schlae/HardDriveInfo/st225/20301/Analog.kicad_sch

## KiCad design st225/20301/Analog.kicad_sch (2024-07-07)

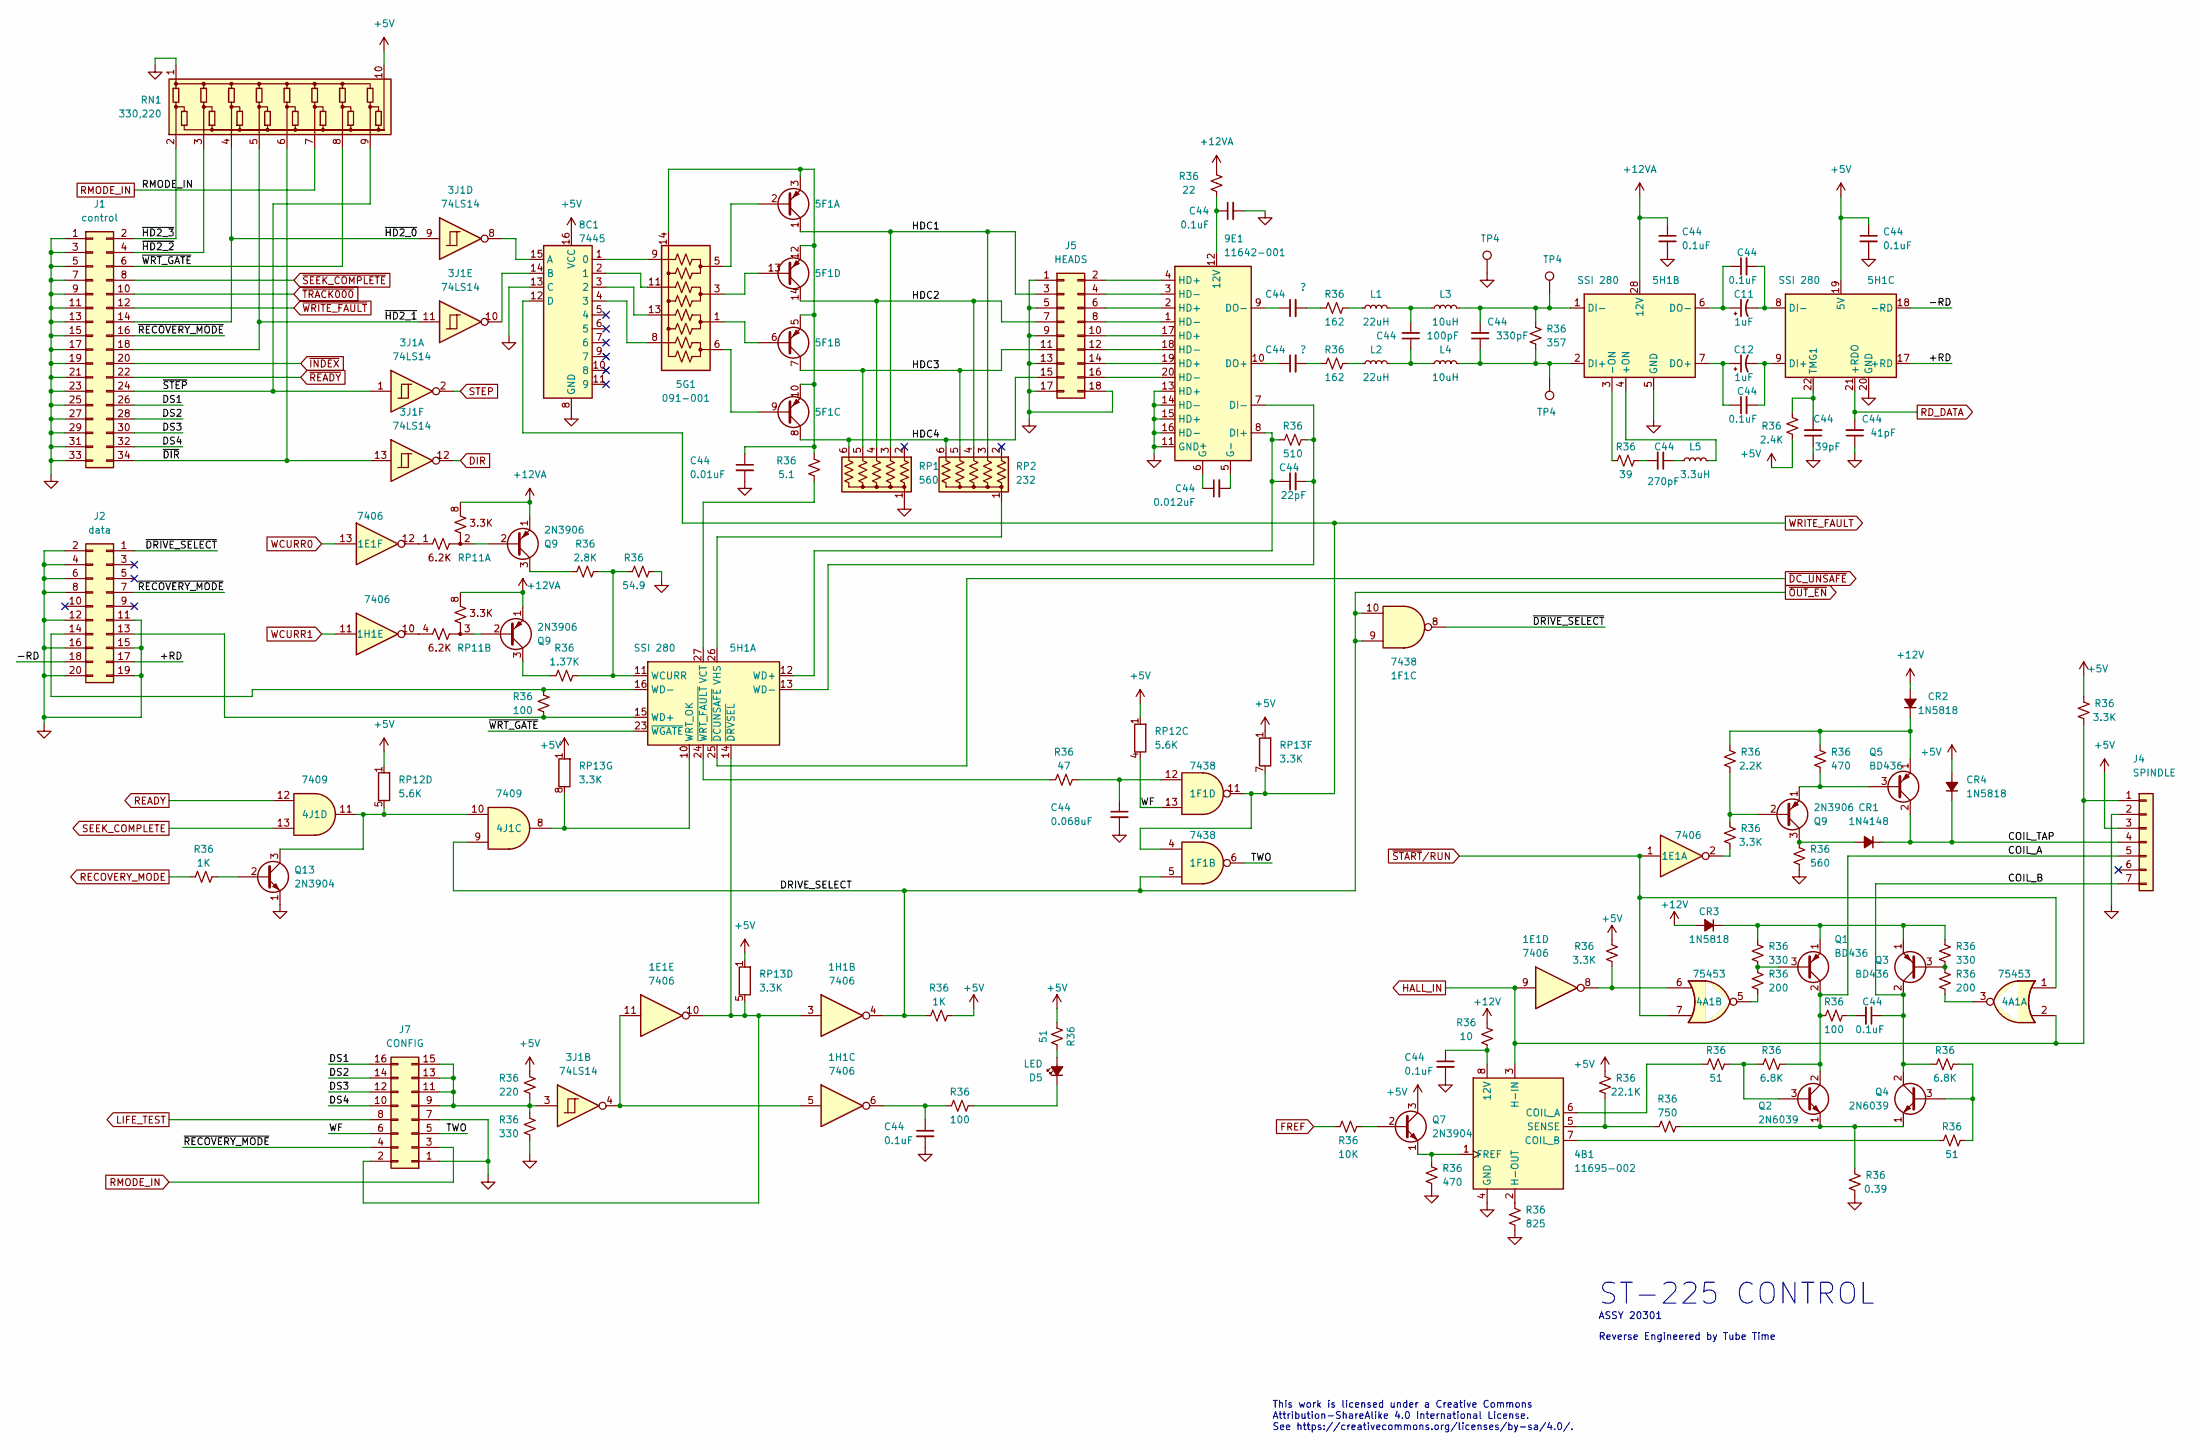
[picture p25: schematic Analog.kicad_sch]

Parts:
1E1, 1H1: 7406; DIP254P762X635-14
1F1: 7438; DIP254P762X635-14
3J1: 74LS14; DIP254P762X635-14
4A1: 75453; DIP254P762X635-8
4B1: 11695-002; DIP254P762X635-8
4J1: 7409; DIP254P762X635-14
5F1: DIP254P762X635-14
5G1: 091-001; DIP254P762X635-14
5H1: SSI 280; DIP254P1524X635-28
8C1: 7445; DIP254P762X635-16
9E1: 11642-001; DIP254P762X635-20
C11, C12: 1uF; C_Axial_L3.8mm_D2.6mm_P15.00mm_Horizontal
C44: 41pF; C_Axial_L3.8mm_D2.6mm_P10.00mm_Horizontal
CR1: 1N4148; D_DO-35_SOD27_P10.16mm_Horizontal
CR2, CR3, CR4: 1N5818; D_DO-35_SOD27_P10.16mm_Horizontal
D5: LED; PinHeader_1x02_P2.54mm_Vertical
J1: control; EDGE_34_100
J2: data; EDGE_20_100
J4: SPINDLE; PinHeader_1x07_P2.54mm_Vertical
J5: HEADS; PinHeader_2x09_P2.54mm_Horizontal
J7: CONFIG; PinHeader_2x08_P2.54mm_Horizontal
L1, L2: 22uH; L_Axial_L9.5mm_D4.0mm_P15.24mm_Horizontal_Fastron_SMCC
L3, L4: 10uH; L_Axial_L9.5mm_D4.0mm_P15.24mm_Horizontal_Fastron_SMCC
L5: 3.3uH; L_Axial_L9.5mm_D4.0mm_P15.24mm_Horizontal_Fastron_SMCC
Q1, Q3, Q5: BD436; TO-126-3_Horizontal_TabDown
Q2, Q4: 2N6039; TO-126-3_Horizontal_TabDown
Q7, Q13: 2N3904; TO-92_Wide_Reversed
Q9: 2N3906; TO-92_Wide_Reversed
R36: 2.4K; R_Axial_DIN0207_L6.3mm_D2.5mm_P10.16mm_Horizontal
RN1: 330,220; R_Array_SIP10
RP1: 560; R_Array_SIP6
RP2: 232; R_Array_SIP6
RP11: R_Array_SIP8
RP12: 5.6K; R_Array_SIP6
RP13: 3.3K; R_Array_SIP8
TP4: TestPoint; TestPoint_THTPad_1.5x1.5mm_Drill0.7mm

Connections:
+5V: 5H1.19 (5V), 8C1.16 (VCC), C44.1, CR4.2 (A), J4.3, Q7.3 (C), R36.1, R36.2, RN1.10 (COM2), RP12.1 (R1), RP13.1 (R1)
+12V: CR2.2 (A), CR3.2 (A), R36.1
+12VA: 5H1.28 (12V), C44.1, Q9.1 (E), R36.2, RP11.8
+RD: 5H1.17 (+RD), J2.17
-RD: 5H1.18 (-RD), J2.18
COIL_A: J4.5, Q1.2 (C), Q2.2 (C), R36.1, R36.2
COIL_B: C44.1, J4.7, Q3.2 (C), Q4.2 (C), R36.2
COIL_TAP: CR1.1 (K), CR4.1 (K), J4.4, Q5.2 (C)
DIR: 3J1.12
DS1: J1.26, J7.16
DS2: J1.28, J7.14
DS3: J1.30, J7.12
DS4: J1.32, J7.10
FREF: R36.2
GND: 4B1.4 (GND), 5H1.5 (GND), 5H1.20 (GND), 8C1.8 (GND), 8C1.13 (C), 9E1.11 (GND), 9E1.13 (HD+), 9E1.14 (HD-), 9E1.15 (HD+), 9E1.16 (HD-), C44.1, C44.2, J1.1, J1.3, J1.5, J1.7, J1.9, J1.11, J1.13, J1.15, J1.17, J1.19, J1.21, J1.23, J1.25, J1.27, J1.29, J1.31, J1.33, J2.2, J2.4, J2.6, J2.8, J2.11, J2.12, J2.15, J2.16, J2.19, J2.20, J4.2, J5.1, J5.5, J5.9, J5.13, J5.17, J5.18, J7.1, J7.7, Q13.1 (E), R36.1, R36.2, RN1.1 (COM1), RP1.1 (common), TP4.1
HALL_IN: 1E1.9, 4A1.2, 4B1.3 (H-IN), J4.1, R36.2
HDC1: 5F1.1 (C), J5.3, RP1.3 (R2), RP2.3 (R2)
HDC2: 5F1.14 (C), J5.7, RP1.4 (R3), RP2.4 (R3)
HDC3: 5F1.7 (C), J5.11, RP1.5 (R4), RP2.5 (R4)
HDC4: 5F1.8 (C), J5.15, RP1.6 (R5), RP2.6 (R5)
LIFE_TEST: J7.8
unnamed: 1E1.2, R36.2
unnamed: 1E1.8, 4A1.6, R36.2
unnamed: 1E1.10, 1H1.3, 5H1.14, J7.2, RP13.5 (R4.2)
unnamed: 1E1.11, 1H1.5, 3J1.4
unnamed: 1E1.12, RP11.1
unnamed: 1F1.12, C44.1, R36.1
unnamed: 1H1.6, C44.1, R36.2
unnamed: 1H1.10, RP11.4
unnamed: 3J1.3, J7.9, J7.11, J7.13, J7.15, R36.1, R36.2
unnamed: 3J1.8, 8C1.15 (A)
unnamed: 3J1.10, 8C1.14 (B)
unnamed: 4A1.3, R36.2
unnamed: 4A1.5, R36.2
unnamed: 4B1.1 (FREF), Q7.1 (E), R36.1
unnamed: 4B1.2 (H-OUT), R36.1
unnamed: 4B1.5 (SENSE), R36.2
unnamed: 4B1.6 (COIL_A), R36.2
unnamed: 4B1.7 (COIL_B), R36.2
unnamed: 4B1.8 (12V), C44.1, R36.2
unnamed: 4J1.8, 5H1.10, RP13.8 (R7.2)
unnamed: 4J1.10, 4J1.11, Q13.3 (C), RP12.5 (R4.2)
unnamed: 5F1.2 (B), 5G1.5
unnamed: 5F1.6 (B), 5G1.1
unnamed: 5F1.9 (B), 5G1.6
unnamed: 5F1.3 (E), 5F1.5 (E), 5F1.10 (E), 5F1.12 (E), 5G1.14 (9), C44.1, R36.2
unnamed: 5F1.13 (B), 5G1.3
unnamed: 5G1.8, 8C1.4 (3)
unnamed: 5G1.9, 8C1.1 (0)
unnamed: 5G1.11, 8C1.2 (1)
unnamed: 5G1.13, 8C1.3 (2)
unnamed: 5H1.1 (DI-), C44.2, L3.2, R36.1, TP4.1
unnamed: 5H1.2 (DI+), C44.1, L4.2, R36.2, TP4.1
unnamed: 5H1.3 (-ON), R36.2
unnamed: 5H1.4 (+ON), L5.2
unnamed: 5H1.6 (DO-), C11.1, C44.1
unnamed: 5H1.7 (DO+), C12.1, C44.1
unnamed: 5H1.8 (DI-), C11.2, C44.2
unnamed: 5H1.9 (DI+), C12.2, C44.2
unnamed: 5H1.11 (WC), R36.1, R36.2
unnamed: 5H1.12 (WD), 9E1.8 (DI+), C44.1, R36.2
unnamed: 5H1.13 (WD), 9E1.7 (DI-), C44.2, R36.1
unnamed: 5H1.15 (+WD), J2.13, R36.2
unnamed: 5H1.16 (-WD), J2.14, R36.1
unnamed: 5H1.22 (TMG1), C44.2, R36.1
unnamed: 5H1.24, R36.2
unnamed: 5H1.26 (VHS), RP2.1 (common)
unnamed: 5H1.27 (VCT), R36.1
unnamed: 9E1.1 (HD-), J5.8
unnamed: 9E1.2 (HD+), J5.6
unnamed: 9E1.3 (HD-), J5.4
unnamed: 9E1.4 (HD+), J5.2
unnamed: 9E1.5 (G-), C44.2
unnamed: 9E1.6 (G+), C44.1
unnamed: 9E1.9 (DO-), C44.1
unnamed: 9E1.10 (DO+), C44.1
unnamed: 9E1.12 (12V), C44.1, R36.1
unnamed: 9E1.17 (HD+), J5.10
unnamed: 9E1.18 (HD-), J5.12
unnamed: 9E1.19 (HD+), J5.14
unnamed: 9E1.20 (HD-), J5.16
unnamed: C44.1, L2.2, L4.1, L5.1
unnamed: C44.2, L1.2, L3.1, R36.1, R36.2
unnamed: CR1.2 (A), Q9.3 (C), R36.1
unnamed: CR2.1 (K), Q5.1 (E), R36.1
unnamed: CR3.1 (K), Q1.1 (E), Q3.1 (E), R36.1
unnamed: D5.1 (K), R36.1
unnamed: D5.2 (A), R36.1
unnamed: L1.1, R36.1
unnamed: L2.1, R36.1
unnamed: Q1.3 (B), R36.1, R36.2
unnamed: Q2.1 (E), Q4.1 (E), R36.1
unnamed: Q2.3 (B), R36.1, R36.2
unnamed: Q3.3 (B), R36.1, R36.2
unnamed: Q4.3 (B), R36.1
unnamed: Q5.3 (B), Q9.1 (E), R36.2
unnamed: Q7.2 (B), R36.1
unnamed: Q9.2 (B), R36.1, R36.2, RP11.2, RP11.3
unnamed: Q9.3 (C), R36.2
unnamed: Q13.2 (B), R36.1
RD_DATA: 5H1.21 (+RDO), C44.2
READY: 4J1.12
RECOVERY_MODE: R36.2
RMODE_IN: J7.3, RN1.7 (R6)
SEEK_COMPLETE: 4J1.13
STEP: 3J1.2
TWO: 1F1.6, J7.5
WCURR0: 1E1.13
WCURR1: 1H1.11
WF: 1F1.13, J7.6, RP12.4 (R3.2)
WRITE_FAULT: 1F1.4, 1F1.11, 8C1.12 (D), RP13.7 (R6.2)
~DC_UNSAFE: 5H1.25
~DIR: 3J1.13, J1.34, RN1.6 (R5)
~DRIVE_SELECT: 1F1.8, J2.1
~HD2_0: 3J1.9, J1.14, RN1.4 (R3)
~HD2_1: 3J1.11, J1.18, RN1.5 (R4)
~HD2_2: J1.4, RN1.3 (R2)
~HD2_3: J1.2, RN1.2 (R1)
~INDEX: J1.20
~OUT_EN: 1F1.5, 1F1.9, 1F1.10, 1H1.4, 4J1.9, R36.2
~READY: J1.22
~RECOVERY_MODE: J1.16, J2.7, J7.4
~SEEK_COMPLETE: J1.8
~START/RUN: 1E1.1, 4A1.1, 4A1.7
~STEP: 3J1.1, J1.24, RN1.9 (R8)
~TRACK000: J1.10
~WRITE_FAULT: J1.12
~WRT_GATE: 5H1.23 (~WG), J1.6, RN1.8 (R7)

Notes on the sheet:
ST-225 CONTROL
Reverse Engineered by Tube Time
ASSY 20301
This work is licensed under a Creative Commons Attribution-ShareAlike 4.0 International License. See https://creativecommons.org/licenses/by-sa/4.0/.
