schlae/HardDriveInfo/st225/20301/DigitalStepper.kicad_sch

## KiCad design st225/20301/DigitalStepper.kicad_sch (2024-07-07)

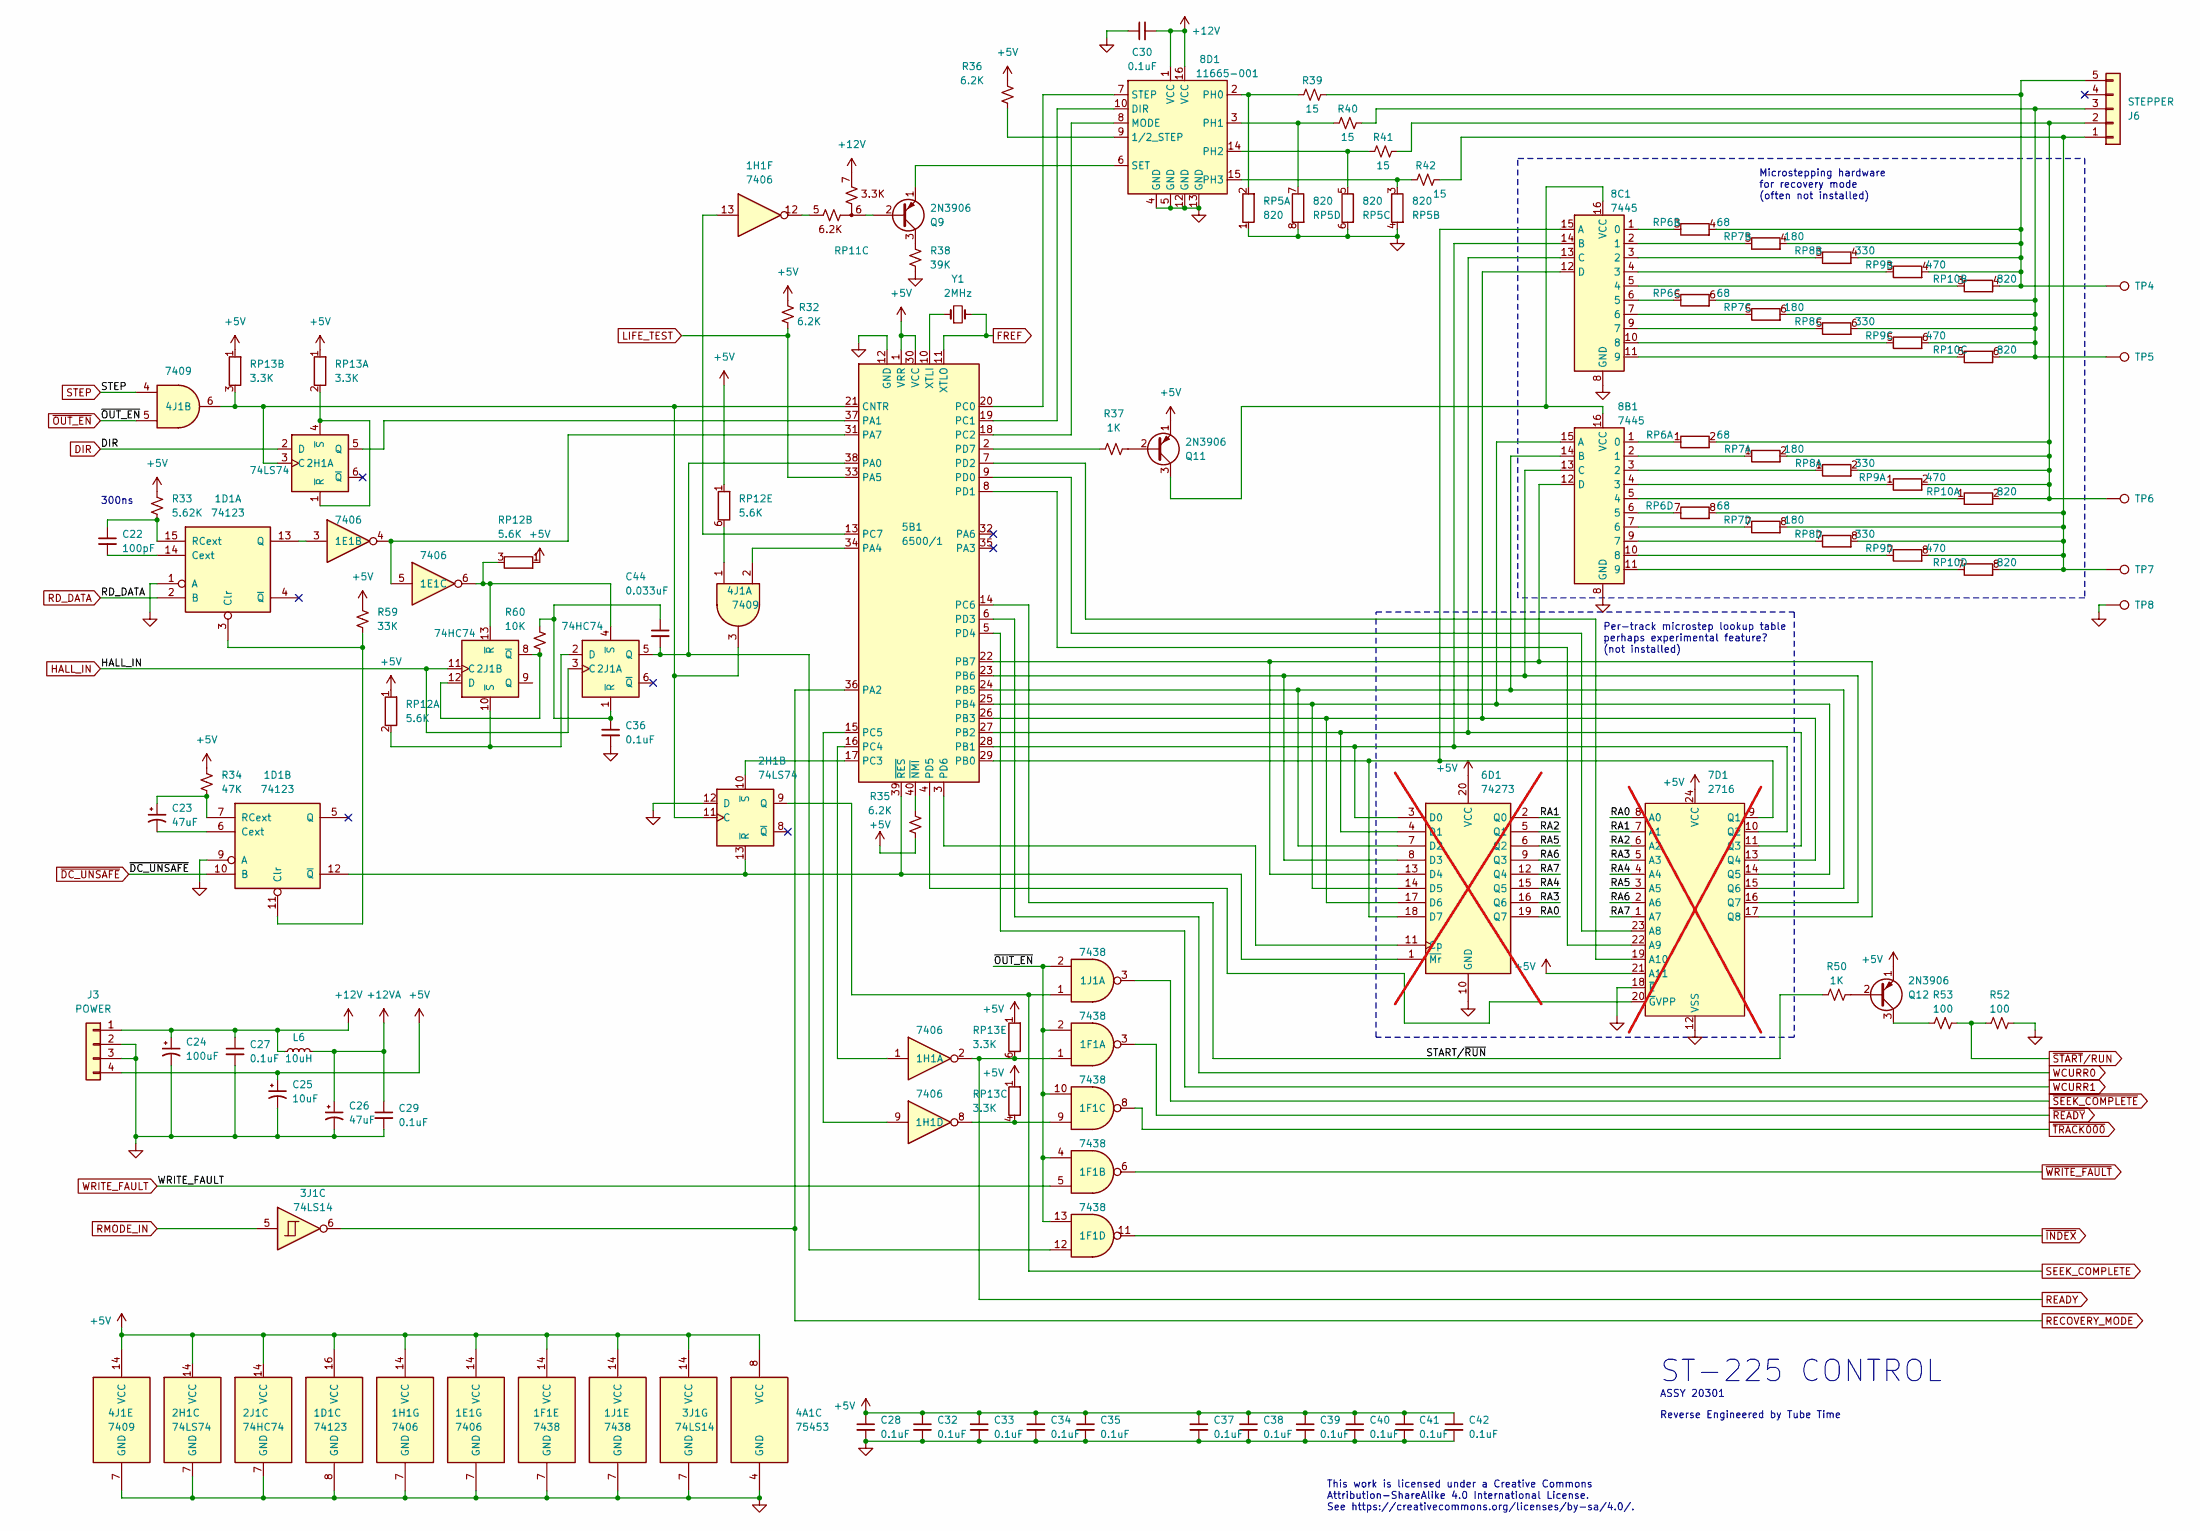
[picture p26: schematic DigitalStepper.kicad_sch]

Parts:
1D1: 74123; DIP254P762X635-16
1E1, 1H1: 7406; DIP254P762X635-14
1F1, 1J1: 7438; DIP254P762X635-14
2H1: 74LS74; DIP254P762X635-14
2J1: 74HC74; DIP254P762X635-14
3J1: 74LS14; DIP254P762X635-14
4A1: 75453; DIP254P762X635-8
4J1: 7409; DIP254P762X635-14
5B1: 6500/1; DIP254P1524X635-40
6D1: 74273; DIP254P762X635-20; not fitted
7D1: 2716; DIP254P1524X635-24; not fitted
8B1, 8C1: 7445; DIP254P762X635-16
8D1: 11665-001; DIP254P762X635-16
C22: 100pF; C_Axial_L3.8mm_D2.6mm_P10.00mm_Horizontal
C23, C26: 47uF; C_Axial_L5.1mm_D3.1mm_P15.00mm_Horizontal
C24: 100uF; C_Axial_L12.0mm_D6.5mm_P20.00mm_Horizontal
C25: 10uF; C_Axial_L5.1mm_D3.1mm_P15.00mm_Horizontal
C27, C28, C29, C30, C32, C33, C34, C35, C36, C37, C38, C39, C40, C41, C42: 0.1uF; C_Axial_L3.8mm_D2.6mm_P10.00mm_Horizontal
C44: 0.033uF; C_Axial_L3.8mm_D2.6mm_P10.00mm_Horizontal
J3: POWER; Samtec_HPM-04-01-x-S_Straight_1x04_Pitch5.08mm
J6: STEPPER; PinHeader_1x05_P2.54mm_Vertical
L6: 10uH; L_Axial_L9.5mm_D4.0mm_P15.24mm_Horizontal_Fastron_SMCC
Q9, Q11, Q12: 2N3906; TO-92_Wide_Reversed
R32, R35, R36: 6.2K; R_Axial_DIN0207_L6.3mm_D2.5mm_P10.16mm_Horizontal
R33: 5.62K; R_Axial_DIN0207_L6.3mm_D2.5mm_P10.16mm_Horizontal
R34: 47K; R_Axial_DIN0207_L6.3mm_D2.5mm_P10.16mm_Horizontal
R37, R50: 1K; R_Axial_DIN0207_L6.3mm_D2.5mm_P10.16mm_Horizontal
R38: 39K; R_Axial_DIN0207_L6.3mm_D2.5mm_P10.16mm_Horizontal
R39, R40, R41, R42: 15; R_Axial_DIN0309_L9.0mm_D3.2mm_P20.32mm_Horizontal
R52, R53: 100; R_Axial_DIN0207_L6.3mm_D2.5mm_P10.16mm_Horizontal
R59: 33K; R_Axial_DIN0207_L6.3mm_D2.5mm_P10.16mm_Horizontal
R60: 10K; R_Axial_DIN0204_L3.6mm_D1.6mm_P7.62mm_Horizontal
RP5, RP10: 820; R_Array_SIP8
RP6: 68; R_Array_SIP8
RP7: 180; R_Array_SIP8
RP8: 330; R_Array_SIP8
RP9: 470; R_Array_SIP8
RP11: R_Array_SIP8
RP12: 5.6K; R_Array_SIP6
RP13: 3.3K; R_Array_SIP8
TP4, TP5, TP6, TP7, TP8: TestPoint; TestPoint_THTPad_D1.5mm_Drill0.7mm
Y1: 2MHz; Crystal_HC49-U_Horizontal

Connections:
+5V: 1D1.16 (VCC), 1E1.14 (VCC), 1F1.14 (VCC), 1H1.14 (VCC), 1J1.14 (VCC), 2H1.14 (VCC), 2J1.14 (VCC), 3J1.14 (VCC), 4A1.8 (VCC), 4J1.14 (VCC), 5B1.1 (VRR), 5B1.30 (VCC), 6D1.20 (VCC), 7D1.21 (A11), 7D1.24 (VCC), C25.1, C28.1, C32.1, C33.1, C34.1, C35.1, C37.1, C38.1, C39.1, C40.1, C41.1, C42.1, J3.4, Q11.1 (E), Q12.1 (E), R32.1, R33.1, R34.1, R35.1, R36.2, R59.1, RP12.1 (R1), RP13.1 (R1)
+12V: 8D1.1 (VCC), 8D1.16 (VCC), C24.1, C27.1, C30.2, J3.1, L6.1, RP11.7
+12VA: C26.1, C29.1, L6.2
DIR: 2H1.2 (D)
FREF: 5B1.11 (XTLO), Y1.2
GND: 1D1.1 (A), 1D1.8 (GND), 1D1.9 (A), 1E1.7 (GND), 1F1.7 (GND), 1H1.7 (GND), 1J1.7 (GND), 2H1.7 (GND), 2H1.12 (D), 2J1.7 (GND), 3J1.7 (GND), 4A1.4 (GND), 4J1.7 (GND), 5B1.12 (GND), 6D1.10 (GND), 7D1.12 (VSS), 7D1.18 (~E), 8B1.8 (GND), 8C1.8 (GND), 8D1.4 (GND), 8D1.5 (GND), 8D1.12 (GND), 8D1.13 (GND), C24.2, C25.2, C26.2, C27.2, C28.2, C29.2, C30.1, C32.2, C33.2, C34.2, C35.2, C36.2, C37.2, C38.2, C39.2, C40.2, C41.2, C42.2, J3.2, J3.3, R38.2, R52.1, RP5.1 (R1.1), RP5.4 (R2.2), RP5.6 (R3.2), RP5.8 (R4.2), TP8.1
HALL_IN: 2J1.3 (C), 2J1.11 (C)
LIFE_TEST: 5B1.33 (PA5), R32.2
unnamed: 1D1.6 (Cext), C23.2
unnamed: 1D1.7 (RCext), C23.1, R34.2
unnamed: 1D1.3 (Clr), 1D1.11 (Clr), R59.2
unnamed: 1D1.12 (~Q), 2H1.13 (~R), 5B1.39 (~RES), 6D1.1 (~Mr)
unnamed: 1D1.13 (Q), 1E1.3
unnamed: 1D1.14 (Cext), C22.2
unnamed: 1D1.15 (RCext), C22.1, R33.2
unnamed: 1E1.4, 1E1.5, 5B1.31 (PA7)
unnamed: 1E1.6, 2J1.4 (~S), 2J1.13 (~R), RP12.3 (R2.2)
unnamed: 1F1.9, 1H1.8, RP13.4 (R3.2)
unnamed: 1F1.12, 2J1.5 (Q), 5B1.38 (PA0), C44.2
unnamed: 1H1.1, 5B1.16 (PC4)
unnamed: 1H1.9, 5B1.15 (PC5)
unnamed: 1H1.12, RP11.5
unnamed: 1H1.13, 5B1.13 (PC7)
unnamed: 2H1.1 (~R), 2H1.4 (~S), RP13.2 (R1.2)
unnamed: 2H1.5 (Q), 5B1.37 (PA1)
unnamed: 2H1.10 (~S), 5B1.17 (PC3)
unnamed: 2H1.3 (C), 2H1.11 (C), 4J1.3, 4J1.6, 5B1.21 (CNTR), RP13.3 (R2.2)
unnamed: 2J1.1 (~R), C36.1, C44.1, R60.1
unnamed: 2J1.2 (D), 2J1.10 (~S), RP12.2 (R1.2)
unnamed: 2J1.8 (~Q), 2J1.12 (D), R60.2
unnamed: 4J1.1, RP12.6 (R5.2)
unnamed: 4J1.2, 5B1.34 (PA4)
unnamed: 5B1.2 (PD7), R37.1
unnamed: 5B1.3 (PD6), 6D1.11 (Cp)
unnamed: 5B1.4 (PD5), 7D1.20 (~GVPP)
unnamed: 5B1.7 (PD2), 7D1.19 (A10)
unnamed: 5B1.8 (PD1), 7D1.22 (A9)
unnamed: 5B1.9 (PD0), 7D1.23 (A8)
unnamed: 5B1.10 (XTLI), Y1.1
unnamed: 5B1.18 (PC2), 8D1.8 (MODE)
unnamed: 5B1.19 (PC1), 8D1.10 (DIR)
unnamed: 5B1.20 (PC0), 8D1.7 (STEP)
unnamed: 5B1.22 (PB7), 6D1.13 (D4), 7D1.17 (Q8), 8B1.12 (D)
unnamed: 5B1.23 (PB6), 6D1.8 (D3), 7D1.16 (Q7), 8B1.13 (C)
unnamed: 5B1.24 (PB5), 6D1.7 (D2), 7D1.15 (Q6), 8B1.14 (B)
unnamed: 5B1.25 (PB4), 6D1.14 (D5), 7D1.14 (Q5), 8B1.15 (A)
unnamed: 5B1.26 (PB3), 6D1.17 (D6), 7D1.13 (Q4), 8C1.12 (D)
unnamed: 5B1.27 (PB2), 6D1.4 (D1), 7D1.11 (Q3), 8C1.13 (C)
unnamed: 5B1.28 (PB1), 6D1.3 (D0), 7D1.10 (Q2), 8C1.14 (B)
unnamed: 5B1.29 (PB0), 6D1.18 (D7), 7D1.9 (Q1), 8C1.15 (A)
unnamed: 5B1.40 (~NMI), R35.2
unnamed: 8B1.1 (0), RP6.1 (R1.1)
unnamed: 8B1.2 (1), RP7.1 (R1.1)
unnamed: 8B1.3 (2), RP8.1 (R1.1)
unnamed: 8B1.4 (3), RP9.1 (R1.1)
unnamed: 8B1.5 (4), RP10.1 (R1.1)
unnamed: 8B1.6 (5), RP6.7 (R4.1)
unnamed: 8B1.7 (6), RP7.7 (R4.1)
unnamed: 8B1.9 (7), RP8.7 (R4.1)
unnamed: 8B1.10 (8), RP9.7 (R4.1)
unnamed: 8B1.11 (9), RP10.7 (R4.1)
unnamed: 8B1.16 (VCC), 8C1.16 (VCC), Q11.3 (C)
unnamed: 8C1.1 (0), RP6.3 (R2.1)
unnamed: 8C1.2 (1), RP7.3 (R2.1)
unnamed: 8C1.3 (2), RP8.3 (R2.1)
unnamed: 8C1.4 (3), RP9.3 (R2.1)
unnamed: 8C1.5 (4), RP10.3 (R2.1)
unnamed: 8C1.6 (5), RP6.5 (R3.1)
unnamed: 8C1.7 (6), RP7.5 (R3.1)
unnamed: 8C1.9 (7), RP8.5 (R3.1)
unnamed: 8C1.10 (8), RP9.5 (R3.1)
unnamed: 8C1.11 (9), RP10.5 (R3.1)
unnamed: 8D1.2 (PH0), R39.1, RP5.2 (R1.2)
unnamed: 8D1.3 (PH1), R40.1, RP5.7 (R4.1)
unnamed: 8D1.6 (SET), Q9.1 (E)
unnamed: 8D1.9 (1/2_STEP), R36.1
unnamed: 8D1.14 (PH2), R41.1, RP5.5 (R3.1)
unnamed: 8D1.15 (PH3), R42.1, RP5.3 (R2.1)
unnamed: J6.1, R42.2, RP6.8 (R4.2), RP7.8 (R4.2), RP8.8 (R4.2), RP9.8 (R4.2), RP10.8 (R4.2), TP7.1
unnamed: J6.2, R41.2, RP6.2 (R1.2), RP7.2 (R1.2), RP8.2 (R1.2), RP9.2 (R1.2), RP10.2 (R1.2), TP6.1
unnamed: J6.3, R40.2, RP6.6 (R3.2), RP7.6 (R3.2), RP8.6 (R3.2), RP9.6 (R3.2), RP10.6 (R3.2), TP5.1
unnamed: J6.5, R39.2, RP6.4 (R2.2), RP7.4 (R2.2), RP8.4 (R2.2), RP9.4 (R2.2), RP10.4 (R2.2), TP4.1
unnamed: Q9.2 (B), RP11.6
unnamed: Q9.3 (C), R38.1
unnamed: Q11.2 (B), R37.2
unnamed: Q12.2 (B), R50.1
unnamed: Q12.3 (C), R53.2
RA0: 6D1.19 (Q7), 7D1.8 (A0)
RA1: 6D1.2 (Q0), 7D1.7 (A1)
RA2: 6D1.5 (Q1), 7D1.6 (A2)
RA3: 6D1.16 (Q6), 7D1.5 (A3)
RA4: 6D1.15 (Q5), 7D1.4 (A4)
RA5: 6D1.6 (Q2), 7D1.3 (A5)
RA6: 6D1.9 (Q3), 7D1.2 (A6)
RA7: 6D1.12 (Q4), 7D1.1 (A7)
RD_DATA: 1D1.2 (B)
READY: 1F1.1, 1H1.2, RP13.6 (R5.2)
RECOVERY_MODE: 3J1.6, 5B1.36 (PA2)
RMODE_IN: 3J1.5
SEEK_COMPLETE: 1J1.1, 2H1.9 (Q)
START/~RUN: 5B1.14 (PC6), R50.2
STEP: 4J1.4
WCURR0: 5B1.6 (PD3)
WCURR1: 5B1.5 (PD4)
WRITE_FAULT: 1F1.5
~DC_UNSAFE: 1D1.10 (B)
~INDEX: 1F1.11
~OUT_EN: 1F1.2, 1F1.4, 1F1.10, 1F1.13, 1J1.2, 4J1.5
~READY: 1F1.3
~SEEK_COMPLETE: 1J1.3
~START/RUN: R52.2, R53.1
~TRACK000: 1F1.8
~WRITE_FAULT: 1F1.6

Notes on the sheet:
Microstepping hardware for recovery mode (often not installed)
This work is licensed under a Creative Commons Attribution-ShareAlike 4.0 International License. See https://creativecommons.org/licenses/by-sa/4.0/.
ASSY 20301
300ns
Reverse Engineered by Tube Time
Per-track microstep lookup table perhaps experimental feature? (not installed)
ST-225 CONTROL
