schlae/HardDriveInfo/st225/20527/Analog.kicad_sch

## KiCad design st225/20527/Analog.kicad_sch (2024-06-30)

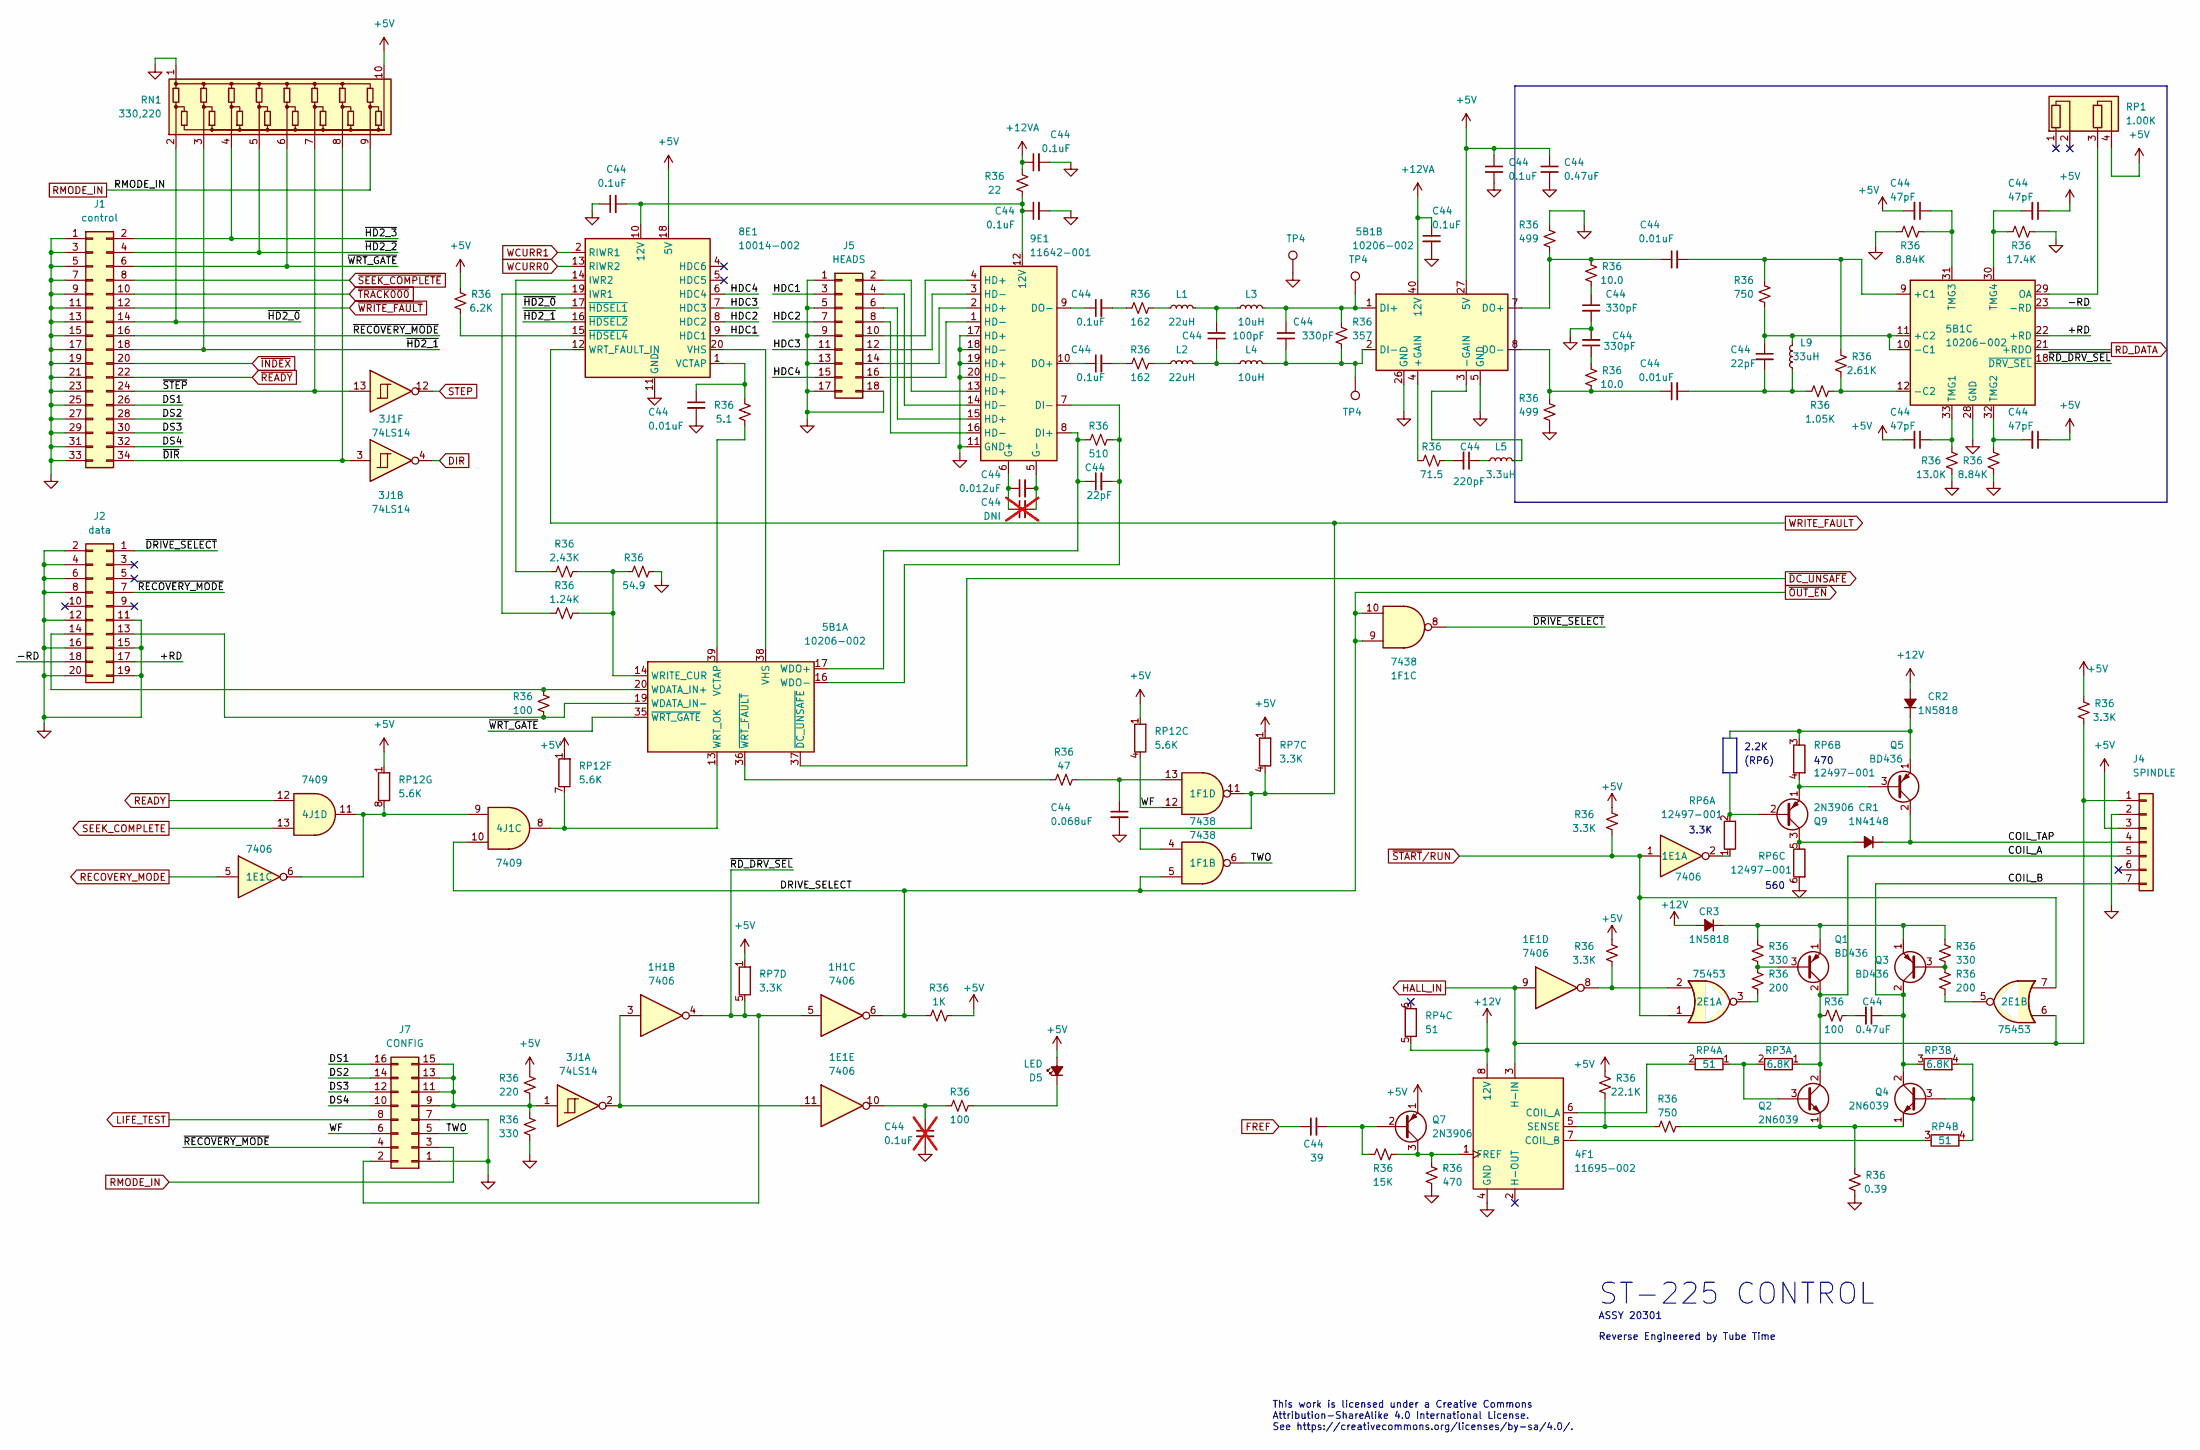
[picture p27: schematic Analog.kicad_sch]

Parts:
1E1, 1H1: 7406; DIP254P762X635-14
1F1: 7438; DIP254P762X635-14
2E1: 75453; DIP254P762X635-8
3J1: 74LS14; DIP254P762X635-14
4F1: 11695-002; DIP254P762X635-8
4J1: 7409; DIP254P762X635-14
5B1: 10206-002; DIP254P1524X635-40
8E1: 10014-002; DIP254P762X635-20
9E1: 11642-001; DIP254P762X635-20
C44: 47pF; C_Axial_L3.8mm_D2.6mm_P10.00mm_Horizontal
CR1: 1N4148; D_DO-35_SOD27_P10.16mm_Horizontal
CR2, CR3: 1N5818; D_DO-35_SOD27_P10.16mm_Horizontal
D5: LED; PinHeader_1x02_P2.54mm_Vertical
J1: control; EDGE_34_100
J2: data; EDGE_20_100
J4: SPINDLE; PinHeader_1x07_P2.54mm_Vertical
J5: HEADS; PinHeader_2x09_P2.54mm_Horizontal
J7: CONFIG; PinHeader_2x08_P2.54mm_Horizontal
L1, L2: 22uH; L_Axial_L9.5mm_D4.0mm_P15.24mm_Horizontal_Fastron_SMCC
L3, L4: 10uH; L_Axial_L9.5mm_D4.0mm_P15.24mm_Horizontal_Fastron_SMCC
L5: 3.3uH; L_Axial_L9.5mm_D4.0mm_P12.70mm_Horizontal_Fastron_SMCC
L9: 33uH; L_Axial_L9.5mm_D4.0mm_P15.24mm_Horizontal_Fastron_SMCC
Q1, Q3, Q5: BD436; TO-126-3_Horizontal_TabDown
Q2, Q4: 2N6039; TO-126-3_Horizontal_TabDown
Q7, Q9: 2N3906; TO-92L_Inline_Wide
R36: 13.0K; R_Axial_DIN0207_L6.3mm_D2.5mm_P10.16mm_Horizontal
RN1: 330,220; R_Array_SIP10
RP1: 1.00K; R_Array_SIP4
RP3: 6.8K; R_Array_SIP4
RP4: 51; R_Array_SIP6
RP6: 12497-001; R_Array_SIP6
RP7: 3.3K; R_Array_SIP6
RP12: 5.6K; R_Array_SIP8
TP4: TestPoint; TestPoint_THTPad_1.5x1.5mm_Drill0.7mm

Connections:
+5V: 5B1.27 (5V), 8E1.18 (5V), C44.1, C44.2, D5.2 (A), J4.3, Q7.1 (E), R36.1, RN1.10 (COM2), RP1.4 (R2.2), RP7.1 (R1), RP12.1 (R1)
+12V: 4F1.8 (12V), CR2.2 (A), CR3.2 (A), RP4.5 (R3.1)
+12VA: 5B1.40 (12V), C44.1, R36.2
+RD: 5B1.22 (+RD), J2.17
-RD: 5B1.23 (-RD), J2.18
COIL_A: J4.5, Q1.2 (C), Q2.2 (C), R36.2, RP3.1 (R1.1)
COIL_B: C44.1, J4.7, Q3.2 (C), Q4.2 (C), RP3.3 (R2.1)
COIL_TAP: CR1.1 (K), J4.4, Q5.2 (C)
DIR: 3J1.4
DS1: J1.26, J7.16
DS2: J1.28, J7.14
DS3: J1.30, J7.12
DS4: J1.32, J7.10
FREF: C44.1
GND: 4F1.4 (GND), 5B1.5 (GND), 5B1.26 (GND), 5B1.28 (GND), 8E1.11 (GND), 9E1.11 (GND), 9E1.17 (HD+), 9E1.18 (HD-), 9E1.19 (HD+), 9E1.20 (HD-), C44.1, C44.2, J1.1, J1.3, J1.5, J1.7, J1.9, J1.11, J1.13, J1.15, J1.17, J1.19, J1.21, J1.23, J1.25, J1.27, J1.29, J1.31, J1.33, J2.2, J2.4, J2.6, J2.8, J2.11, J2.12, J2.15, J2.16, J2.19, J2.20, J4.2, J5.1, J5.5, J5.9, J5.13, J5.17, J5.18, J7.1, J7.7, R36.1, R36.2, RN1.1 (COM1), RP6.6 (R3.2), TP4.1
HALL_IN: 1E1.9, 2E1.6, 4F1.3 (H-IN), J4.1, R36.2
HDC1: 8E1.9 (HDC1), J5.3
HDC2: 8E1.8 (HDC2), J5.7
HDC3: 8E1.7 (HDC3), J5.11
HDC4: 8E1.6 (HDC4), J5.15
LIFE_TEST: J7.8
unnamed: 1E1.2, RP6.1 (R1.1)
unnamed: 1E1.6, 4J1.9, 4J1.11, RP12.8 (R7.2)
unnamed: 1E1.8, 2E1.2, R36.2
unnamed: 1E1.10, C44.1, R36.2
unnamed: 1E1.11, 1H1.3, 3J1.2
unnamed: 1F1.13, C44.1, R36.1
unnamed: 2E1.3, R36.2
unnamed: 2E1.5, R36.2
unnamed: 3J1.1, J7.9, J7.11, J7.13, J7.15, R36.1, R36.2
unnamed: 4F1.1 (FREF), Q7.3 (C), R36.1
unnamed: 4F1.5 (SENSE), R36.2
unnamed: 4F1.6 (COIL_A), RP4.2 (R1.2)
unnamed: 4F1.7 (COIL_B), RP4.3 (R2.1)
unnamed: 4J1.8, 5B1.13 (WRT_OK), RP12.7 (R6.2)
unnamed: 5B1.1 (DI+), C44.2, L3.2, R36.1, TP4.1
unnamed: 5B1.2 (DI-), C44.1, L4.2, R36.2, TP4.1
unnamed: 5B1.3 (-GAIN), L5.2
unnamed: 5B1.4 (+GAIN), R36.2
unnamed: 5B1.7 (DO+), C44.1, R36.1, R36.2
unnamed: 5B1.8 (DO-), C44.1, R36.1
unnamed: 5B1.9 (+C1), C44.2, R36.1
unnamed: 5B1.10 (-C1), 5B1.11 (+C2), C44.1, L9.2, R36.2
unnamed: 5B1.12 (-C2), R36.1, R36.2
unnamed: 5B1.14 (WRITE_CUR), R36.1, R36.2
unnamed: 5B1.16 (WDO-), 9E1.7 (DI-), C44.2, R36.1
unnamed: 5B1.17 (WDO+), 9E1.8 (DI+), C44.1, R36.2
unnamed: 5B1.19 (WDATA_IN-), J2.13, R36.2
unnamed: 5B1.20 (WDATA_IN+), J2.14, R36.1
unnamed: 5B1.29 (OA), RP1.3 (R2.1)
unnamed: 5B1.30 (TMG4), C44.2, R36.1
unnamed: 5B1.31 (TMG3), C44.1, R36.2
unnamed: 5B1.32 (TMG2), C44.2, R36.1
unnamed: 5B1.33 (TMG1), C44.1, R36.1
unnamed: 5B1.36 (~WRT_FAULT), R36.2
unnamed: 5B1.38 (VHS), 8E1.20 (VHS)
unnamed: 5B1.39 (VCTAP), R36.1
unnamed: 8E1.1 (VCTAP), C44.1, R36.2
unnamed: 8E1.10 (12V), 9E1.12 (12V), C44.1, C44.2, R36.1
unnamed: 8E1.14 (IWR2), R36.2
unnamed: 8E1.15 (~HDSEL4), R36.2
unnamed: 8E1.19 (IWR1), R36.2
unnamed: 9E1.1 (HD-), J5.16
unnamed: 9E1.2 (HD+), J5.14
unnamed: 9E1.3 (HD-), J5.12
unnamed: 9E1.4 (HD+), J5.10
unnamed: 9E1.5 (G-), C44.2
unnamed: 9E1.6 (G+), C44.1
unnamed: 9E1.9 (DO-), C44.1
unnamed: 9E1.10 (DO+), C44.1
unnamed: 9E1.13 (HD+), J5.2
unnamed: 9E1.14 (HD-), J5.4
unnamed: 9E1.15 (HD+), J5.6
unnamed: 9E1.16 (HD-), J5.8
unnamed: C44.1, L2.2, L4.1, L5.1, R36.2
unnamed: C44.2, L1.2, L3.1, L9.1, Q7.2 (B), R36.1, R36.2
unnamed: CR1.2 (A), Q9.3 (C), RP6.5 (R3.1)
unnamed: CR2.1 (K), Q5.1 (E), RP6.3 (R2.1)
unnamed: CR3.1 (K), Q1.1 (E), Q3.1 (E), R36.1
unnamed: D5.1 (K), R36.1
unnamed: L1.1, R36.1
unnamed: L2.1, R36.1
unnamed: Q1.3 (B), R36.1, R36.2
unnamed: Q2.1 (E), Q4.1 (E), R36.1
unnamed: Q2.3 (B), RP3.2 (R1.2), RP4.1 (R1.1)
unnamed: Q3.3 (B), R36.1, R36.2
unnamed: Q4.3 (B), RP3.4 (R2.2), RP4.4 (R2.2)
unnamed: Q5.3 (B), Q9.1 (E), RP6.4 (R2.2)
unnamed: Q9.2 (B), RP6.2 (R1.2)
RD_DATA: 5B1.21 (+RDO)
READY: 4J1.12
RECOVERY_MODE: 1E1.5
RMODE_IN: J7.3, RN1.9 (R8)
SEEK_COMPLETE: 4J1.13
STEP: 3J1.12
TWO: 1F1.6, J7.5
WCURR0: 8E1.13 (RIWR2)
WCURR1: 8E1.2 (RIWR1)
WF: 1F1.12, J7.6, RP12.4 (R3.2)
WRITE_FAULT: 1F1.4, 1F1.11, 8E1.12 (WRT_FAULT_IN), RP7.4 (R3.2)
~DC_UNSAFE: 5B1.37 (~DC_UNSAFE)
~DIR: 3J1.3, J1.34, RN1.8 (R7)
~DRIVE_SELECT: 1F1.8, J2.1
~HD2_0: 8E1.17 (~HDSEL1), J1.14, RN1.2 (R1)
~HD2_1: 8E1.16 (~HDSEL2), J1.18, RN1.3 (R2)
~HD2_2: J1.4, RN1.5 (R4)
~HD2_3: J1.2, RN1.4 (R3)
~INDEX: J1.20
~OUT_EN: 1F1.5, 1F1.9, 1F1.10, 1H1.6, 4J1.10, R36.2
~RD_DRV_SEL: 1H1.4, 1H1.5, 5B1.18 (~DRV_SEL), J7.2, RP7.5 (R4.2)
~READY: J1.22
~RECOVERY_MODE: J1.16, J2.7, J7.4
~SEEK_COMPLETE: J1.8
~START/RUN: 1E1.1, 2E1.1, 2E1.7, R36.2
~STEP: 3J1.13, J1.24, RN1.7 (R6)
~TRACK000: J1.10
~WRITE_FAULT: J1.12
~WRT_GATE: 5B1.35 (~WRT_GATE), J1.6, RN1.6 (R5)

Notes on the sheet:
ST-225 CONTROL
(RP6)
Reverse Engineered by Tube Time
470
ASSY 20301
3.3K
This work is licensed under a Creative Commons Attribution-ShareAlike 4.0 International License. See https://creativecommons.org/licenses/by-sa/4.0/.
2.2K
560
