schlae/HardDriveInfo/st225/20527/DigitalStepper.kicad_sch

## KiCad design st225/20527/DigitalStepper.kicad_sch (2024-07-05)

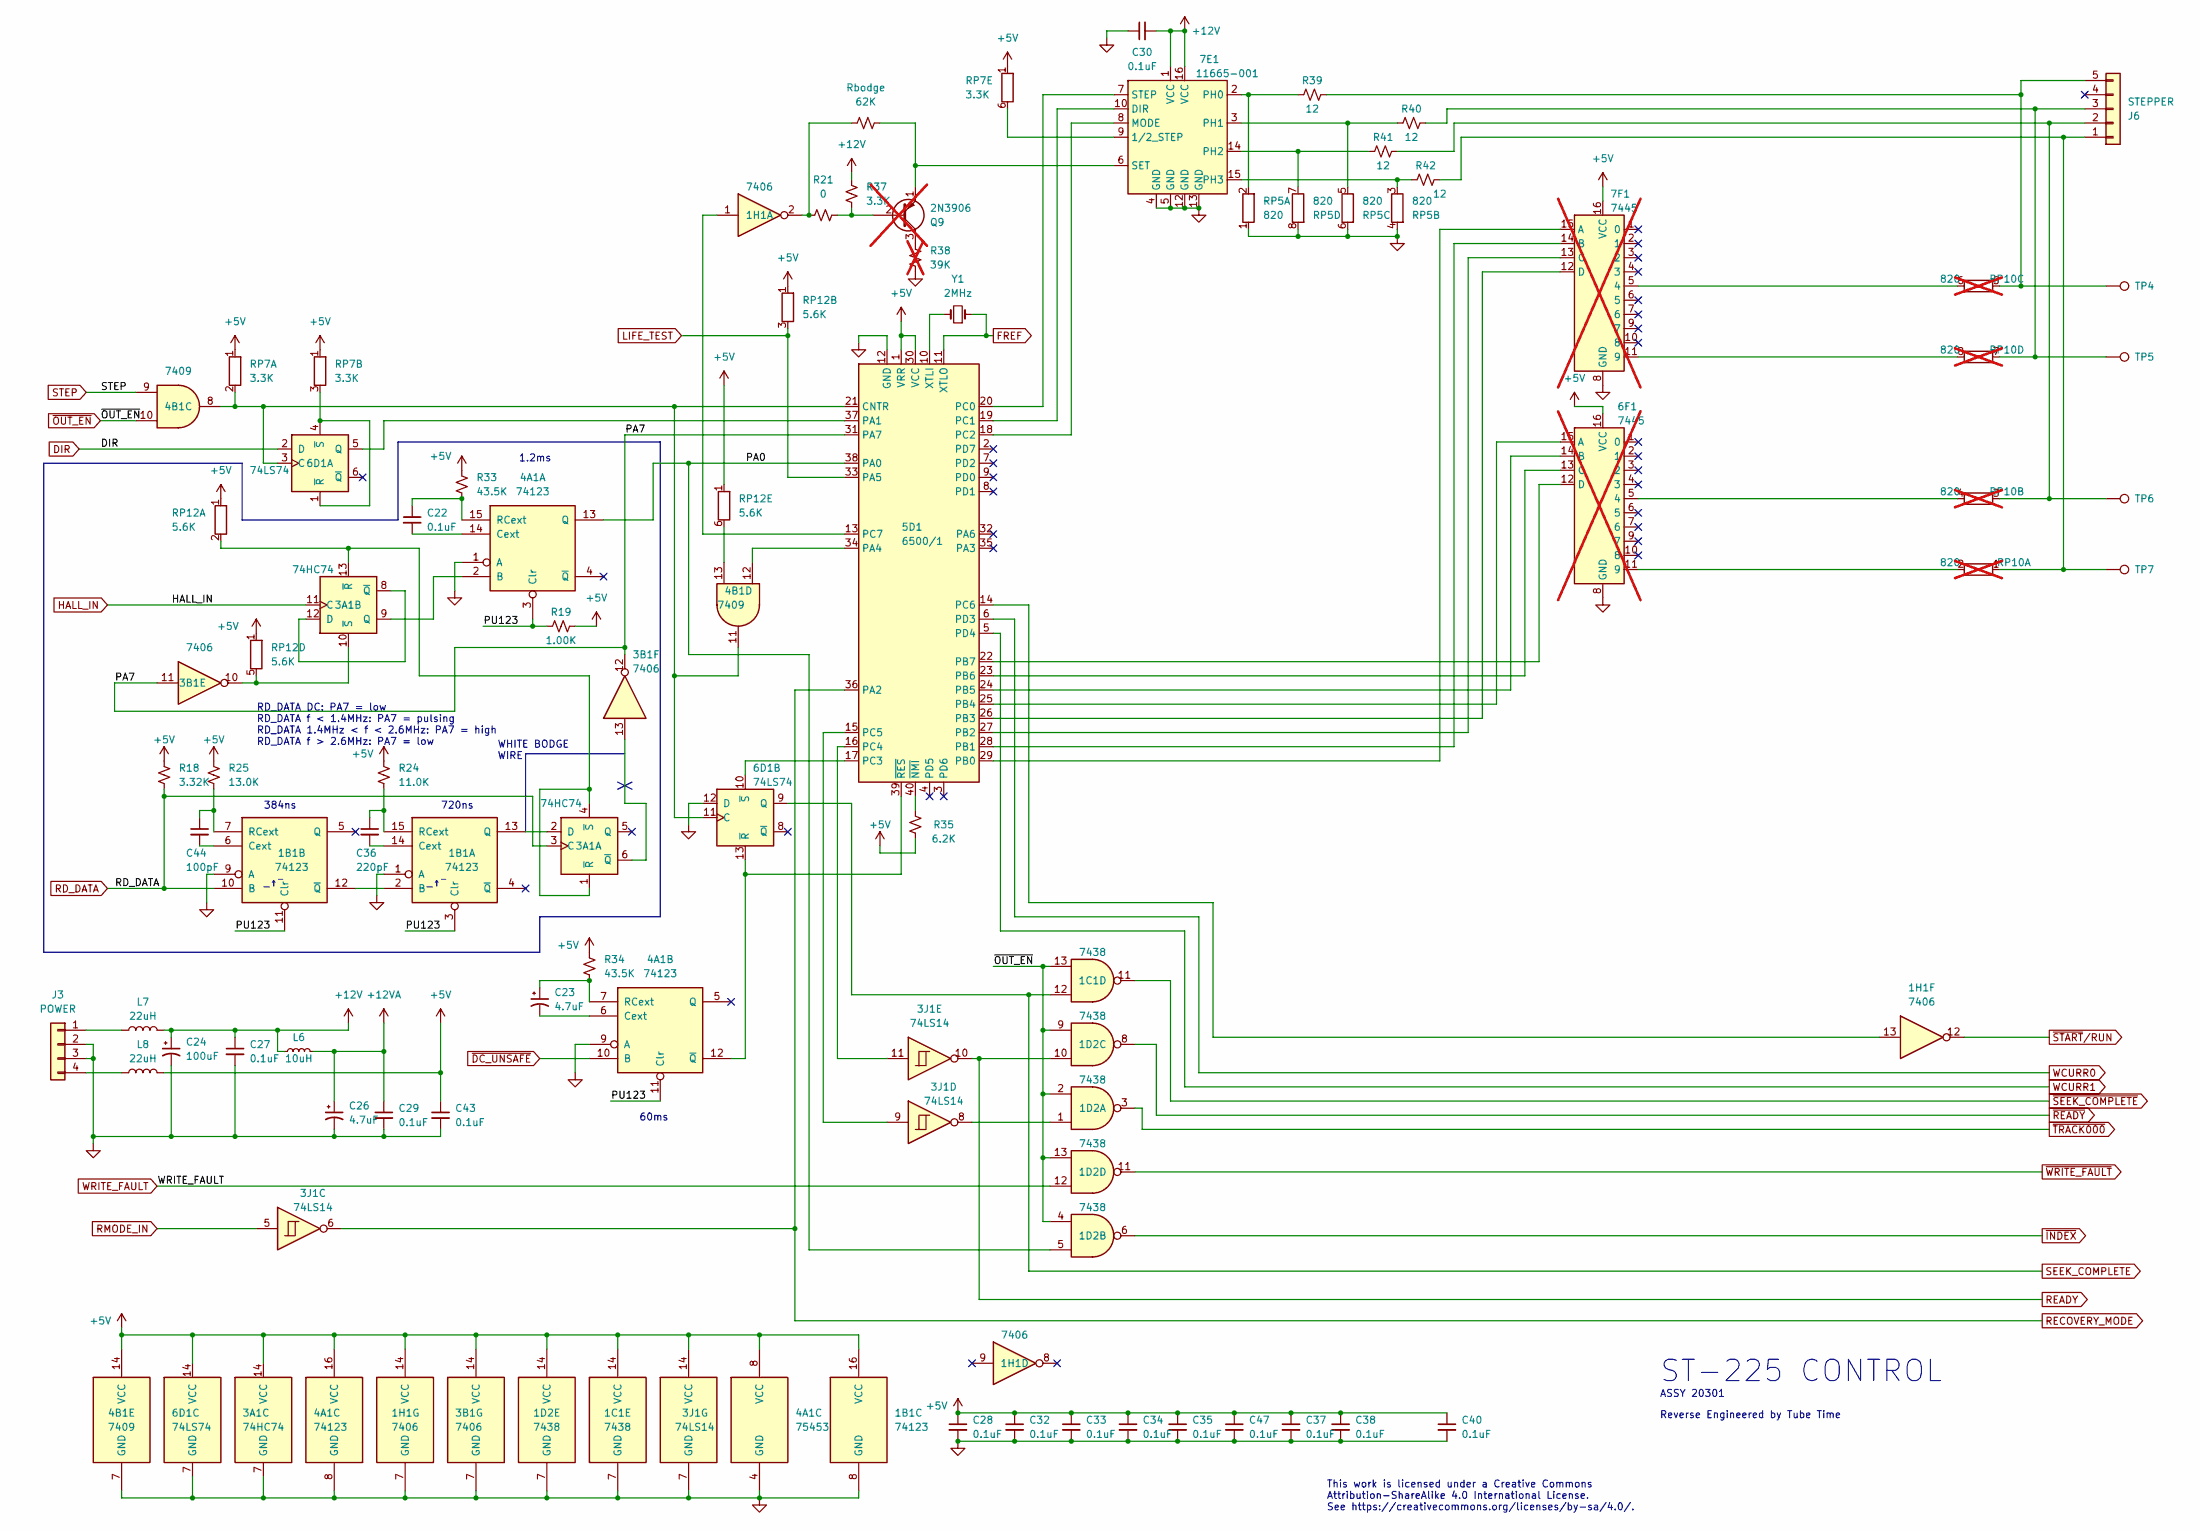
[picture p28: schematic DigitalStepper.kicad_sch]

Parts:
1B1, 4A1: 74123; DIP254P762X635-16
1C1, 1D2: 7438; DIP254P762X635-14
1H1, 3B1: 7406; DIP254P762X635-14
3A1: 74HC74; DIP254P762X635-14
3J1: 74LS14; DIP254P762X635-14
4B1: 7409; DIP254P762X635-14
5D1: 6500/1; DIP254P1524X635-40
6D1: 74LS74; DIP254P762X635-14
6F1, 7F1: 7445; DIP254P762X635-16; not fitted
7E1: 11665-001; DIP254P762X635-16
C22, C28, C29, C32, C33, C34, C35: 0.1uF; C_Rect_L7.0mm_W2.0mm_P5.00mm
C23, C26: 4.7uF; CP_Radial_D5.0mm_P2.50mm
C24: 100uF; C_Axial_L12.0mm_D6.5mm_P20.00mm_Horizontal
C27, C37, C38, C40, C43, C47: 0.1uF; C_Axial_L3.8mm_D2.6mm_P10.00mm_Horizontal
C30: 0.1uF; C_Rect_L7.0mm_W2.5mm_P5.00mm
C36: 220pF; C_Rect_L7.0mm_W2.0mm_P5.00mm
C44: 100pF; C_Rect_L7.0mm_W2.0mm_P5.00mm
J3: POWER; Samtec_HPM-04-01-x-S_Straight_1x04_Pitch5.08mm
J6: STEPPER; PinHeader_1x05_P2.54mm_Vertical
L6: 10uH; L_Axial_L9.5mm_D4.0mm_P15.24mm_Horizontal_Fastron_SMCC
L7, L8: 22uH; L_Axial_L13.0mm_D4.5mm_P15.24mm_Horizontal_Fastron_HCCC
Q9: 2N3906; TO-92L_Inline_Wide; not fitted
R18: 3.32K; R_Axial_DIN0204_L3.6mm_D1.6mm_P7.62mm_Horizontal
R19: 1.00K; R_Axial_DIN0204_L3.6mm_D1.6mm_P7.62mm_Horizontal
R21: 0; R_Axial_DIN0207_L6.3mm_D2.5mm_P10.16mm_Horizontal
R24: 11.0K; R_Axial_DIN0207_L6.3mm_D2.5mm_P7.62mm_Horizontal
R25: 13.0K; R_Axial_DIN0207_L6.3mm_D2.5mm_P7.62mm_Horizontal
R33, R34: 43.5K; R_Axial_DIN0207_L6.3mm_D2.5mm_P7.62mm_Horizontal
R35: 6.2K; R_Axial_DIN0207_L6.3mm_D2.5mm_P10.16mm_Horizontal
R37: 3.3K; R_Axial_DIN0207_L6.3mm_D2.5mm_P10.16mm_Horizontal
R38: 39K; R_Axial_DIN0207_L6.3mm_D2.5mm_P10.16mm_Horizontal; not fitted
R39, R40, R41, R42: 12; R_Axial_DIN0309_L9.0mm_D3.2mm_P20.32mm_Horizontal
RP5: 820; R_Array_SIP8
RP7: 3.3K; R_Array_SIP6
RP10: 820; R_Array_SIP8; not fitted
RP12: 5.6K; R_Array_SIP8
Rbodge: 62K; R_Axial_DIN0207_L6.3mm_D2.5mm_P10.16mm_Horizontal
TP4, TP5, TP6, TP7: TestPoint; TestPoint_THTPad_D1.5mm_Drill0.7mm
Y1: 2MHz; Crystal_HC49-U_Horizontal

Connections:
+5V: 1B1.16 (VCC), 1C1.14 (VCC), 1D2.14 (VCC), 1H1.14 (VCC), 3A1.14 (VCC), 3B1.14 (VCC), 3J1.14 (VCC), 4A1.8 (GND), 4A1.16 (VCC), 4B1.14 (VCC), 5D1.1 (VRR), 5D1.30 (VCC), 6D1.14 (VCC), 6F1.16 (VCC), 7F1.16 (VCC), C28.1, C32.1, C33.1, C34.1, C35.1, C37.1, C38.1, C40.1, C43.1, C47.1, L8.2, R18.1, R19.1, R24.1, R25.1, R33.1, R34.1, R35.1, RP7.1 (R1), RP12.1 (R1)
+12V: 7E1.1 (VCC), 7E1.16 (VCC), C24.1, C27.1, C30.2, L6.1, L7.2, R37.2
+12VA: C26.1, C29.1, L6.2
DIR: 6D1.2 (D)
FREF: 5D1.11 (XTLO), Y1.1
GND: 1B1.1 (A), 1B1.8 (GND), 1B1.9 (A), 1C1.7 (GND), 1D2.7 (GND), 1H1.7 (GND), 3A1.7 (GND), 3B1.7 (GND), 3J1.7 (GND), 4A1.1 (A), 4A1.4 (~Q), 4A1.8 (GND), 4A1.9 (A), 4B1.7 (GND), 5D1.12 (GND), 6D1.7 (GND), 6D1.12 (D), 6F1.8 (GND), 7E1.4 (GND), 7E1.5 (GND), 7E1.12 (GND), 7E1.13 (GND), 7F1.8 (GND), C24.2, C26.2, C27.2, C28.2, C29.2, C30.1, C32.2, C33.2, C34.2, C35.2, C37.2, C38.2, C40.2, C43.2, C47.2, J3.2, J3.3, R38.2, RP5.1 (R1.1), RP5.4 (R2.2), RP5.6 (R3.2), RP5.8 (R4.2)
HALL_IN: 3A1.11 (C)
LIFE_TEST: 5D1.33 (PA5), RP12.3 (R2.2)
unnamed: 1B1.6 (Cext), C44.2
unnamed: 1B1.7 (RCext), C44.1, R25.2
unnamed: 1B1.2 (B), 1B1.12 (~Q)
unnamed: 1B1.13 (Q), 3A1.2 (D)
unnamed: 1B1.14 (Cext), C36.2
unnamed: 1B1.15 (RCext), C36.1, R24.2
unnamed: 1D2.1, 3J1.8
unnamed: 1H1.1, 5D1.13 (PC7)
unnamed: 1H1.2, R21.1, Rbodge.1
unnamed: 1H1.13, 5D1.14 (PC6)
unnamed: 3A1.1 (~R), 3A1.4 (~S), 3A1.13 (~R), RP12.2 (R1.2)
unnamed: 3A1.6 (~Q), 3B1.13
unnamed: 3A1.9 (Q), 4A1.2 (B)
unnamed: 3A1.10 (~S), 3B1.10, RP12.5 (R4.2)
unnamed: 3A1.8 (~Q), 3A1.12 (D)
unnamed: 3J1.9, 5D1.15 (PC5)
unnamed: 3J1.11, 5D1.16 (PC4)
unnamed: 4A1.6 (Cext), C23.2
unnamed: 4A1.7 (RCext), C23.1, R34.2
unnamed: 4A1.12 (~Q), 5D1.39 (~RES), 6D1.13 (~R)
unnamed: 4A1.14 (Cext), C22.2
unnamed: 4A1.15 (RCext), C22.1, R33.2
unnamed: 4B1.8, 4B1.11, 5D1.21 (CNTR), 6D1.3 (C), 6D1.11 (C), RP7.2 (R1.2)
unnamed: 4B1.12, 5D1.34 (PA4)
unnamed: 4B1.13, RP12.6 (R5.2)
unnamed: 5D1.10 (XTLI), Y1.2
unnamed: 5D1.17 (PC3), 6D1.10 (~S)
unnamed: 5D1.18 (PC2), 7E1.8 (MODE)
unnamed: 5D1.19 (PC1), 7E1.10 (DIR)
unnamed: 5D1.20 (PC0), 7E1.7 (STEP)
unnamed: 5D1.22 (PB7), 6F1.12 (D)
unnamed: 5D1.23 (PB6), 6F1.13 (C)
unnamed: 5D1.24 (PB5), 6F1.14 (B)
unnamed: 5D1.25 (PB4), 6F1.15 (A)
unnamed: 5D1.26 (PB3), 7F1.12 (D)
unnamed: 5D1.27 (PB2), 7F1.13 (C)
unnamed: 5D1.28 (PB1), 7F1.14 (B)
unnamed: 5D1.29 (PB0), 7F1.15 (A)
unnamed: 5D1.37 (PA1), 6D1.5 (Q)
unnamed: 5D1.40 (~NMI), R35.2
unnamed: 6D1.1 (~R), 6D1.4 (~S), RP7.3 (R2.2)
unnamed: 6F1.5 (4), RP10.4 (R2.2)
unnamed: 6F1.11 (9), RP10.2 (R1.2)
unnamed: 7E1.2 (PH0), R39.1, RP5.2 (R1.2)
unnamed: 7E1.3 (PH1), R40.1, RP5.5 (R3.1)
unnamed: 7E1.6 (SET), Q9.1 (E), Rbodge.2
unnamed: 7E1.9 (1/2_STEP), RP7.6 (R5.2)
unnamed: 7E1.14 (PH2), R41.1, RP5.7 (R4.1)
unnamed: 7E1.15 (PH3), R42.1, RP5.3 (R2.1)
unnamed: 7F1.5 (4), RP10.6 (R3.2)
unnamed: 7F1.11 (9), RP10.8 (R4.2)
unnamed: J3.1, L7.1
unnamed: J3.4, L8.1
unnamed: J6.1, R42.2, RP10.1 (R1.1), TP7.1
unnamed: J6.2, R41.2, RP10.3 (R2.1), TP6.1
unnamed: J6.3, R40.2, RP10.7 (R4.1), TP5.1
unnamed: J6.5, R39.2, RP10.5 (R3.1), TP4.1
unnamed: Q9.2 (B), R21.2, R37.1
unnamed: Q9.3 (C), R38.1
PA0: 1D2.5, 4A1.13 (Q), 5D1.38 (PA0)
PA7: 3B1.11, 3B1.12, 5D1.31 (PA7)
PU123: 1B1.3 (Clr), 1B1.11 (Clr), 4A1.3 (Clr), 4A1.11 (Clr), R19.2
RD_DATA: 1B1.10 (B), 3A1.3 (C), R18.2
READY: 1D2.10, 3J1.10
RECOVERY_MODE: 3J1.6, 5D1.36 (PA2)
RMODE_IN: 3J1.5
SEEK_COMPLETE: 1C1.12, 6D1.9 (Q)
STEP: 4B1.9
WCURR0: 5D1.6 (PD3)
WCURR1: 5D1.5 (PD4)
WRITE_FAULT: 1D2.12
~DC_UNSAFE: 4A1.10 (B)
~INDEX: 1D2.6
~OUT_EN: 1C1.13, 1D2.2, 1D2.4, 1D2.9, 1D2.13, 4B1.10
~READY: 1D2.8
~SEEK_COMPLETE: 1C1.11
~START/RUN: 1H1.12
~TRACK000: 1D2.3
~WRITE_FAULT: 1D2.11

Notes on the sheet:
384ns
This work is licensed under a Creative Commons Attribution-ShareAlike 4.0 International License. See https://creativecommons.org/licenses/by-sa/4.0/.
RD_DATA DC: PA7 = low RD_DATA f < 1.4MHz: PA7 = pulsing RD_DATA 1.4MHz < f < 2.6MHz: PA7 = high RD_DATA f > 2.6MHz: PA7 = low
_↑‾
ASSY 20301
Reverse Engineered by Tube Time
1.2ms
WHITE BODGE WIRE
720ns
60ms
ST-225 CONTROL
