schlae/HardDriveInfo/st225n/20427/Analog.kicad_sch

## KiCad design st225n/20427/Analog.kicad_sch (2024-08-16)

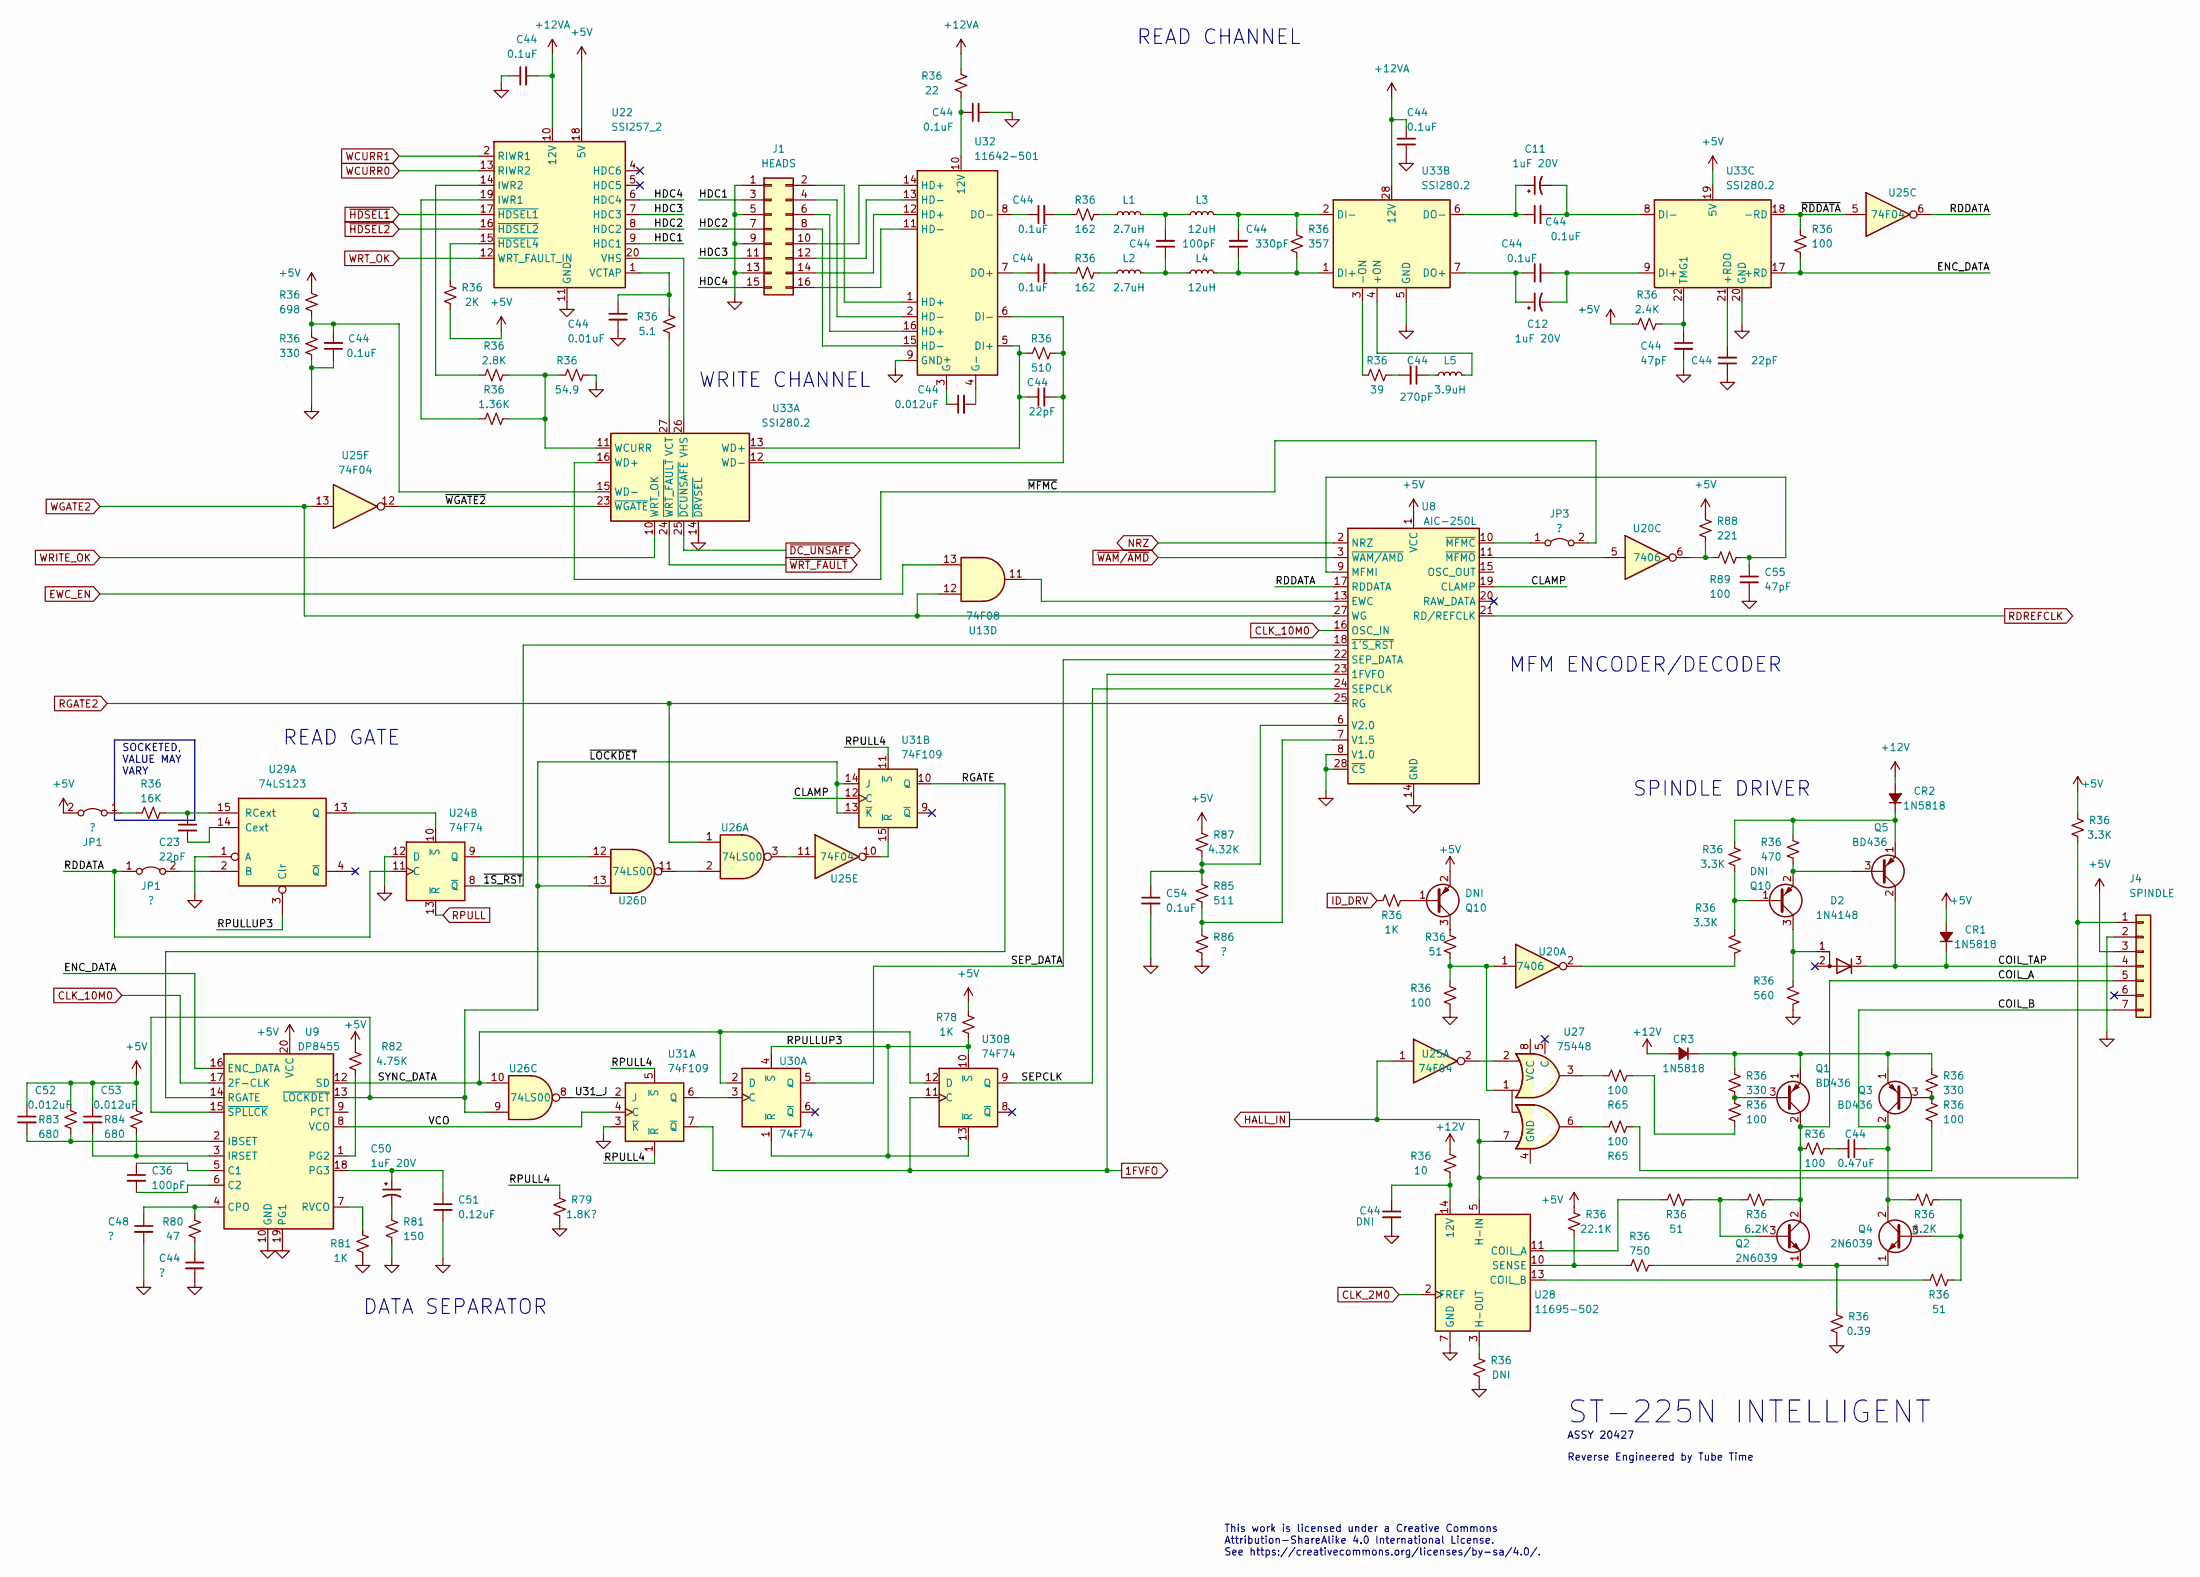
[picture p29: schematic Analog.kicad_sch]

Parts:
C11, C12, C50: 1uF 20V; CP_EIA-3528-21_Kemet-B_Pad1.50x2.35mm_HandSolder
C23: 22pF; C_0805_2012Metric
C36: 100pF; C_0805_2012Metric
C44, C48: ?; C_1206_3216Metric_Pad1.33x1.80mm_HandSolder
C51: 0.12uF; C_1206_3216Metric_Pad1.33x1.80mm_HandSolder
C52, C53: 0.012uF; C_0805_2012Metric_Pad1.18x1.45mm_HandSolder
C54: 0.1uF; C_1206_3216Metric_Pad1.33x1.80mm_HandSolder
C55: 47pF; C_0805_2012Metric_Pad1.18x1.45mm_HandSolder
CR1, CR2, CR3: 1N5818; D_DO-35_SOD27_P10.16mm_Horizontal
D2: 1N4148; SOT-23
J1: HEADS; PinHeader_2x08_P2.54mm_Vertical
J4: SPINDLE; PinHeader_1x07_P2.54mm_Vertical
JP1, JP3: ?; JMP2
L1, L2: 2.7uH; L_1206_3216Metric_Pad1.22x1.90mm_HandSolder
L3, L4: 12uH; L_1206_3216Metric_Pad1.22x1.90mm_HandSolder
L5: 3.9uH; L_1206_3216Metric_Pad1.22x1.90mm_HandSolder
Q1, Q3, Q5: BD436; TO-126-3_Horizontal_TabDown
Q2, Q4: 2N6039; TO-126-3_Horizontal_TabDown
Q10: DNI; SOT-23
R36: 6.2K; R_1206_3216Metric_Pad1.30x1.75mm_HandSolder
R65: 100; R_1210_3225Metric
R78, R81: 1K; R_1206_3216Metric_Pad1.30x1.75mm_HandSolder
R79: 1.8K?; R_1206_3216Metric_Pad1.30x1.75mm_HandSolder
R80: 47; R_1206_3216Metric_Pad1.30x1.75mm_HandSolder
R82: 4.75K; R_1206_3216Metric_Pad1.30x1.75mm_HandSolder
R83, R84: 680; R_1206_3216Metric_Pad1.30x1.75mm_HandSolder
R85: 511; R_1206_3216Metric_Pad1.30x1.75mm_HandSolder
R86: ?; R_1206_3216Metric_Pad1.30x1.75mm_HandSolder
R87: 4.32K; R_1206_3216Metric_Pad1.30x1.75mm_HandSolder
R88: 221; R_1206_3216Metric_Pad1.30x1.75mm_HandSolder
R89: 100; R_1206_3216Metric_Pad1.30x1.75mm_HandSolder
U8: AIC-250L; PLCC-28
U9: DP8455; PLCC-20
U13: 74F08; SOP127P620X175-14_SHRINK
U20: 7406; SOP127P620X175-14_SHRINK
U22: SSI257_2; SOP127P1065X265-20_SHRINK
U24, U30: 74F74; SOP127P620X175-14_SHRINK
U25: 74F04; SOP127P620X175-14_SHRINK
U26: 74LS00; SOP127P620X175-14_SHRINK
U27: 75448; SOP127P620X175-8_SHRINK
U28: 11695-502; SOP127P1065X265-16_SHRINK
U29: 74LS123; SOP127P620X175-16_SHRINK
U31: 74F109; SOP127P620X175-16_SHRINK
U32: 11642-501; SOP127P620X175-16_SHRINK
U33: SSI280.2; PLCC-28

Connections:
1FVFO: U8.23 (1FVFO), U30.11 (C), U31.7 (~Q)
+5V: C52.1, C53.1, CR1.2 (A), J4.3, JP1.2 (B), Q10.2 (E), R36.1, R36.2, R78.2, R82.2, R83.2, R84.2, R87.2, R88.2, U8.1 (VCC), U9.20 (VCC), U22.18 (5V), U33.19 (5V)
+12V: CR2.2 (A), CR3.2 (A), R36.1
+12VA: C44.1, C44.2, R36.2, U22.10 (12V), U33.28 (12V)
CLAMP: U8.19 (CLAMP), U31.12 (C)
CLK_2M0: U28.2 (FREF)
CLK_10M0: U8.16 (OSC_IN), U9.17 (2F-CLK)
COIL_A: J4.5, Q1.2 (C), Q2.2 (C), R36.2
COIL_B: C44.1, J4.7, Q3.2 (C), Q4.2 (C), R36.1
COIL_TAP: CR1.1 (K), D2.3 (K), J4.4, Q5.2 (C)
ENC_DATA: R36.2, U9.16 (ENC_DATA), U33.17 (+RD)
EWC_EN: U13.13
GND: C44.1, C44.2, C48.2, C51.2, C54.2, C55.2, J1.1, J1.5, J1.9, J1.13, J4.2, R36.1, R36.2, R79.1, R81.1, R86.1, U8.8 (V1.0), U8.14 (GND), U8.28 (~CS), U9.10 (GND), U9.19 (PG1), U22.11 (GND), U24.12 (D), U28.7 (GND), U29.1 (A), U31.3 (~K), U32.9 (GND), U33.5 (GND), U33.14 (~DRVSEL), U33.20 (GND)
HALL_IN: J4.1, R36.2, U25.1, U27.7, U28.5 (H-IN)
HDC1: J1.3, U22.9 (HDC1)
HDC2: J1.7, U22.8 (HDC2)
HDC3: J1.11, U22.7 (HDC3)
HDC4: J1.15, U22.6 (HDC4)
ID_DRV: R36.1
NRZ: U8.2 (NRZ)
unnamed: C11.1, C44.1, U33.6 (DO-)
unnamed: C11.2, C44.2, U33.8 (DI-)
unnamed: C12.1, C44.1, U33.7 (DO+)
unnamed: C12.2, C44.2, U33.9 (DI+)
unnamed: C23.1, R36.2, U29.15 (RCext)
unnamed: C23.2, U29.14 (Cext)
unnamed: C36.1, U9.5 (C1)
unnamed: C36.2, U9.6 (C2)
unnamed: C44.1, L2.2, L4.1, L4.2, L5.1, R36.1, R36.2, R80.1, U22.1 (VCTAP), U28.14 (12V), U32.3 (G+), U32.5 (DI+), U32.7 (DO+), U32.8 (DO-), U32.10 (12V), U33.1 (DI+), U33.13 (WD-), U33.22 (TMG1)
unnamed: C44.2, L1.2, L3.1, L3.2, R36.1, R36.2, U32.4 (G-), U32.6 (DI-), U33.2 (DI-), U33.12 (WD+), U33.15 (WD-), U33.21 (+RDO)
unnamed: C48.1, R80.2, U9.4 (CPO)
unnamed: C50.1, C51.1, U9.18 (PG3)
unnamed: C50.2, R81.2
unnamed: C52.2, R83.1, U9.2 (IBSET)
unnamed: C53.2, R84.1, U9.3 (IRSET)
unnamed: C54.1, R85.2, R87.1, U8.6 (V2.0)
unnamed: C55.1, R89.1, U8.9 (MFMI)
unnamed: CR2.1 (K), Q5.1 (E), R36.2
unnamed: CR3.1 (K), Q1.1 (E), Q3.1 (E), R36.1
unnamed: D2.1 (A), Q10.3 (C), R36.1
unnamed: J1.2, U32.1 (HD+)
unnamed: J1.4, U32.2 (HD-)
unnamed: J1.6, U32.16 (HD+)
unnamed: J1.8, U32.15 (HD-)
unnamed: J1.10, U32.14 (HD+)
unnamed: J1.12, U32.13 (HD-)
unnamed: J1.14, U32.12 (HD+)
unnamed: J1.16, U32.11 (HD-)
unnamed: JP1.1 (A), R36.1
unnamed: JP1.2 (B), U29.2 (B)
unnamed: JP3.1 (A), U8.10 (~MFMC)
unnamed: L1.1, R36.1
unnamed: L2.1, R36.1
unnamed: L5.2, U33.4 (+ON)
unnamed: Q1.3 (B), R36.1, R36.2
unnamed: Q2.1 (E), Q4.1 (E), R36.1
unnamed: Q2.3 (B), R36.1, R36.2
unnamed: Q3.3 (B), R36.1, R36.2
unnamed: Q4.3 (B), R36.2
unnamed: Q10.1 (B), R36.1, R36.2
unnamed: Q5.3 (B), Q10.2 (E), R36.1
unnamed: Q10.3 (C), R36.1
unnamed: R36.1, R36.2, U20.1, U22.15 (~HDSEL4), U27.1, U28.3 (H-OUT), U28.11 (COIL_A), U28.13 (COIL_B), U33.11 (WCURR), U33.27 (VCT)
unnamed: R36.2, R65.1, U20.2, U22.14 (IWR2), U22.19 (IWR1), U28.10 (SENSE), U33.3 (-ON)
unnamed: R65.2, U27.3, U27.6
unnamed: R81.2, U9.7 (RVCO)
unnamed: R82.1, U9.1 (PG2)
unnamed: R85.1, R86.2, U8.7 (V1.5)
unnamed: R88.1, R89.2, U20.6
unnamed: U8.13 (EWC), U13.11
unnamed: U8.11 (~MFMO), U20.5
unnamed: U22.20 (VHS), U33.26 (VHS)
unnamed: U24.9 (Q), U26.12
unnamed: U24.10 (~S), U29.13 (Q)
unnamed: U25.2, U27.2
unnamed: U25.10, U31.15 (~R)
unnamed: U25.11, U26.3
unnamed: U26.2, U26.11
unnamed: U30.3 (C), U31.6 (Q)
RDDATA: JP1.1 (A), U8.17 (RDDATA), U24.11 (C), U25.6
RDREFCLK: U8.21 (RD/REFCLK)
RGATE: U9.14 (RGATE), U31.10 (Q)
RGATE2: U8.25 (RG), U26.1
RPULL: U24.13 (~R)
RPULL4: R79.2, U31.1 (~R), U31.5 (~S), U31.11 (~S)
RPULLUP3: R78.1, U29.3 (Clr), U30.1 (~R), U30.4 (~S), U30.10 (~S), U30.13 (~R)
SEPCLK: U8.24 (SEPCLK), U30.9 (Q)
SEP_DATA: U8.22 (SEP_DATA), U30.5 (Q)
SYNC_DATA: U9.12 (SD), U26.10, U30.2 (D), U30.12 (D)
U31_J: U26.8, U31.2 (J)
VCO: U9.8 (VCO), U31.4 (C)
WCURR0: U22.13 (RIWR2)
WCURR1: U22.2 (RIWR1)
WGATE2: U8.27 (WG), U13.12, U25.13
WRITE_OK: U33.10 (WRT_OK)
WRT_OK: U22.12 (WRT_FAULT_IN)
~1S_RST: U8.18 (~1'S_RST), U24.8 (~Q)
~DC_UNSAFE: U33.25 (~DCUNSAFE)
~HDSEL1: U22.17 (~HDSEL1)
~HDSEL2: U22.16 (~HDSEL2)
~LOCKDET: U9.13 (~LOCKDET), U9.15 (~SPLLCK), U26.9, U26.13, U31.13 (~K), U31.14 (J)
~MFMC: JP3.2 (B), U33.16 (WD)
~RDDATA: R36.1, U25.5, U33.18 (-RD)
~WAM/~AMD: U8.3 (~WAM/AMD)
~WGATE2: U25.12, U33.23 (~WGATE)
~WRT_FAULT: U33.24 (~WRT_FAULT)

Notes on the sheet:
ST-225N INTELLIGENT
SPINDLE DRIVER
WRITE CHANNEL
READ GATE
Reverse Engineered by Tube Time
ASSY 20427
SOCKETED, VALUE MAY VARY
DATA SEPARATOR
This work is licensed under a Creative Commons Attribution-ShareAlike 4.0 International License. See https://creativecommons.org/licenses/by-sa/4.0/.
MFM ENCODER/DECODER
READ CHANNEL
