schlae/HardDriveInfo/st225n/20427/DigitalStepper.kicad_sch

## KiCad design st225n/20427/DigitalStepper.kicad_sch (2024-08-16)

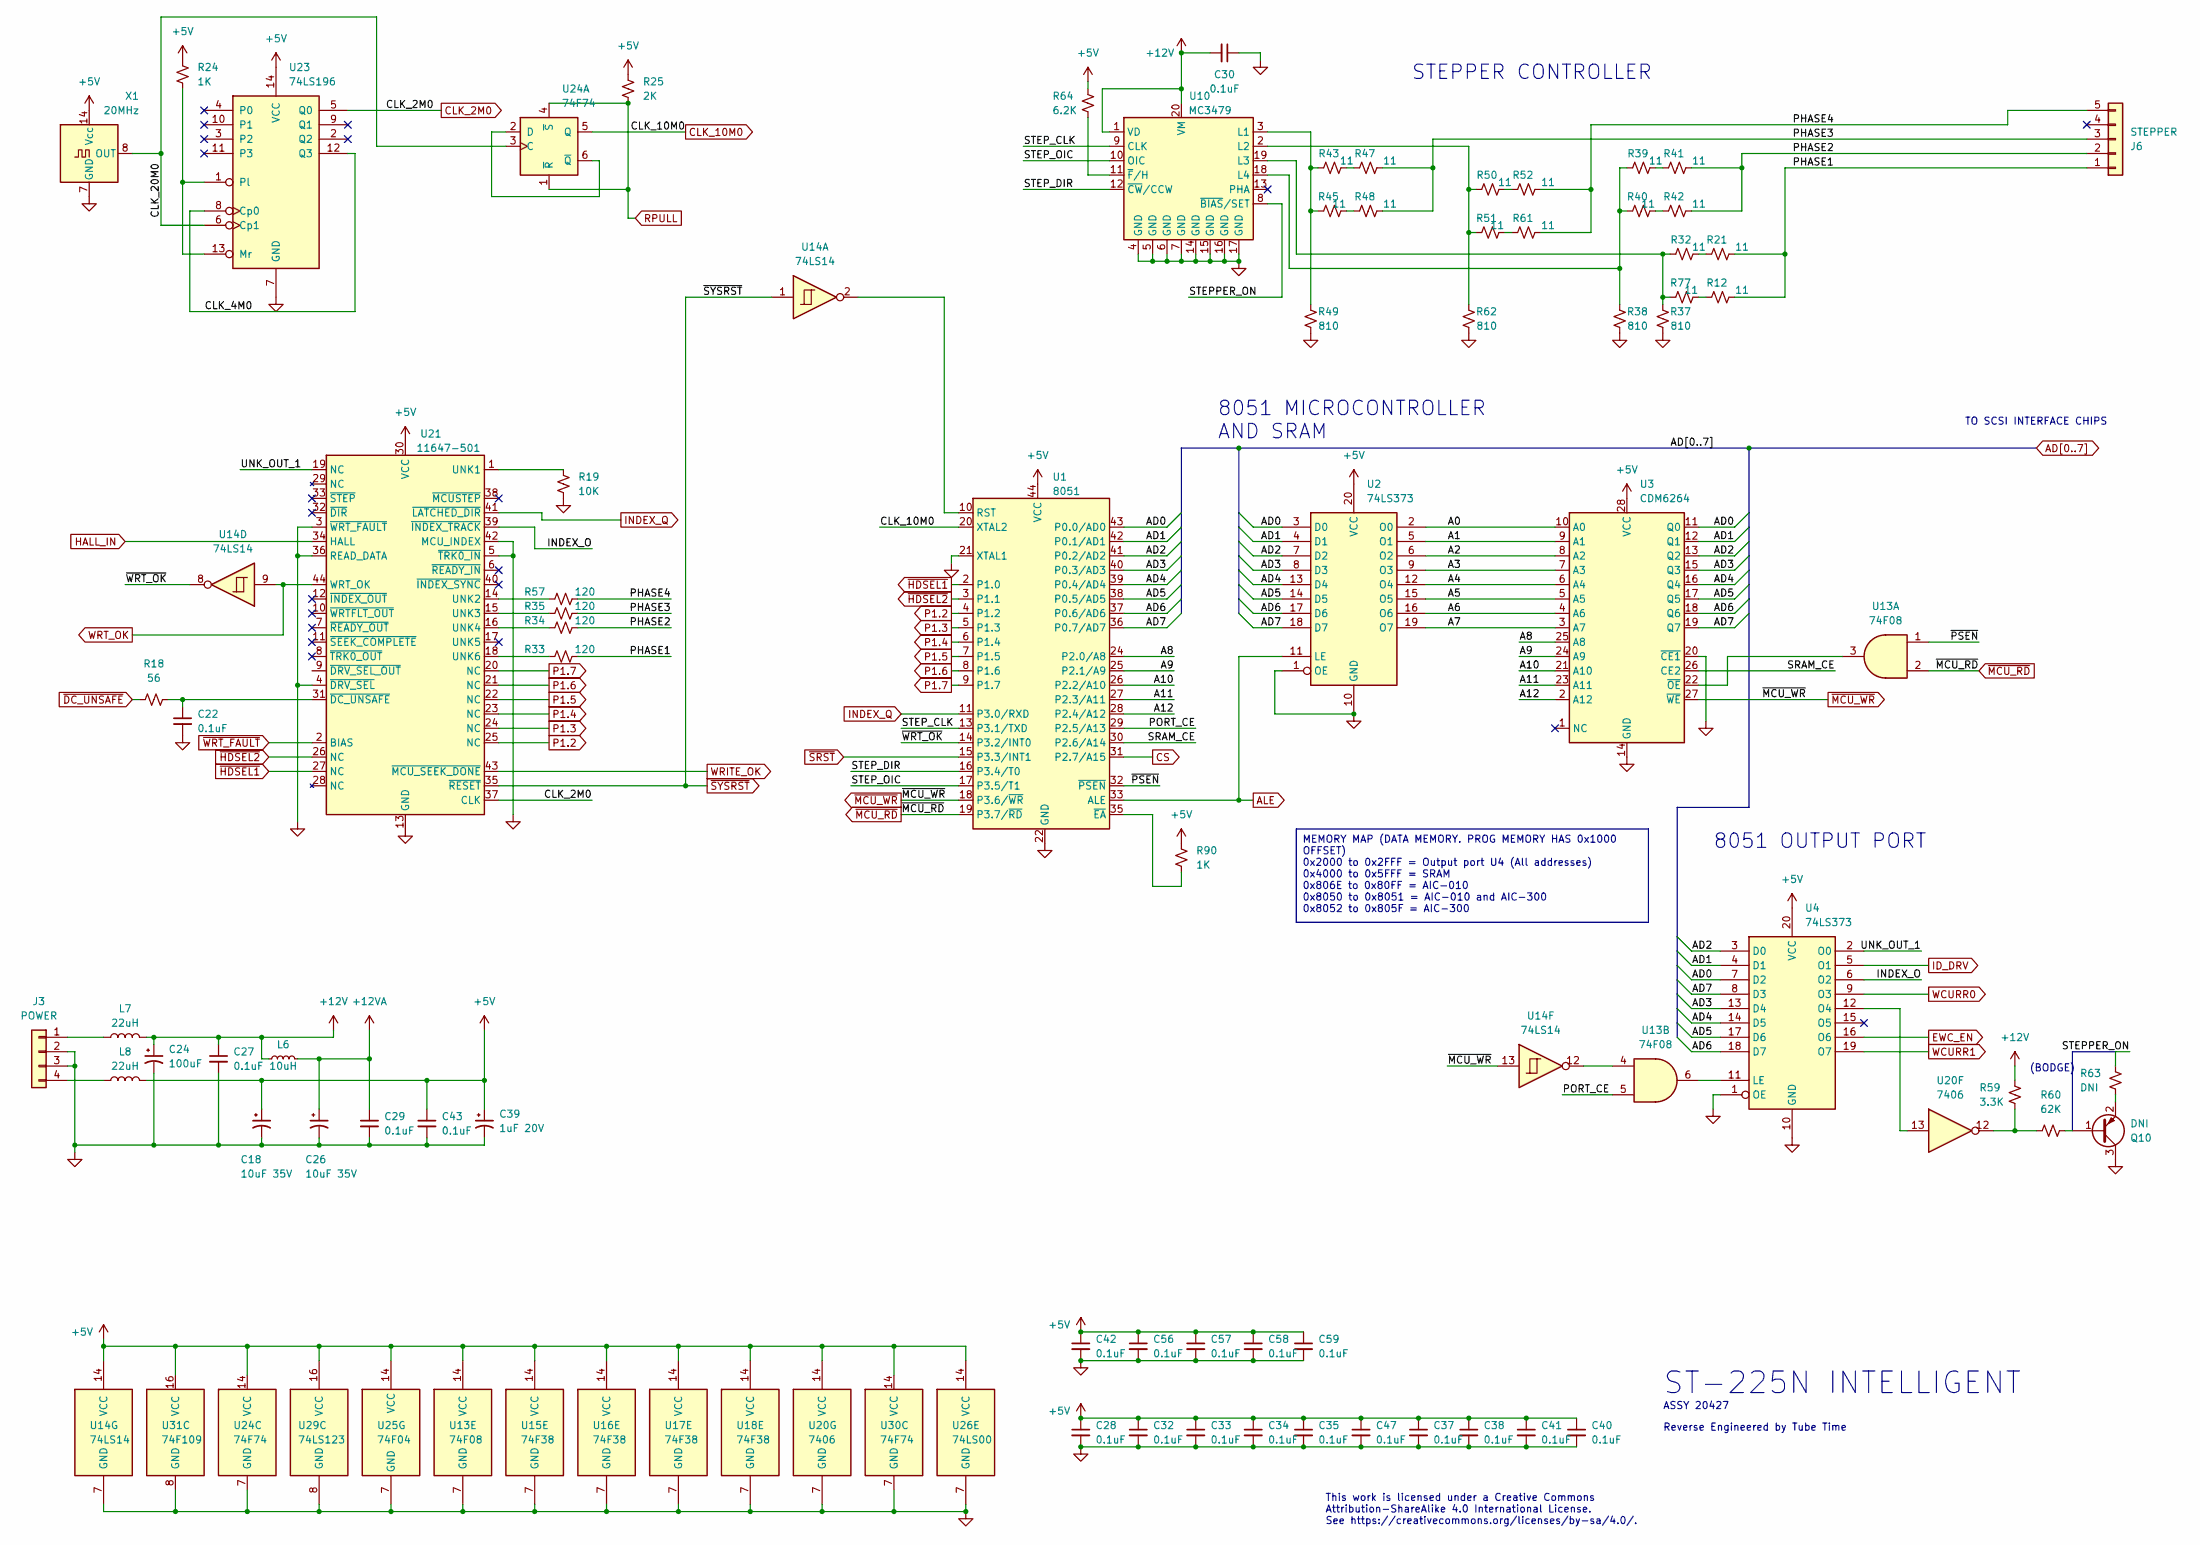
[picture p30: schematic DigitalStepper.kicad_sch]

Parts:
C18: 10uF 35V; CP_EIA-7132-20_AVX-U
C22, C27, C28, C29, C30, C32, C33, C34, C35, C37, C38, C40, C41, C42, C43, C47, C56, C57, C58, C59: 0.1uF; C_1206_3216Metric_Pad1.33x1.80mm_HandSolder
C24: 100uF; C_Axial_L12.0mm_D6.5mm_P20.00mm_Horizontal
C26: 10uF 35V; CP_EIA-7132-20_AVX-U_Pad2.72x3.50mm_HandSolder
C39: 1uF 20V; CP_EIA-6032-15_Kemet-U
J3: POWER; Samtec_HPM-04-01-x-S_Straight_1x04_Pitch5.08mm
J6: STEPPER; PinHeader_1x05_P2.54mm_Vertical
L6: 10uH; L_1206_3216Metric_Pad1.22x1.90mm_HandSolder
L7, L8: 22uH; L_Axial_L13.0mm_D4.5mm_P15.24mm_Horizontal_Fastron_HCCC
Q10: DNI; SOT-23
R12, R21, R32, R39, R40, R41, R42, R43, R45, R47, R48, R50, R51, R52, R61, R77: 11; R_1210_3225Metric_Pad1.30x2.65mm_HandSolder
R18: 56; R_1206_3216Metric_Pad1.30x1.75mm_HandSolder
R19: 10K; R_1206_3216Metric_Pad1.30x1.75mm_HandSolder
R24, R90: 1K; R_1206_3216Metric_Pad1.30x1.75mm_HandSolder
R25: 2K; R_1206_3216Metric_Pad1.30x1.75mm_HandSolder
R33, R34, R35, R57: 120; R_1206_3216Metric_Pad1.30x1.75mm_HandSolder
R37, R38, R49, R62: 810; R_1210_3225Metric_Pad1.30x2.65mm_HandSolder
R59: 3.3K; R_1206_3216Metric_Pad1.30x1.75mm_HandSolder
R60: 62K; R_1206_3216Metric_Pad1.30x1.75mm_HandSolder
R63: DNI; R_1206_3216Metric_Pad1.30x1.75mm_HandSolder
R64: 6.2K; R_1206_3216Metric_Pad1.30x1.75mm_HandSolder
U1: 8051; PLCC-44
U2, U4: 74LS373; SOP127P1065X265-20_SHRINK
U3: CDM6264; SOP127P1270X305-28_SHRINK
U10: MC3479; PLCC-20
U13: 74F08; SOP127P620X175-14_SHRINK
U14: 74LS14; SOP127P620X175-14_SHRINK
U15, U16, U17, U18: 74F38; SOP127P620X175-14_SHRINK
U20: 7406; SOP127P620X175-14_SHRINK
U21: 11647-501; PLCC-44
U23: 74LS196; SOP127P620X175-14_SHRINK
U24, U30: 74F74; SOP127P620X175-14_SHRINK
U25: 74F04; SOP127P620X175-14_SHRINK
U26: 74LS00; SOP127P620X175-14_SHRINK
U29: 74LS123; SOP127P620X175-16_SHRINK
U31: 74F109; SOP127P620X175-16_SHRINK
X1: 20MHz; Oscillator_DIP-14

Connections:
+5V: C18.1, C28.1, C32.1, C33.1, C34.1, C35.1, C37.1, C38.1, C39.1, C40.1, C41.1, C42.1, C43.1, C47.1, C56.1, C57.1, C58.1, C59.1, L8.2, R24.2, R25.2, R64.1, R90.2, U1.44 (VCC), U2.20 (VCC), U3.28 (VCC), U4.20 (VCC), U13.14 (VCC), U14.14 (VCC), U15.14 (VCC), U16.14 (VCC), U17.14 (VCC), U18.14 (VCC), U20.14 (VCC), U21.30 (VCC), U23.14 (VCC), U24.14 (VCC), U25.14 (VCC), U26.14 (VCC), U29.16 (VCC), U30.14 (VCC), U31.16 (VCC), X1.14 (Vcc)
+12V: C24.1, C27.1, C30.2, L6.1, L7.2, R59.1, U10.1 (VD), U10.20 (VM)
+12VA: C26.1, C29.1, L6.2
A0: U2.2 (O0), U3.10 (A0)
A1: U2.5 (O1), U3.9 (A1)
A2: U2.6 (O2), U3.8 (A2)
A3: U2.9 (O3), U3.7 (A3)
A4: U2.12 (O4), U3.6 (A4)
A5: U2.15 (O5), U3.5 (A5)
A6: U2.16 (O6), U3.4 (A6)
A7: U2.19 (O7), U3.3 (A7)
A8: U1.24 (P2.0/A8), U3.25 (A8)
A9: U1.25 (P2.1/A9), U3.24 (A9)
A10: U1.26 (P2.2/A10), U3.21 (A10)
A11: U1.27 (P2.3/A11), U3.23 (A11)
A12: U1.28 (P2.4/A12), U3.2 (A12)
AD0: U1.43 (P0.0/AD0), U2.3 (D0), U3.11 (Q0), U4.7 (D2)
AD1: U1.42 (P0.1/AD1), U2.4 (D1), U3.12 (Q1), U4.4 (D1)
AD2: U1.41 (P0.2/AD2), U2.7 (D2), U3.13 (Q2), U4.3 (D0)
AD3: U1.40 (P0.3/AD3), U2.8 (D3), U3.15 (Q3), U4.13 (D4)
AD4: U1.39 (P0.4/AD4), U2.13 (D4), U3.16 (Q4), U4.14 (D5)
AD5: U1.38 (P0.5/AD5), U2.14 (D5), U3.17 (Q5), U4.17 (D6)
AD6: U1.37 (P0.6/AD6), U2.17 (D6), U3.18 (Q6), U4.18 (D7)
AD7: U1.36 (P0.7/AD7), U2.18 (D7), U3.19 (Q7), U4.8 (D3)
ALE: U1.33 (ALE), U2.11 (LE)
CLK_2M0: U21.37 (CLK), U23.5 (Q0)
CLK_4M0: U23.8 (Cp0), U23.12 (Q3)
CLK_10M0: U1.20 (XTAL2), U24.5 (Q)
CLK_20M0: U23.6 (Cp1), U24.3 (C), X1.8 (OUT)
CS: U1.31 (P2.7/A15)
EWC_EN: U4.16 (O6)
GND: C18.2, C22.2, C24.2, C26.2, C27.2, C28.2, C29.2, C30.1, C32.2, C33.2, C34.2, C35.2, C37.2, C38.2, C39.2, C40.2, C41.2, C42.2, C43.2, C47.2, C56.2, C57.2, C58.2, C59.2, J3.2, J3.3, Q10.3 (C), R19.1, R37.1, R38.1, R49.1, R62.1, U1.21 (XTAL1), U1.22 (GND), U2.1 (OE), U2.10 (GND), U3.14 (GND), U3.20 (~CE1), U4.1 (OE), U4.10 (GND), U10.4 (GND), U10.5 (GND), U10.6 (GND), U10.7 (GND), U10.14 (GND), U10.15 (GND), U10.16 (GND), U10.17 (GND), U13.7 (GND), U14.7 (GND), U15.7 (GND), U16.7 (GND), U17.7 (GND), U18.7 (GND), U20.7 (GND), U21.3 (~WRT_FAULT), U21.4 (~DRV_SEL), U21.5 (~TRK0_IN), U21.13 (GND), U21.36 (READ_DATA), U21.42 (MCU_INDEX), U23.7 (GND), U24.7 (GND), U25.7 (GND), U26.7 (GND), U29.8 (GND), U30.7 (GND), U31.8 (GND), X1.7 (GND)
HALL_IN: U21.34 (HALL)
ID_DRV: U4.5 (O1)
INDEX_O: U4.6 (O2), U21.39 (~INDEX_TRACK)
INDEX_Q: U1.11 (P3.0/RXD), U21.41 (~LATCHED_DIR)
unnamed: C22.1, R18.2, U21.31 (~DC_UNSAFE)
unnamed: J3.1, L7.1
unnamed: J3.4, L8.1
unnamed: Q10.1 (B), R60.1
unnamed: Q10.2 (E), R63.2
unnamed: R12.2, R77.2
unnamed: R19.2, U21.1 (UNK1)
unnamed: R21.2, R32.1
unnamed: R24.1, U23.1 (Pl), U23.13 (Mr)
unnamed: R32.2, R37.2, R77.1, U10.19 (L3)
unnamed: R33.1, U21.18 (UNK6)
unnamed: R34.1, U21.16 (UNK4)
unnamed: R35.1, U21.15 (UNK3)
unnamed: R38.2, R39.2, R40.1, U10.18 (L4)
unnamed: R39.1, R41.2
unnamed: R40.2, R42.2
unnamed: R43.1, R47.2
unnamed: R43.2, R45.1, R49.2, U10.3 (L1)
unnamed: R45.2, R48.2
unnamed: R50.1, R52.2
unnamed: R50.2, R51.1, R62.2, U10.2 (L2)
unnamed: R51.2, R61.2
unnamed: R57.1, U21.14 (UNK2)
unnamed: R59.2, R60.2, U20.12
unnamed: R64.2, U10.11 (~F/H)
unnamed: R90.1, U1.35 (~EA)
unnamed: U1.10 (RST), U14.2
unnamed: U3.22 (~OE), U13.3
unnamed: U13.4, U14.12
unnamed: U4.11 (LE), U13.6
unnamed: U4.12 (O4), U20.13
unnamed: U24.2 (D), U24.6 (~Q)
P1.2: U1.4 (P1.2), U21.25 (NC)
P1.3: U1.5 (P1.3), U21.24 (NC)
P1.4: U1.6 (P1.4), U21.23 (NC)
P1.5: U1.7 (P1.5), U21.22 (NC)
P1.6: U1.8 (P1.6), U21.21 (NC)
P1.7: U1.9 (P1.7), U21.20 (NC)
PHASE1: J6.1, R12.1, R21.1, R33.2
PHASE2: J6.2, R34.2, R41.1, R42.1
PHASE3: J6.3, R35.2, R47.1, R48.1
PHASE4: J6.5, R52.1, R57.2, R61.1
PORT_CE: U1.29 (P2.5/A13), U13.5
RPULL: R25.1, U24.1 (~R), U24.4 (~S)
SRAM_CE: U1.30 (P2.6/A14), U3.26 (CE2)
STEPPER_ON: R63.1, U10.8 (~BIAS/SET)
STEP_CLK: U1.13 (P3.1/TXD), U10.9 (CLK)
STEP_DIR: U1.16 (P3.4/T0), U10.12 (~CW/CCW)
STEP_OIC: U1.17 (P3.5/T1), U10.10 (OIC)
UNK_OUT_1: U4.2 (O0), U21.19 (NC)
WCURR0: U4.9 (O3)
WCURR1: U4.19 (O7)
WRITE_OK: U21.43 (~MCU_SEEK_DONE)
WRT_OK: U14.9, U21.44 (WRT_OK)
~DC_UNSAFE: R18.1
~HDSEL1: U1.2 (P1.0), U21.27 (NC)
~HDSEL2: U1.3 (P1.1), U21.26 (NC)
~MCU_RD: U1.19 (P3.7/~RD), U13.2
~MCU_WR: U1.18 (P3.6/~WR), U3.27 (~WE), U14.13
~PSEN: U1.32 (~PSEN), U13.1
~SRST: U1.15 (P3.3/INT1)
~SYSRST: U14.1, U21.35 (~RESET)
~WRT_FAULT: U21.2 (BIAS)
~WRT_OK: U1.14 (P3.2/INT0), U14.8

Notes on the sheet:
MEMORY MAP (DATA MEMORY. PROG MEMORY HAS 0x1000 OFFSET) 0x2000 to 0x2FFF = Output port U4 (All addresses) 0x4000 to 0x5FFF = SRAM 0x806E to 0x80FF = AIC-010 0x8050 to 0x8051 = AIC-010 and AIC-300 0x8052 to 0x805F = AIC-300
This work is licensed under a Creative Commons Attribution-ShareAlike 4.0 International License. See https://creativecommons.org/licenses/by-sa/4.0/.
ASSY 20427
Reverse Engineered by Tube Time
8051 OUTPUT PORT
(BODGE)
TO SCSI INTERFACE CHIPS
8051 MICROCONTROLLER AND SRAM
ST-225N INTELLIGENT
STEPPER CONTROLLER
