schlae/HardDriveInfo/st225n/20427/SCSI.kicad_sch

## KiCad design st225n/20427/SCSI.kicad_sch (2024-08-16)

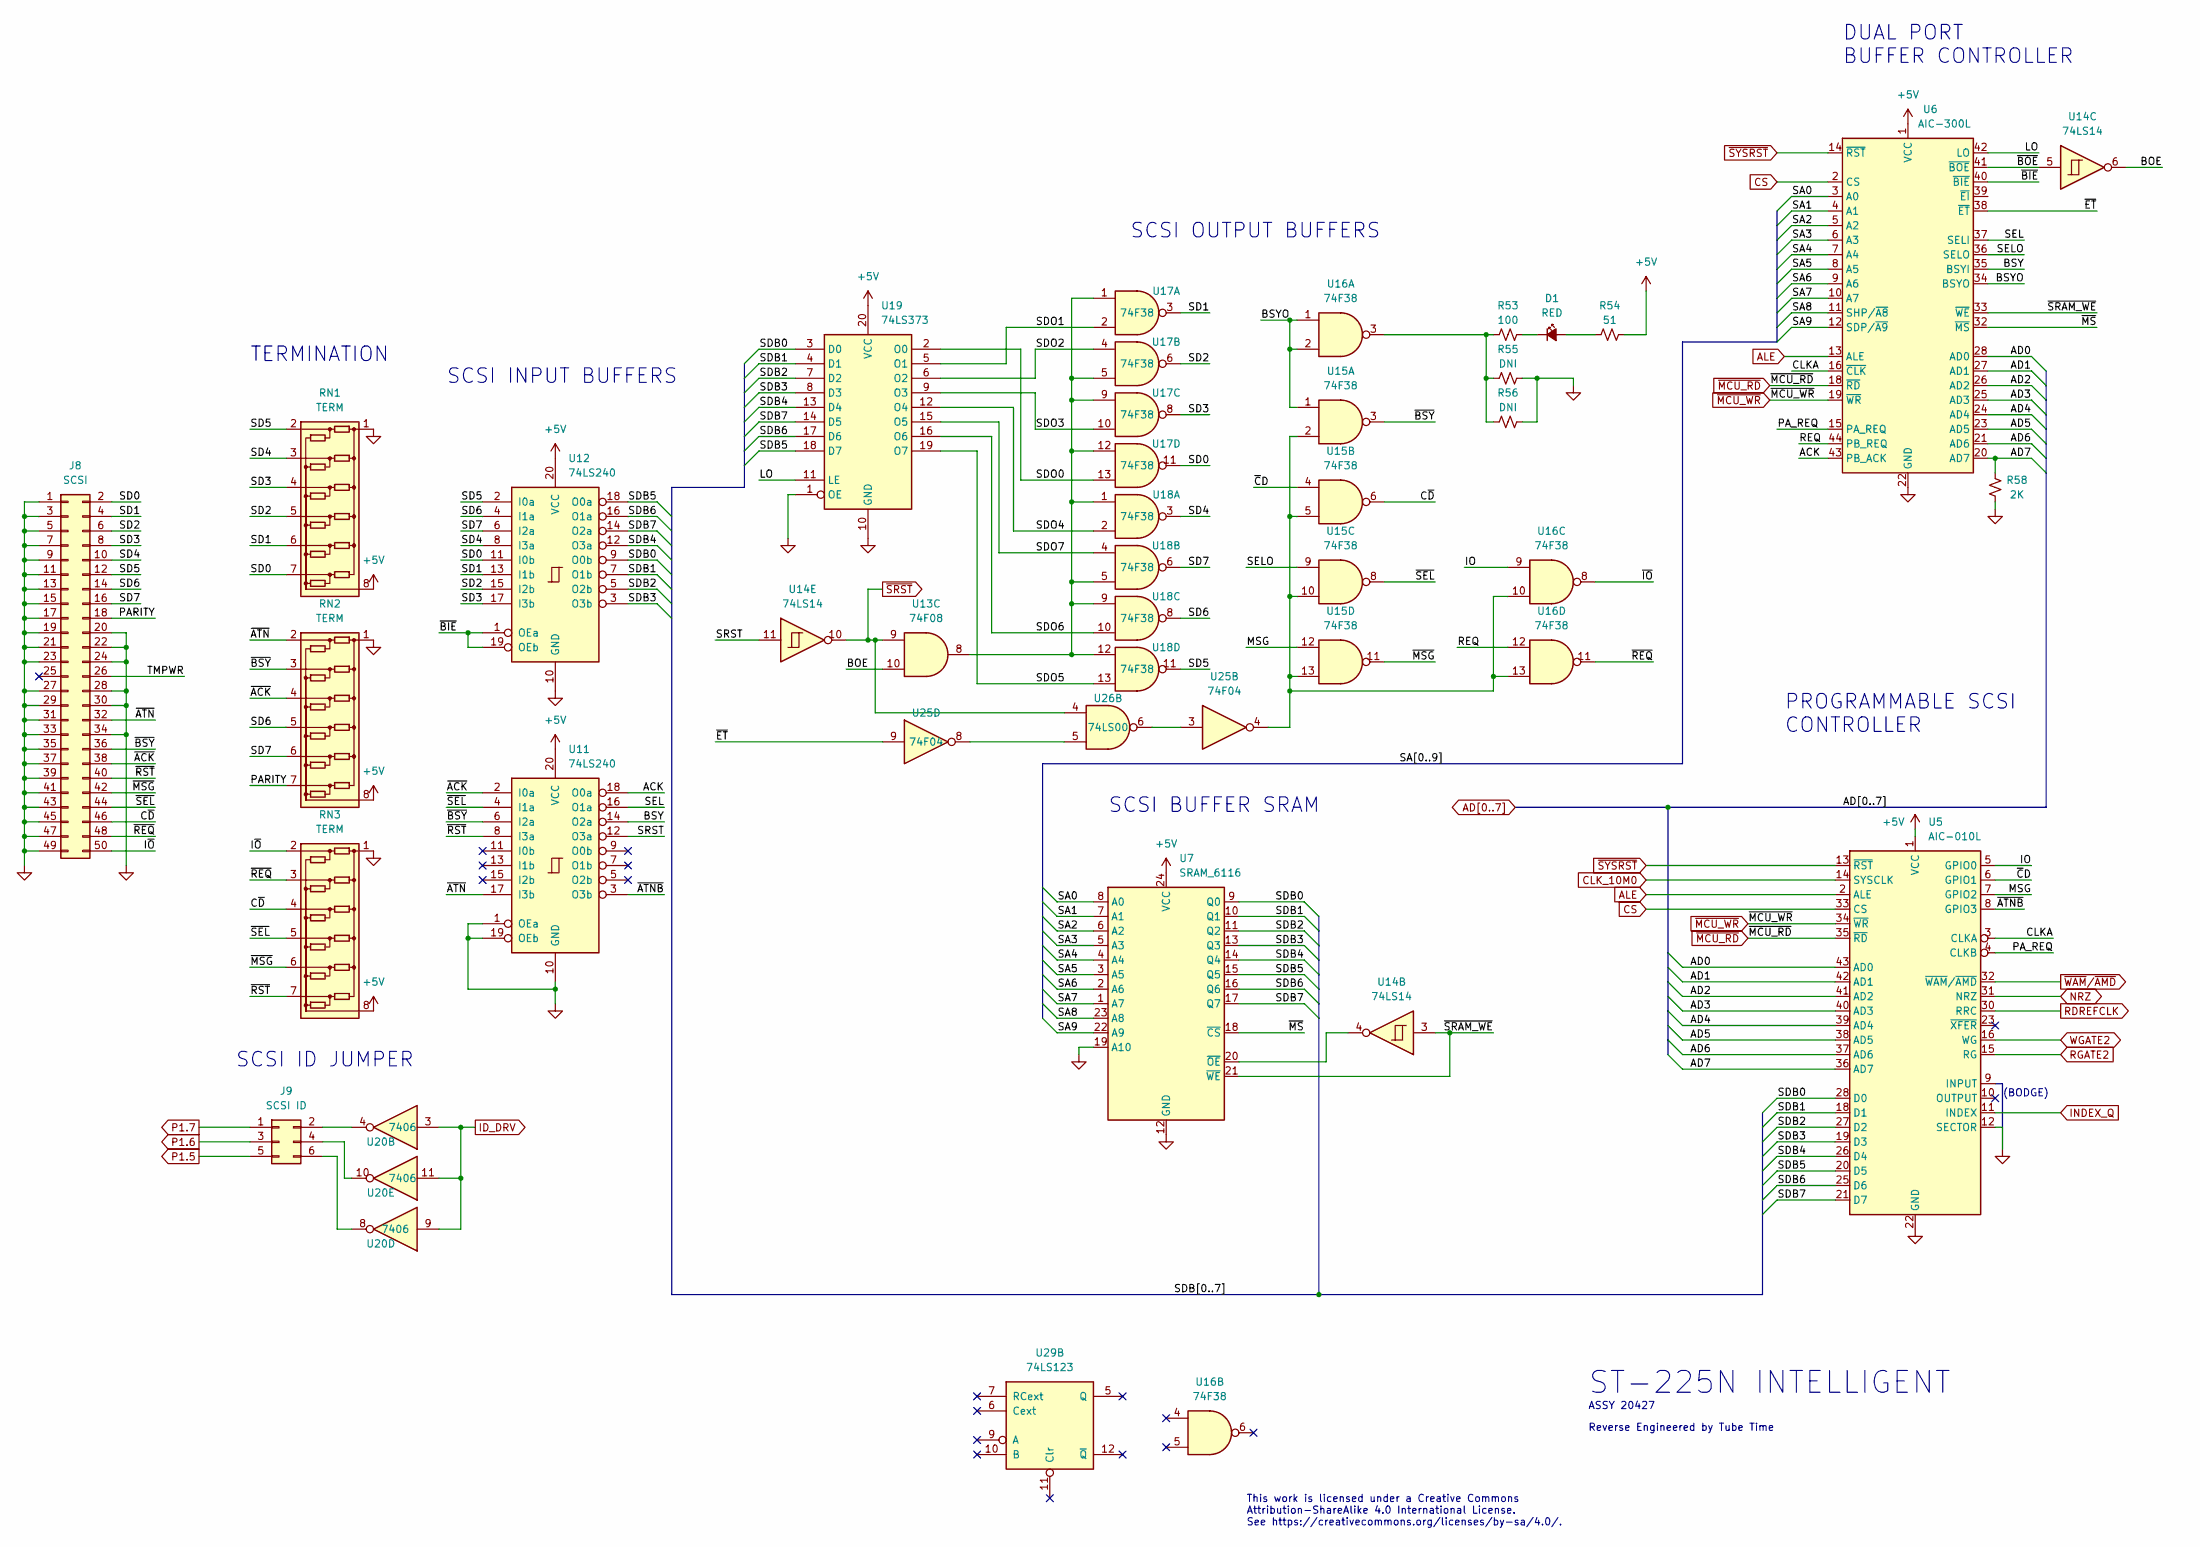
[picture p31: schematic SCSI.kicad_sch]

Parts:
D1: RED; PinHeader_1x02_P2.54mm_Vertical
J8: SCSI; PinHeader_2x25_P2.54mm_Horizontal
J9: SCSI ID; PinHeader_2x03_P2.54mm_Vertical
R53: 100; R_1206_3216Metric_Pad1.30x1.75mm_HandSolder
R54: 51; R_1206_3216Metric
R55, R56: DNI; R_1206_3216Metric_Pad1.30x1.75mm_HandSolder
R58: 2K; R_1206_3216Metric_Pad1.30x1.75mm_HandSolder
RN1, RN2, RN3: TERM; R_Array_SIP8
U5: AIC-010L; PLCC-44
U6: AIC-300L; PLCC-44
U7: SRAM_6116; SOP127P1250X255-24
U11, U12: 74LS240; SOP127P1065X265-20_SHRINK
U13: 74F08; SOP127P620X175-14_SHRINK
U14: 74LS14; SOP127P620X175-14_SHRINK
U15, U16, U17, U18: 74F38; SOP127P620X175-14_SHRINK
U19: 74LS373; SOP127P1065X265-20_SHRINK
U20: 7406; SOP127P620X175-14_SHRINK
U25: 74F04; SOP127P620X175-14_SHRINK
U26: 74LS00; SOP127P620X175-14_SHRINK
U29: 74LS123; SOP127P620X175-16_SHRINK

Connections:
+5V: R54.2, RN1.8 (COM2), RN2.8 (COM2), RN3.8 (COM2), U5.1 (VCC), U6.1 (VCC), U7.24 (VCC), U11.20 (VCC), U12.20 (VCC), U19.20 (VCC)
ACK: U6.43 (PB_ACK), U11.18 (O0a)
AD0: U5.43 (AD0), U6.28 (AD0)
AD1: U5.42 (AD1), U6.27 (AD1)
AD2: U5.41 (AD2), U6.26 (AD2)
AD3: U5.40 (AD3), U6.25 (AD3)
AD4: U5.39 (AD4), U6.24 (AD4)
AD5: U5.38 (AD5), U6.23 (AD5)
AD6: U5.37 (AD6), U6.21 (AD6)
AD7: R58.2, U5.36 (AD7), U6.20 (AD7)
ALE: U5.2 (ALE), U6.13 (ALE)
BOE: U13.10, U14.6
BSY: U6.35 (BSYI), U11.14 (O2a)
BSYO: U6.34 (BSYO), U15.1, U16.1, U16.2
CLKA: U5.3 (CLKA), U6.16 (~CLK)
CLK_10M0: U5.14 (SYSCLK)
CS: U5.33 (CS), U6.2 (CS)
C~D: J8.46, RN3.4 (R3), U15.6
GND: J8.1, J8.3, J8.5, J8.7, J8.9, J8.11, J8.13, J8.15, J8.17, J8.19, J8.20, J8.21, J8.22, J8.23, J8.24, J8.27, J8.28, J8.29, J8.30, J8.31, J8.33, J8.34, J8.35, J8.37, J8.39, J8.41, J8.43, J8.45, J8.47, J8.49, R55.2, R56.2, R58.1, RN1.1 (COM1), RN2.1 (COM1), RN3.1 (COM1), U5.12 (SECTOR), U5.22 (GND), U6.22 (GND), U7.12 (GND), U7.19 (A10), U11.1 (OEa), U11.10 (GND), U11.19 (OEb), U12.10 (GND), U19.1 (OE), U19.10 (GND)
ID_DRV: U20.3, U20.9, U20.11
INDEX_Q: U5.11 (INDEX)
IO: U5.5 (GPIO0), U16.9
I~O: J8.50, RN3.2 (R1)
LO: U6.42 (LO), U19.11 (LE)
MSG: U5.7 (GPIO2), U15.12
NRZ: U5.31 (NRZ)
unnamed: D1.1 (K), R53.2
unnamed: D1.2 (A), R54.1
unnamed: J9.2, U20.4
unnamed: J9.4, U20.10
unnamed: J9.6, U20.8
unnamed: R53.1, R55.1, R56.1, U16.3
unnamed: U13.8, U17.1, U17.5, U17.9, U17.12, U18.1, U18.5, U18.9, U18.12
unnamed: U7.20 (~OE), U14.4
unnamed: U15.2, U15.5, U15.10, U15.13, U16.10, U16.13, U25.4
unnamed: U25.3, U26.6
unnamed: U25.8, U26.5
P1.5: J9.5
P1.6: J9.3
P1.7: J9.1
PARITY: J8.18, RN2.7 (R6)
PA_REQ: U5.4 (CLKB), U6.15 (PA_REQ)
RDREFCLK: U5.30 (RRC)
REQ: U6.44 (PB_REQ), U16.12
RGATE2: U5.15 (RG)
SA0: U6.3 (A0), U7.8 (A0)
SA1: U6.4 (A1), U7.7 (A1)
SA2: U6.5 (A2), U7.6 (A2)
SA3: U6.6 (A3), U7.5 (A3)
SA4: U6.7 (A4), U7.4 (A4)
SA5: U6.8 (A5), U7.3 (A5)
SA6: U6.9 (A6), U7.2 (A6)
SA7: U6.10 (A7), U7.1 (A7)
SA8: U6.11 (SHP/~A8), U7.23 (A8)
SA9: U6.12 (SDP/~A9), U7.22 (A9)
SD0: J8.2, RN1.7 (R6), U12.11 (I0b), U17.11
SD1: J8.4, RN1.6 (R5), U12.13 (I1b), U17.3
SD2: J8.6, RN1.5 (R4), U12.15 (I2b), U17.6
SD3: J8.8, RN1.4 (R3), U12.17 (I3b), U17.8
SD4: J8.10, RN1.3 (R2), U12.8 (I3a), U18.3
SD5: J8.12, RN1.2 (R1), U12.2 (I0a), U18.11
SD6: J8.14, RN2.5 (R4), U12.4 (I1a), U18.8
SD7: J8.16, RN2.6 (R5), U12.6 (I2a), U18.6
SDB0: U5.28 (D0), U7.9 (Q0), U12.9 (O0b), U19.3 (D0)
SDB1: U5.18 (D1), U7.10 (Q1), U12.7 (O1b), U19.4 (D1)
SDB2: U5.27 (D2), U7.11 (Q2), U12.5 (O2b), U19.7 (D2)
SDB3: U5.19 (D3), U7.13 (Q3), U12.3 (O3b), U19.8 (D3)
SDB4: U5.26 (D4), U7.14 (Q4), U12.12 (O3a), U19.13 (D4)
SDB5: U5.20 (D5), U7.15 (Q5), U12.18 (O0a), U19.18 (D7)
SDB6: U5.25 (D6), U7.16 (Q6), U12.16 (O1a), U19.17 (D6)
SDB7: U5.21 (D7), U7.17 (Q7), U12.14 (O2a), U19.14 (D5)
SDO0: U17.13, U19.2 (O0)
SDO1: U17.2, U19.5 (O1)
SDO2: U17.4, U19.6 (O2)
SDO3: U17.10, U19.9 (O3)
SDO4: U18.2, U19.12 (O4)
SDO5: U18.13, U19.19 (O7)
SDO6: U18.10, U19.16 (O6)
SDO7: U18.4, U19.15 (O5)
SEL: U6.37 (SELI), U11.16 (O1a)
SELO: U6.36 (SELO), U15.9
SRST: U11.12 (O3a), U14.11
TMPWR: J8.26
WGATE2: U5.16 (WG)
~ACK: J8.38, RN2.4 (R3), U11.2 (I0a)
~ATNB: U5.8 (GPIO3), U11.3 (O3b)
~ATN: J8.32, RN2.2 (R1), U11.17 (I3b)
~BIE: U6.40 (~BIE), U12.1 (OEa), U12.19 (OEb)
~BOE: U6.41 (~BOE), U14.5
~BSY: J8.36, RN2.3 (R2), U11.6 (I2a), U15.3
~CD: U5.6 (GPIO1), U15.4
~ET: U6.38 (~ET), U25.9
~IO: U16.8
~MCU_RD: U5.35 (~RD), U6.18 (~RD)
~MCU_WR: U5.34 (~WR), U6.19 (~WR)
~MSG: J8.42, RN3.6 (R5), U15.11
~MS: U6.32 (~MS), U7.18 (~CS)
~REQ: J8.48, RN3.3 (R2), U16.11
~RST: J8.40, RN3.7 (R6), U11.8 (I3a)
~SEL: J8.44, RN3.5 (R4), U11.4 (I1a), U15.8
~SRAM_WE: U6.33 (~WE), U7.21 (~WE), U14.3
~SRST: U13.9, U14.10, U26.4
~SYSRST: U5.13 (~RST), U6.14 (~RST)
~WAM/~AMD: U5.32 (~WAM/~AMD)

Notes on the sheet:
TERMINATION
This work is licensed under a Creative Commons Attribution-ShareAlike 4.0 International License. See https://creativecommons.org/licenses/by-sa/4.0/.
(BODGE)
ASSY 20427
ST-225N INTELLIGENT
Reverse Engineered by Tube Time
SCSI ID JUMPER
SCSI OUTPUT BUFFERS
SCSI BUFFER SRAM
DUAL PORT BUFFER CONTROLLER
PROGRAMMABLE SCSI CONTROLLER
SCSI INPUT BUFFERS
