schlae/HardDriveInfo/st251/20938/analog.kicad_sch

## KiCad design st251/20938/analog.kicad_sch (2024-06-20)

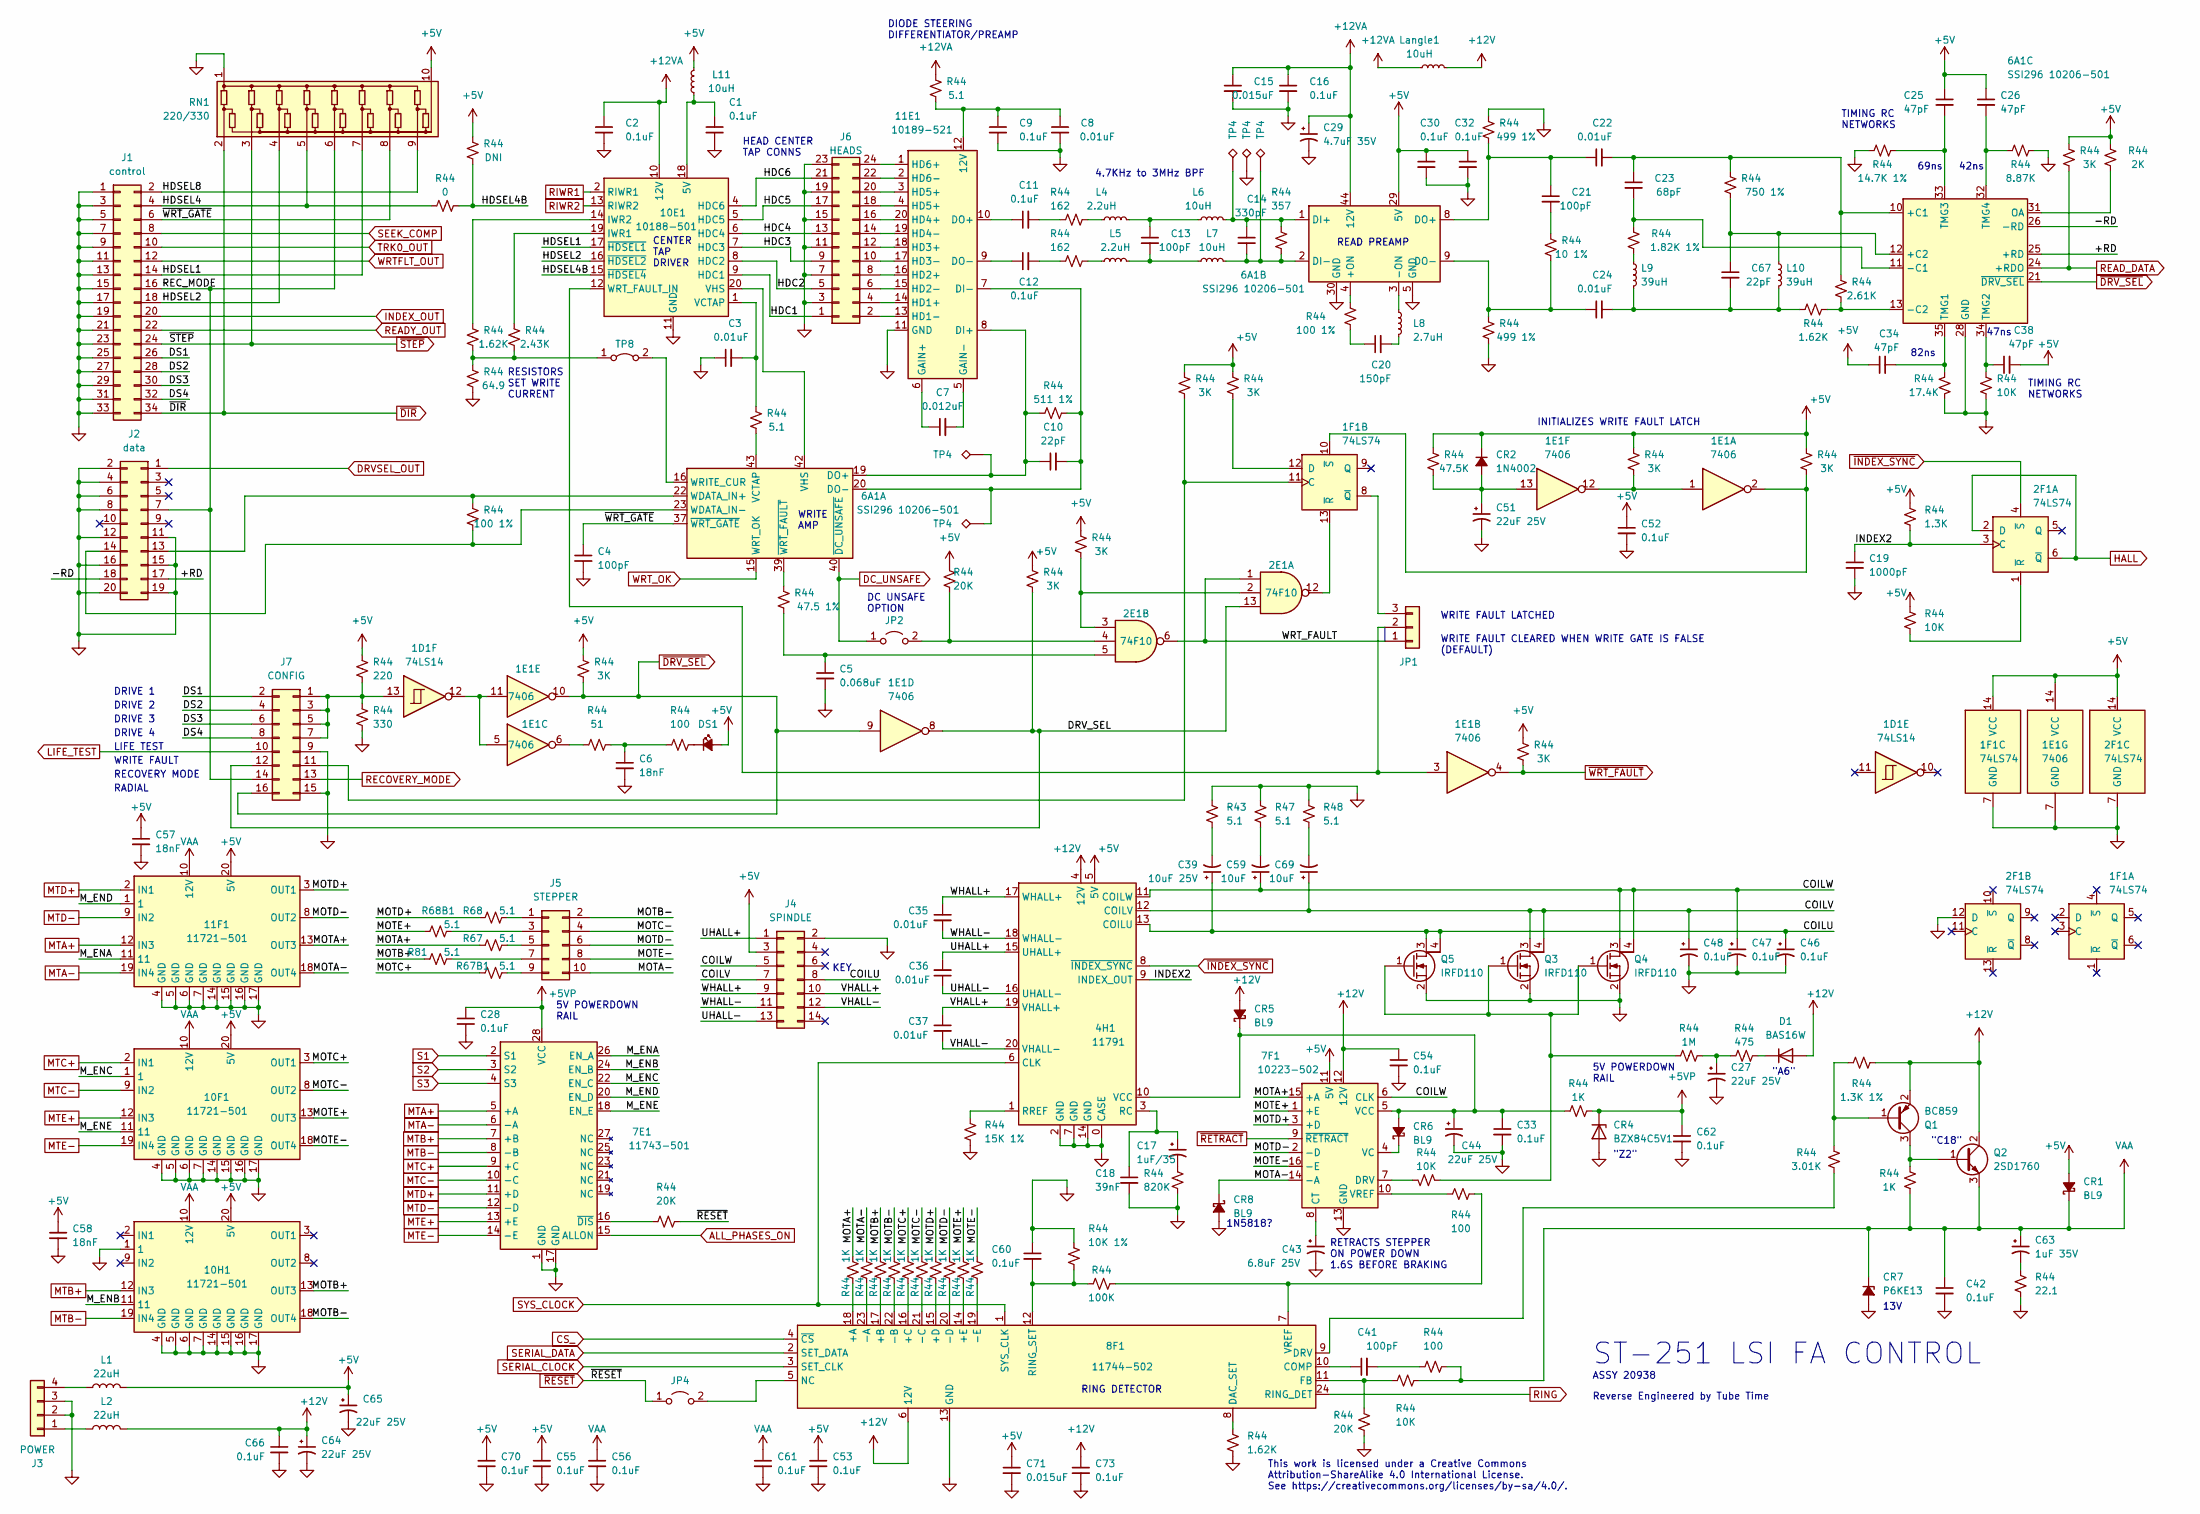
[picture p34: schematic analog.kicad_sch]

Parts:
1D1: 74LS14; SOP127P620X175-14
1E1: 7406; SOP127P620X175-14
1F1, 2F1: 74LS74; SOP127P620X175-14
2E1: 74F10; SOP127P620X175-14
4H1: 11791; MOT_DRIVE
6A1: SSI296 10206-501; PLCC-44_16.6x16.6mm_P1.27mm
7E1: 11743-501; SOP127P1070X255-28
7F1: 10223-502; SOP127P1065X265-16
8F1: 11744-502; SOIC-24W_7.5x15.4mm_P1.27mm
10E1: 10188-501; SOIC-20W_7.5x12.8mm_P1.27mm
10F1, 10H1, 11F1: 11721-501; SOP127P1065X265-20
11E1: 10189-521; SOIC-20W_7.5x12.8mm_P1.27mm
C1, C2, C9, C16, C28, C30, C32, C33, C42, C52, C53, C54, C55, C56, C61, C62, C66, C70, C73: 0.1uF; C_1206_3216Metric
C3, C8, C22, C24, C35, C36, C37: 0.01uF; C_0805_2012Metric
C4, C13, C21, C41: 100pF; C_0805_2012Metric
C5: 0.068uF; C_1210_3225Metric
C6, C57, C58: 18nF; C_0805_2012Metric
C7: 0.012uF; C_1206_3216Metric
C10, C67: 22pF; C_0805_2012Metric
C11, C12, C60: 0.1uF; C_1210_3225Metric
C14: 330pF; C_0805_2012Metric
C15, C71: 0.015uF; C_0805_2012Metric
C17: 1uF/35; CP_EIA-3528-12_Kemet-T
C18: 39nF; C_1206_3216Metric
C19: 1000pF; C_1206_3216Metric
C20: 150pF; C_0805_2012Metric
C23: 68pF; C_0805_2012Metric
C25, C26, C34, C38: 47pF; C_0805_2012Metric
C27, C44, C51, C64, C65: 22uF 25V; CP_EIA-7343-31_Kemet-D
C29: 4.7uF 35V; CP_EIA-6032-20_AVX-F
C39: 10uF 25V; CP_EIA-7343-31_Kemet-D
C43: 6.8uF 25V; CP_EIA-7343-31_Kemet-D
C46, C47, C48: 0.1uF; CP_EIA-3216-10_Kemet-I
C59, C69: 10uF; CP_EIA-7343-31_Kemet-D
C63: 1uF 35V; CP_EIA-3528-12_Kemet-T
CR1, CR5, CR6, CR8: BL9; D_SMA
CR2: 1N4002; D_DO-35_SOD27_P10.16mm_Horizontal
CR4: BZX84C5V1; SOT-23
CR7: P6KE13; D_DO-15_P15.24mm_Horizontal
D1: BAS16W; SOT-323_SC-70
DS1: LED_Small_Filled; PinHeader_1x02_P2.54mm_Vertical
J1: control; EDGE_34_100
J2: data; EDGE_20_100
J3: POWER; Samtec_HPM-04-01-x-S_Straight_1x04_Pitch5.08mm
J4: SPINDLE; PinHeader_2x07_P2.54mm_Vertical
J5: STEPPER; PinHeader_2x05_P2.54mm_Vertical
J6: HEADS; PinHeader_2x12_P2.54mm_Vertical
J7: CONFIG; PinHeader_2x08_P2.54mm_Vertical
JP1: Conn_01x03; PinHeader_1x03_P2.54mm_Vertical
JP2: Jumper_2_Open; PinHeader_1x02_P2.54mm_Vertical
JP4: Jumper_2_Open; R_1206_3216Metric
L1, L2: 22uH; L_Axial_L13.0mm_D4.5mm_P15.24mm_Horizontal_Fastron_HCCC
L4, L5: 2.2uH; L_1206_3216Metric
L6, L7, L11: 10uH; L_1206_3216Metric
L8: 2.7uH; L_1206_3216Metric
L9, L10: 39uH; L_1206_3216Metric
Langle1: 10uH; L_1206_3216Metric
Q1: BC859; SOT95P230X117-3
Q2: 2SD1760; TO-252-2
Q3, Q4, Q5: IRFD110; DIP-4_W7.62mm
R43, R47, R48: 5.1; R_1210_3225Metric
R44: 64.9; R_1206_3216Metric
R67, R67B1, R68, R68B1, R81: 5.1; R_2512_6332Metric_Pad1.40x3.35mm_HandSolder
RN1: 220/330; R_Array_SIP10
TP4: 1/2 STEP; TestPoint_THTPad_1.0x1.0mm_Drill0.5mm
TP8: Jumper_2_Bridged; SolderJumper-2_P1.3mm_Bridged_Pad1.0x1.5mm

Connections:
+5V: 1E1.14 (VCC), 1F1.14 (VCC), 2F1.14 (VCC), 4H1.5 (5V), 6A1.29 (5V), 7F1.11 (5V), 10F1.20 (5V), 10H1.20 (5V), 11F1.20 (5V), C25.1, C26.1, C30.1, C32.1, C34.1, C38.2, C52.1, C53.1, C55.1, C57.1, C58.1, C65.1, C70.1, C71.1, CR1.2 (A), CR2.1 (K), DS1.2 (A), J4.3, L1.2, L11.2, R44.1, R44.2, RN1.10 (COM2)
+5VP: 7E1.28 (VCC), C28.1, C62.1, CR4.3 (K), R44.1
+12V: 4H1.4 (12V), 7F1.12 (12V), 8F1.6 (12V), C54.1, C64.1, C66.1, C73.1, CR5.2 (A), D1.1 (A), L2.2, Langle1.2, Q1.2 (E), Q2.2 (C), R44.1
+12VA: 6A1.44 (12V), 10E1.10 (12V), C2.1, C15.1, C16.1, C29.1, Langle1.1, R44.1
+RD: 6A1.25 (+RD), J2.17
-RD: 6A1.26 (-RD), J2.18
ALL_PHASES_ON: 7E1.15 (ALLON)
COILU: 4H1.13 (COILU), C39.1, C46.1, J4.8, Q5.3 (D), Q5.4 (D)
COILV: 4H1.12 (COILV), C48.1, C69.1, J4.7, Q3.3 (D), Q3.4 (D)
COILW: 4H1.11 (COILW), 7F1.6 (CLK), C47.1, C59.1, J4.5, Q4.3 (D), Q4.4 (D)
CS_: 8F1.4 (~CS)
DC_UNSAFE: 6A1.40 (~DC_UNSAFE), JP2.1 (A)
DRVSEL_OUT: J2.1
DRV_SEL: 1E1.8, 2E1.13, J7.12, R44.1
DS1: J1.26, J7.2
DS2: J1.28, J7.4
DS3: J1.30, J7.6
DS4: J1.32, J7.8
GND: 1E1.7 (GND), 1F1.7 (GND), 2F1.7 (GND), 2F1.12 (D), 4H1.0 (CASE), 4H1.2 (GND), 4H1.7 (GND), 4H1.14 (GND), 6A1.5 (GND), 6A1.28 (GND), 6A1.30 (GND), 7E1.1 (GND), 7E1.17 (GND), 7F1.13 (GND), 8F1.13 (GND), 10E1.11 (GND), 10F1.4 (GND), 10F1.5 (GND), 10F1.6 (GND), 10F1.7 (GND), 10F1.14 (GND), 10F1.15 (GND), 10F1.16 (GND), 10F1.17 (GND), 10H1.1, 10H1.4 (GND), 10H1.5 (GND), 10H1.6 (GND), 10H1.7 (GND), 10H1.14 (GND), 10H1.15 (GND), 10H1.16 (GND), 10H1.17 (GND), 11E1.11 (GND), 11F1.4 (GND), 11F1.5 (GND), 11F1.6 (GND), 11F1.7 (GND), 11F1.14 (GND), 11F1.15 (GND), 11F1.16 (GND), 11F1.17 (GND), C1.2, C2.2, C3.1, C4.2, C5.2, C6.2, C8.2, C9.2, C15.2, C16.2, C18.2, C19.2, C27.2, C28.2, C29.2, C30.2, C32.2, C33.2, C42.2, C43.2, C44.2, C46.2, C47.2, C48.2, C51.2, C52.2, C53.2, C54.2, C55.2, C56.2, C57.2, C58.2, C60.1, C61.2, C62.2, C64.2, C65.2, C66.2, C70.2, C71.2, C73.2, CR4.1 (A), CR7.2 (A), CR8.2 (A), J1.1, J1.3, J1.5, J1.7, J1.9, J1.11, J1.13, J1.15, J1.17, J1.19, J1.21, J1.23, J1.25, J1.27, J1.29, J1.31, J1.33, J2.2, J2.4, J2.6, J2.8, J2.11, J2.12, J2.15, J2.16, J2.19, J2.20, J3.2, J3.3, J4.2, J6.3, J6.7, J6.11, J6.15, J6.19, J6.23, J7.9, J7.15, Q3.2 (S), Q4.2 (S), Q5.2 (S), R43.1, R44.1, R44.2, R47.1, R48.1, RN1.1 (COM1), TP4.1
HALL: 2F1.2 (D), 2F1.6 (~Q)
HDC1: 10E1.9 (HDC1), J6.1
HDC2: 10E1.8 (HDC2), J6.5
HDC3: 10E1.7 (HDC3), J6.9
HDC4: 10E1.6 (HDC4), J6.13
HDC5: 10E1.5 (HDC5), J6.17
HDC6: 10E1.4 (HDC6), J6.21
HDSEL1: 10E1.17 (~HDSEL1), J1.14, RN1.7 (R6)
HDSEL2: 10E1.16 (~HDSEL2), J1.18, RN1.4 (R3)
HDSEL4: J1.4, R44.2, RN1.5 (R4)
HDSEL4B: 10E1.15 (~HDSEL4), R44.1, R44.2
HDSEL8: J1.2, RN1.9 (R8)
INDEX2: 2F1.3 (C), 4H1.9 (INDEX_OUT), C19.1, R44.2
INDEX_OUT: J1.20
LIFE_TEST: J7.10
MOTA+: 7F1.15 (+A), 11F1.13 (OUT3), R44.2, R67.1
MOTA-: 7F1.14 (-A), 11F1.18 (OUT4), CR8.1 (K), J5.10, R44.2
MOTB+: 10H1.13 (OUT3), R44.2, R81.1
MOTB-: 10H1.18 (OUT4), J5.2, R44.2
MOTC+: 10F1.3 (OUT1), R44.2, R67B1.1
MOTC-: 10F1.8 (OUT2), J5.4, R44.2
MOTD+: 7F1.3 (+D), 11F1.3 (OUT1), R44.2, R68.1
MOTD-: 7F1.2 (-D), 11F1.8 (OUT2), J5.6, R44.2
MOTE+: 7F1.1 (+E), 10F1.13 (OUT3), R44.2, R68B1.1
MOTE-: 7F1.16 (-E), 10F1.18 (OUT4), J5.8, R44.2
MTA+: 7E1.5 (+A), 11F1.12 (IN3)
MTA-: 7E1.6 (-A), 11F1.19 (IN4)
MTB+: 7E1.7 (+B), 10H1.12 (IN3)
MTB-: 7E1.8 (-B), 10H1.19 (IN4)
MTC+: 7E1.9 (+C), 10F1.2 (IN1)
MTC-: 7E1.10 (-C), 10F1.9 (IN2)
MTD+: 7E1.11 (+D), 11F1.2 (IN1)
MTD-: 7E1.12 (-D), 11F1.9 (IN2)
MTE+: 7E1.13 (+E), 10F1.12 (IN3)
MTE-: 7E1.14 (-E), 10F1.19 (IN4)
M_ENA: 7E1.26 (EN_A), 11F1.11
M_ENB: 7E1.24 (EN_B), 10H1.11
M_ENC: 7E1.22 (EN_C), 10F1.1
M_END: 7E1.20 (EN_D), 11F1.1
M_ENE: 7E1.18 (EN_E), 10F1.11
unnamed: 1D1.12, 1E1.5, 1E1.11
unnamed: 1D1.13, J7.1, J7.3, J7.5, J7.7, R44.1, R44.2
unnamed: 1E1.1, 1E1.12, R44.1
unnamed: 1E1.2, 1F1.10 (~S), R44.1
unnamed: 1E1.6, R44.2
unnamed: 1E1.13, C51.1, CR2.2 (A), R44.1
unnamed: 1F1.8 (~Q), JP1.3
unnamed: 1F1.11 (C), J7.11, R44.1
unnamed: 1F1.12 (D), R44.1
unnamed: 1F1.13 (~R), 2E1.12
unnamed: 2E1.2, 2E1.3, R44.1
unnamed: 2E1.4, JP2.2 (B), R44.1
unnamed: 2E1.5, C5.1, R44.1
unnamed: 2F1.1 (~R), R44.1
unnamed: 4H1.1 (RREF), R44.2
unnamed: 4H1.3 (RC), C17.1, C18.1
unnamed: 4H1.10 (VCC), 7F1.5 (VCC), C33.1, C44.1, CR5.1 (K), CR6.2 (A), R44.2
unnamed: 6A1.1 (DI+), C14.1, L6.2, R44.1, TP4.1
unnamed: 6A1.2 (DI-), C14.2, L7.2, R44.2, TP4.1
unnamed: 6A1.3 (-ON), L8.1
unnamed: 6A1.4 (+ON), R44.1
unnamed: 6A1.8 (DO+), C21.1, C22.1, R44.2
unnamed: 6A1.9 (DO-), C24.1, R44.1, R44.2
unnamed: 6A1.10 (+C1), C22.2, C23.1, R44.1
unnamed: 6A1.11 (-C1), C23.2, R44.1
unnamed: 6A1.12 (+C2), C67.1, L10.1, R44.2
unnamed: 6A1.13 (-C2), R44.1, R44.2
unnamed: 6A1.16 (WRITE_CUR), TP8.2 (B)
unnamed: 6A1.22 (WDATA_IN+), J2.13, R44.2
unnamed: 6A1.23 (WDATA_IN-), J2.14, R44.1
unnamed: 6A1.31 (OA), R44.1
unnamed: 6A1.32 (TMG4), C26.2, R44.2
unnamed: 6A1.33 (TMG3), C25.2, R44.1
unnamed: 6A1.34 (TMG2), C38.1, R44.1
unnamed: 6A1.35 (TMG1), C34.2, R44.1
unnamed: 6A1.39 (~WRT_FAULT), R44.2
unnamed: 6A1.43 (VCTAP), R44.1
unnamed: 7E1.16 (~DIS), R44.2
unnamed: 7F1.4 (VC), CR6.1 (K)
unnamed: 7F1.7 (DRV), R44.1
unnamed: 7F1.8 (CT), C43.1
unnamed: 7F1.10 (VREF), R44.2
unnamed: 8F1.5 (NC), JP4.2 (B)
unnamed: 8F1.7 (VREF), R44.1, R44.2
unnamed: 8F1.8 (DAC_SET), R44.2
unnamed: 8F1.9 (DRV), R44.2
unnamed: 8F1.10 (COMP), C41.1
unnamed: 8F1.11 (FB), R44.2
unnamed: 8F1.12 (RING_SET), C60.2, R44.1
unnamed: 8F1.14 (+E), R44.1
unnamed: 8F1.15 (+D), R44.1
unnamed: 8F1.16 (+C), R44.1
unnamed: 8F1.17 (+B), R44.1
unnamed: 8F1.18 (+A), R44.1
unnamed: 8F1.19 (-E), R44.1
unnamed: 8F1.20 (-D), R44.1
unnamed: 8F1.21 (-C), R44.1
unnamed: 8F1.22 (-B), R44.1
unnamed: 8F1.23 (-A), R44.1
unnamed: 10E1.1 (VCTAP), C3.2, R44.2
unnamed: 1E1.3, 10E1.12 (WRT_FAULT_IN), JP1.2
unnamed: 10E1.14 (IWR2), R44.1
unnamed: 10E1.18 (5V), C1.1, L11.1
unnamed: 10E1.19 (IWR1), R44.1
unnamed: 6A1.42 (VHS), 10E1.20 (VHS)
unnamed: 11E1.1 (HD6+), J6.24
unnamed: 11E1.2 (HD6-), J6.22
unnamed: 11E1.3 (HD5+), J6.20
unnamed: 11E1.4 (HD5+), J6.18
unnamed: 11E1.5 (GAIN-), C7.2
unnamed: 11E1.6 (GAIN+), C7.1
unnamed: 6A1.20 (DO-), 11E1.7 (DI-), C10.2, R44.2, TP4.1
unnamed: 6A1.19 (DO+), 11E1.8 (DI+), C10.1, R44.1, TP4.1
unnamed: 11E1.9 (DO-), C12.1
unnamed: 11E1.10 (DO+), C11.1
unnamed: 11E1.12 (12V), C8.1, C9.1, R44.2
unnamed: 11E1.13 (HD1-), J6.2
unnamed: 11E1.14 (HD1+), J6.4
unnamed: 11E1.15 (HD2-), J6.6
unnamed: 11E1.16 (HD2+), J6.8
unnamed: 11E1.17 (HD3-), J6.10
unnamed: 11E1.18 (HD3+), J6.12
unnamed: 11E1.19 (HD4-), J6.14
unnamed: 11E1.20 (HD4+), J6.16
unnamed: C6.1, R44.1, R44.2
unnamed: C11.2, R44.2
unnamed: C12.2, R44.2
unnamed: C13.1, L4.2, L6.1
unnamed: C13.2, L5.2, L7.1
unnamed: C17.2, R44.2
unnamed: C20.1, R44.2
unnamed: C20.2, L8.2
unnamed: C21.2, R44.1
unnamed: C24.2, C67.2, L9.2, L10.2, R44.2
unnamed: C27.1, R44.1, R44.2
unnamed: C39.2, R43.2
unnamed: C41.2, R44.2
unnamed: C59.2, R47.2
unnamed: C63.2, R44.2
unnamed: C69.2, R48.2
unnamed: D1.3 (K), R44.2
unnamed: DS1.1 (K), R44.1
unnamed: J3.1, L2.1
unnamed: J3.4, L1.1
unnamed: J5.1, R68.2
unnamed: J5.3, R68B1.2
unnamed: J5.5, R67.2
unnamed: J5.7, R81.2
unnamed: J5.9, R67B1.2
unnamed: L4.1, R44.1
unnamed: L5.1, R44.1
unnamed: L9.1, R44.2
unnamed: Q1.1 (B), R44.1, R44.2
unnamed: Q1.3 (C), Q2.1 (B), R44.1
unnamed: Q3.1 (G), Q4.1 (G), Q5.1 (G), R44.1, R44.2
unnamed: R44.1, R44.2, TP8.1 (A)
READY_OUT: J1.22
READ_DATA: 6A1.24 (+RDO), R44.2
RECOVERY_MODE: J7.13
REC_MODE: J1.16, J2.7, J7.14, RN1.6 (R5)
RING: 8F1.24 (RING_DET)
RIWR1: 10E1.2 (RIWR1)
RIWR2: 10E1.13 (RIWR2)
S1: 7E1.2 (S1)
S2: 7E1.3 (S2)
S3: 7E1.4 (S3)
SEEK_COMP: J1.8
SERIAL_CLOCK: 8F1.3 (SET_CLK)
SERIAL_DATA: 8F1.2 (SET_DATA)
SYS_CLOCK: 4H1.6 (CLK), 8F1.1 (SYS_CLK)
TRK0_OUT: J1.10
UHALL+: 4H1.15 (UHALL+), C36.2, J4.1
UHALL-: 4H1.16 (UHALL-), C36.1, J4.13
VAA: 10F1.10 (12V), 10H1.10 (12V), 11F1.10 (12V), C42.1, C56.1, C61.1, C63.1, CR1.1 (K), CR7.1 (K), Q2.3 (E), R44.1, R44.2
VHALL+: 4H1.19 (VHALL+), C37.1, J4.10
VHALL-: 4H1.20 (VHALL-), C37.2, J4.12
WHALL+: 4H1.17 (WHALL+), C35.1, J4.9
WHALL-: 4H1.18 (WHALL-), C35.2, J4.11
WRTFLT_OUT: J1.12
WRT_FAULT: 2E1.1, 2E1.6, JP1.1
WRT_OK: 6A1.15 (WRT_OK)
~DIR: J1.34, RN1.2 (R1)
~DRV_SEL: 1E1.9, 1E1.10, 6A1.21 (~DRV_SEL), J7.16, R44.1
~INDEX_SYNC: 2F1.4 (~S), 4H1.8 (~INDEX_SYNC)
~RESET: JP4.1 (A), R44.1
~RETRACT: 7F1.9 (~RETRACT)
~STEP: J1.24, RN1.3 (R2)
~WRT_FAULT: 1E1.4, R44.1
~WRT_GATE: 6A1.37 (~WRT_GATE), C4.1, J1.6, RN1.8 (R7)

Notes on the sheet:
LIFE TEST
HEAD CENTER TAP CONNS
TIMING RC NETWORKS
RECOVERY MODE
4.7KHz to 3MHz BPF
"A6"
KEY
"Z2"
ST-251 LSI FA CONTROL
DC UNSAFE OPTION
69ns
42ns
RETRACTS STEPPER ON POWER DOWN 1.6S BEFORE BRAKING
DRIVE 1
Reverse Engineered by Tube Time
ASSY 20938
WRITE FAULT
5V POWERDOWN RAIL
47ns
DRIVE 3
WRITE FAULT CLEARED WHEN WRITE GATE IS FALSE (DEFAULT)
DIODE STEERING DIFFERENTIATOR/PREAMP
13V
RESISTORS SET WRITE CURRENT
DRIVE 4
1N5818?
"C18"
82ns
WRITE FAULT LATCHED
WRITE AMP
DRIVE 2
CENTER TAP DRIVER
RADIAL
INITIALIZES WRITE FAULT LATCH
This work is licensed under a Creative Commons Attribution-ShareAlike 4.0 International License. See https://creativecommons.org/licenses/by-sa/4.0/.
READ PREAMP
RING DETECTOR
