schlae/HardDriveInfo/st251/21020/digital.kicad_sch

## KiCad design st251/21020/digital.kicad_sch (2024-06-27)

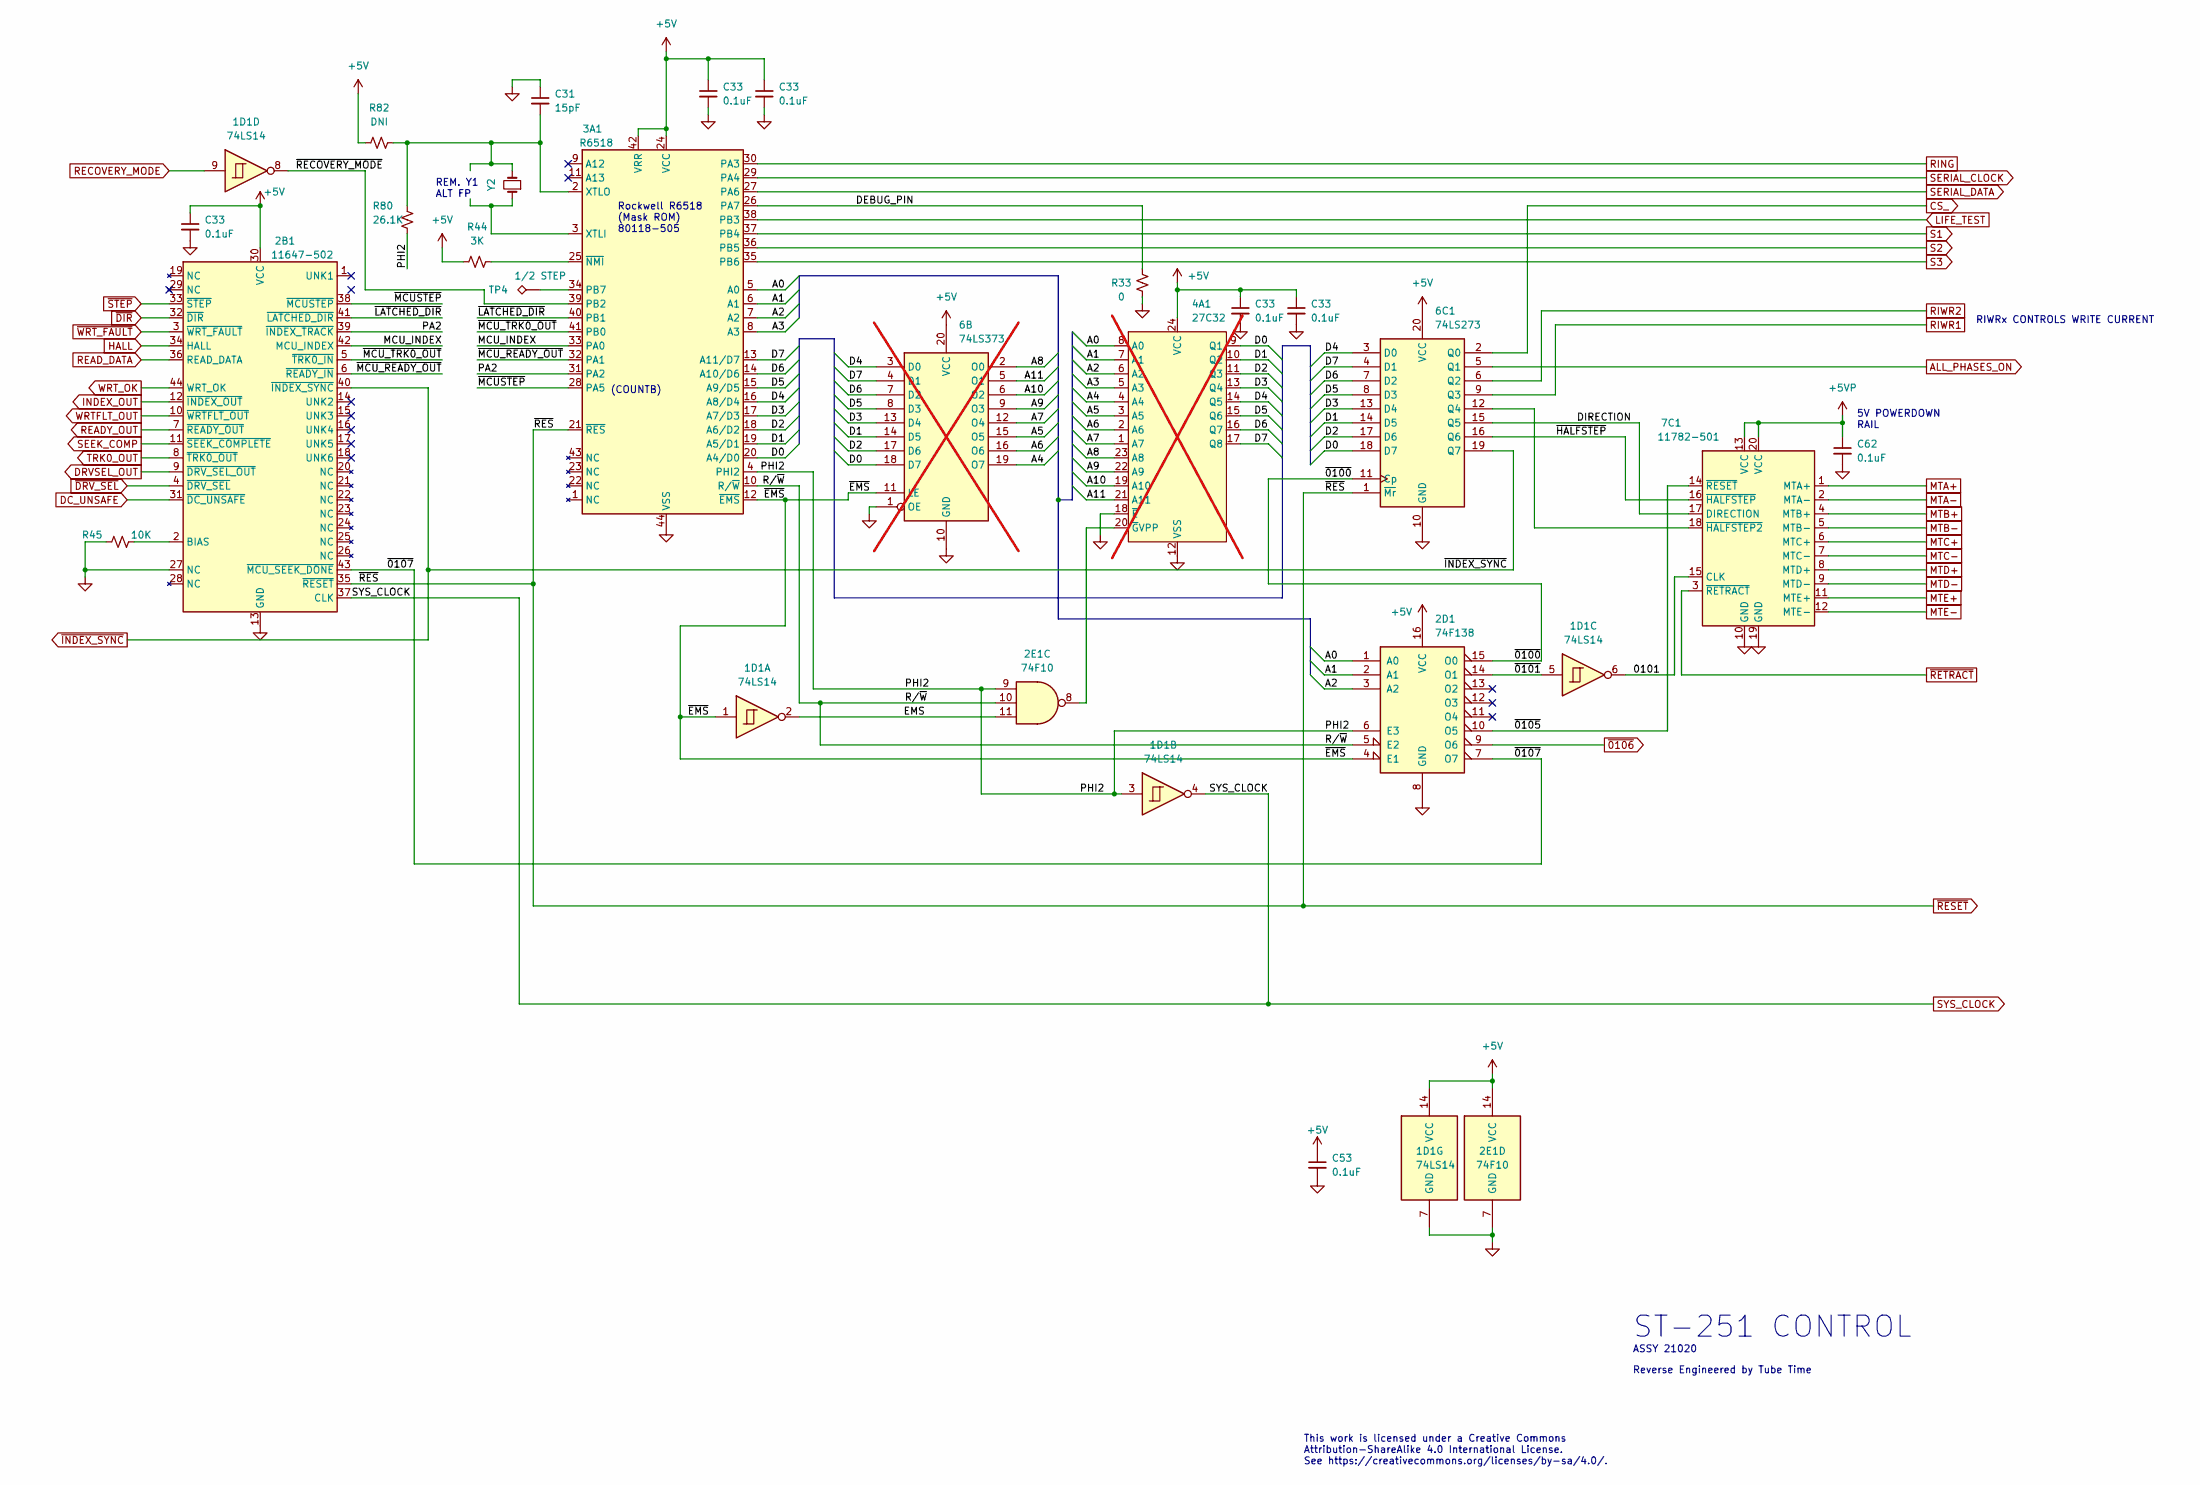
[picture p35: schematic digital.kicad_sch]

Parts:
1D1: 74LS14; SOP127P620X175-14
2B1: 11647-502; PLCC-44_16.6x16.6mm_P1.27mm
2D1: 74F138; SOP127P620X175-16
2E1: 74F10; SOP127P620X175-14
3A1: R6518; PLCC-44_16.6x16.6mm_P1.27mm
4A1: 27C32; DIP254P1524X635-24; not fitted
6B: 74LS373; SOP127P1065X265-20; not fitted
6C1: 74LS273; SOP127P1065X265-20
7C1: 11782-501; SOP127P1065X265-20
C31: 15pF; C_0805_2012Metric
C33, C53, C62: 0.1uF; C_1206_3216Metric
R33: 0; R_1206_3216Metric
R44: 3K; R_1206_3216Metric
R45: 10K; R_1206_3216Metric
R80: 26.1K; R_1206_3216Metric
R82: DNI; R_1206_3216Metric
TP4: 1/2 STEP; TestPoint_THTPad_2.0x2.0mm_Drill1.0mm
Y2: Crystal_Small; Crystal_HC49-U_Vertical

Connections:
0101: 1D1.6, 7C1.15 (CLK)
+5V: 1D1.14 (VCC), 2B1.30 (VCC), 2D1.16 (VCC), 2E1.14 (VCC), 3A1.24 (VCC), 3A1.42 (VRR), 4A1.24 (VCC), 6B.20 (VCC), 6C1.20 (VCC), C33.1, C53.1, R44.1, R82.1
+5VP: 7C1.13 (VCC), 7C1.20 (VCC), C62.1
A0: 2D1.1 (A0), 3A1.5 (A0), 4A1.8 (A0)
A1: 2D1.2 (A1), 3A1.6 (A1), 4A1.7 (A1)
A2: 2D1.3 (A2), 3A1.7 (A2), 4A1.6 (A2)
A3: 3A1.8 (A3), 4A1.5 (A3)
A4: 4A1.4 (A4), 6B.19 (O7)
A5: 4A1.3 (A5), 6B.15 (O5)
A6: 4A1.2 (A6), 6B.16 (O6)
A7: 4A1.1 (A7), 6B.12 (O4)
A8: 4A1.23 (A8), 6B.2 (O0)
A9: 4A1.22 (A9), 6B.9 (O3)
A10: 4A1.19 (A10), 6B.6 (O2)
A11: 4A1.21 (A11), 6B.5 (O1)
ALL_PHASES_ON: 6C1.5 (Q1)
CS_: 6C1.2 (Q0)
D0: 3A1.20 (A4/D0), 4A1.9 (Q1), 6B.18 (D7), 6C1.18 (D7)
D1: 3A1.19 (A5/D1), 4A1.10 (Q2), 6B.14 (D5), 6C1.14 (D5)
D2: 3A1.18 (A6/D2), 4A1.11 (Q3), 6B.17 (D6), 6C1.17 (D6)
D3: 3A1.17 (A7/D3), 4A1.13 (Q4), 6B.13 (D4), 6C1.13 (D4)
D4: 3A1.16 (A8/D4), 4A1.14 (Q5), 6B.3 (D0), 6C1.3 (D0)
D5: 3A1.15 (A9/D5), 4A1.15 (Q6), 6B.8 (D3), 6C1.8 (D3)
D6: 3A1.14 (A10/D6), 4A1.16 (Q7), 6B.7 (D2), 6C1.7 (D2)
D7: 3A1.13 (A11/D7), 4A1.17 (Q8), 6B.4 (D1), 6C1.4 (D1)
DC_UNSAFE: 2B1.31 (~DC_UNSAFE)
DEBUG_PIN: 3A1.26 (PA7), R33.1
DIRECTION: 6C1.15 (Q5), 7C1.17 (DIRECTION)
DRVSEL_OUT: 2B1.9 (~DRV_SEL_OUT)
EMS: 1D1.2, 2E1.11
GND: 1D1.7 (GND), 2B1.13 (GND), 2B1.27 (NC), 2D1.8 (GND), 2E1.7 (GND), 3A1.44 (VSS), 4A1.12 (VSS), 4A1.18 (~E), 6B.1 (OE), 6B.10 (GND), 6C1.10 (GND), 7C1.10 (GND), 7C1.19 (GND), C31.1, C33.2, C53.2, C62.2, R33.2, R45.1
HALL: 2B1.34 (HALL)
INDEX_OUT: 2B1.12 (~INDEX_OUT)
LIFE_TEST: 3A1.38 (PB3)
MCU_INDEX: 2B1.42 (MCU_INDEX), 3A1.33 (PA0)
MTA+: 7C1.1 (MTA+)
MTA-: 7C1.2 (MTA-)
MTB+: 7C1.4 (MTB+)
MTB-: 7C1.5 (MTB-)
MTC+: 7C1.6 (MTC+)
MTC-: 7C1.7 (MTC-)
MTD+: 7C1.8 (MTD+)
MTD-: 7C1.9 (MTD-)
MTE+: 7C1.11 (MTE+)
MTE-: 7C1.12 (MTE-)
unnamed: 2B1.2 (BIAS), R45.2
unnamed: 2E1.8, 4A1.20 (~GVPP)
unnamed: 3A1.2 (XTLO), C31.2, R80.1, R82.2, Y2.2
unnamed: 3A1.3 (XTLI), Y2.1
unnamed: 3A1.25 (~NMI), R44.2
unnamed: 3A1.34 (PB7), TP4.1
unnamed: 6C1.12 (Q4), 7C1.18 (~HALFSTEP2)
PA2: 2B1.39 (~INDEX_TRACK), 3A1.31 (PA2)
PHI2: 1D1.3, 2D1.6 (E3), 2E1.9, 3A1.4 (PHI2), R80.2
READY_OUT: 2B1.7 (~READY_OUT)
READ_DATA: 2B1.36 (READ_DATA)
RECOVERY_MODE: 1D1.9
RING: 3A1.30 (PA3)
RIWR1: 6C1.9 (Q3)
RIWR2: 6C1.6 (Q2)
R/~W: 2D1.5 (E2), 2E1.10, 3A1.10 (R/~W)
S1: 3A1.37 (PB4)
S2: 3A1.36 (PB5)
S3: 3A1.35 (PB6)
SEEK_COMP: 2B1.11 (~SEEK_COMPLETE)
SERIAL_CLOCK: 3A1.29 (PA4)
SERIAL_DATA: 3A1.27 (PA6)
SYS_CLOCK: 1D1.4, 2B1.37 (CLK)
TRK0_OUT: 2B1.8 (~TRK0_OUT)
WRTFLT_OUT: 2B1.10 (~WRTFLT_OUT)
WRT_OK: 2B1.44 (WRT_OK)
~0100: 2D1.15 (O0), 6C1.11 (Cp)
~0101: 1D1.5, 2D1.14 (O1)
~0105: 2D1.10 (O5), 7C1.14 (~RESET)
~0106: 2D1.9 (O6)
~0107: 2B1.43 (~MCU_SEEK_DONE), 2D1.7 (O7)
~DIR: 2B1.32 (~DIR)
~DRV_SEL: 2B1.4 (~DRV_SEL)
~EMS: 1D1.1, 2D1.4 (E1), 3A1.12 (~EMS), 6B.11 (LE)
~HALFSTEP: 6C1.16 (Q6), 7C1.16 (~HALFSTEP)
~INDEX_SYNC: 2B1.40 (~INDEX_SYNC), 6C1.19 (Q7)
~LATCHED_DIR: 2B1.41 (~LATCHED_DIR), 3A1.40 (PB1)
~MCUSTEP: 2B1.38 (~MCUSTEP), 3A1.28 (PA5)
~MCU_READY_OUT: 2B1.6 (~READY_IN), 3A1.32 (PA1)
~MCU_TRK0_OUT: 2B1.5 (~TRK0_IN), 3A1.41 (PB0)
~RECOVERY_MODE: 1D1.8, 3A1.39 (PB2)
~RESET: 2B1.35 (~RESET), 3A1.21 (~RES), 6C1.1 (~Mr)
~RETRACT: 7C1.3 (~RETRACT)
~STEP: 2B1.33 (~STEP)
~WRT_FAULT: 2B1.3 (~WRT_FAULT)

Notes on the sheet:
ASSY 21020
This work is licensed under a Creative Commons Attribution-ShareAlike 4.0 International License. See https://creativecommons.org/licenses/by-sa/4.0/.
Rockwell R6518 (Mask ROM) 80118-505
(COUNTB)
Reverse Engineered by Tube Time
REM. Y1 ALT FP
5V POWERDOWN RAIL
ST-251 CONTROL
RIWRx CONTROLS WRITE CURRENT
