schlae/HardDriveInfo/st251n/20603/SCSI.kicad_sch

## KiCad design st251n/20603/SCSI.kicad_sch (2025-01-09)

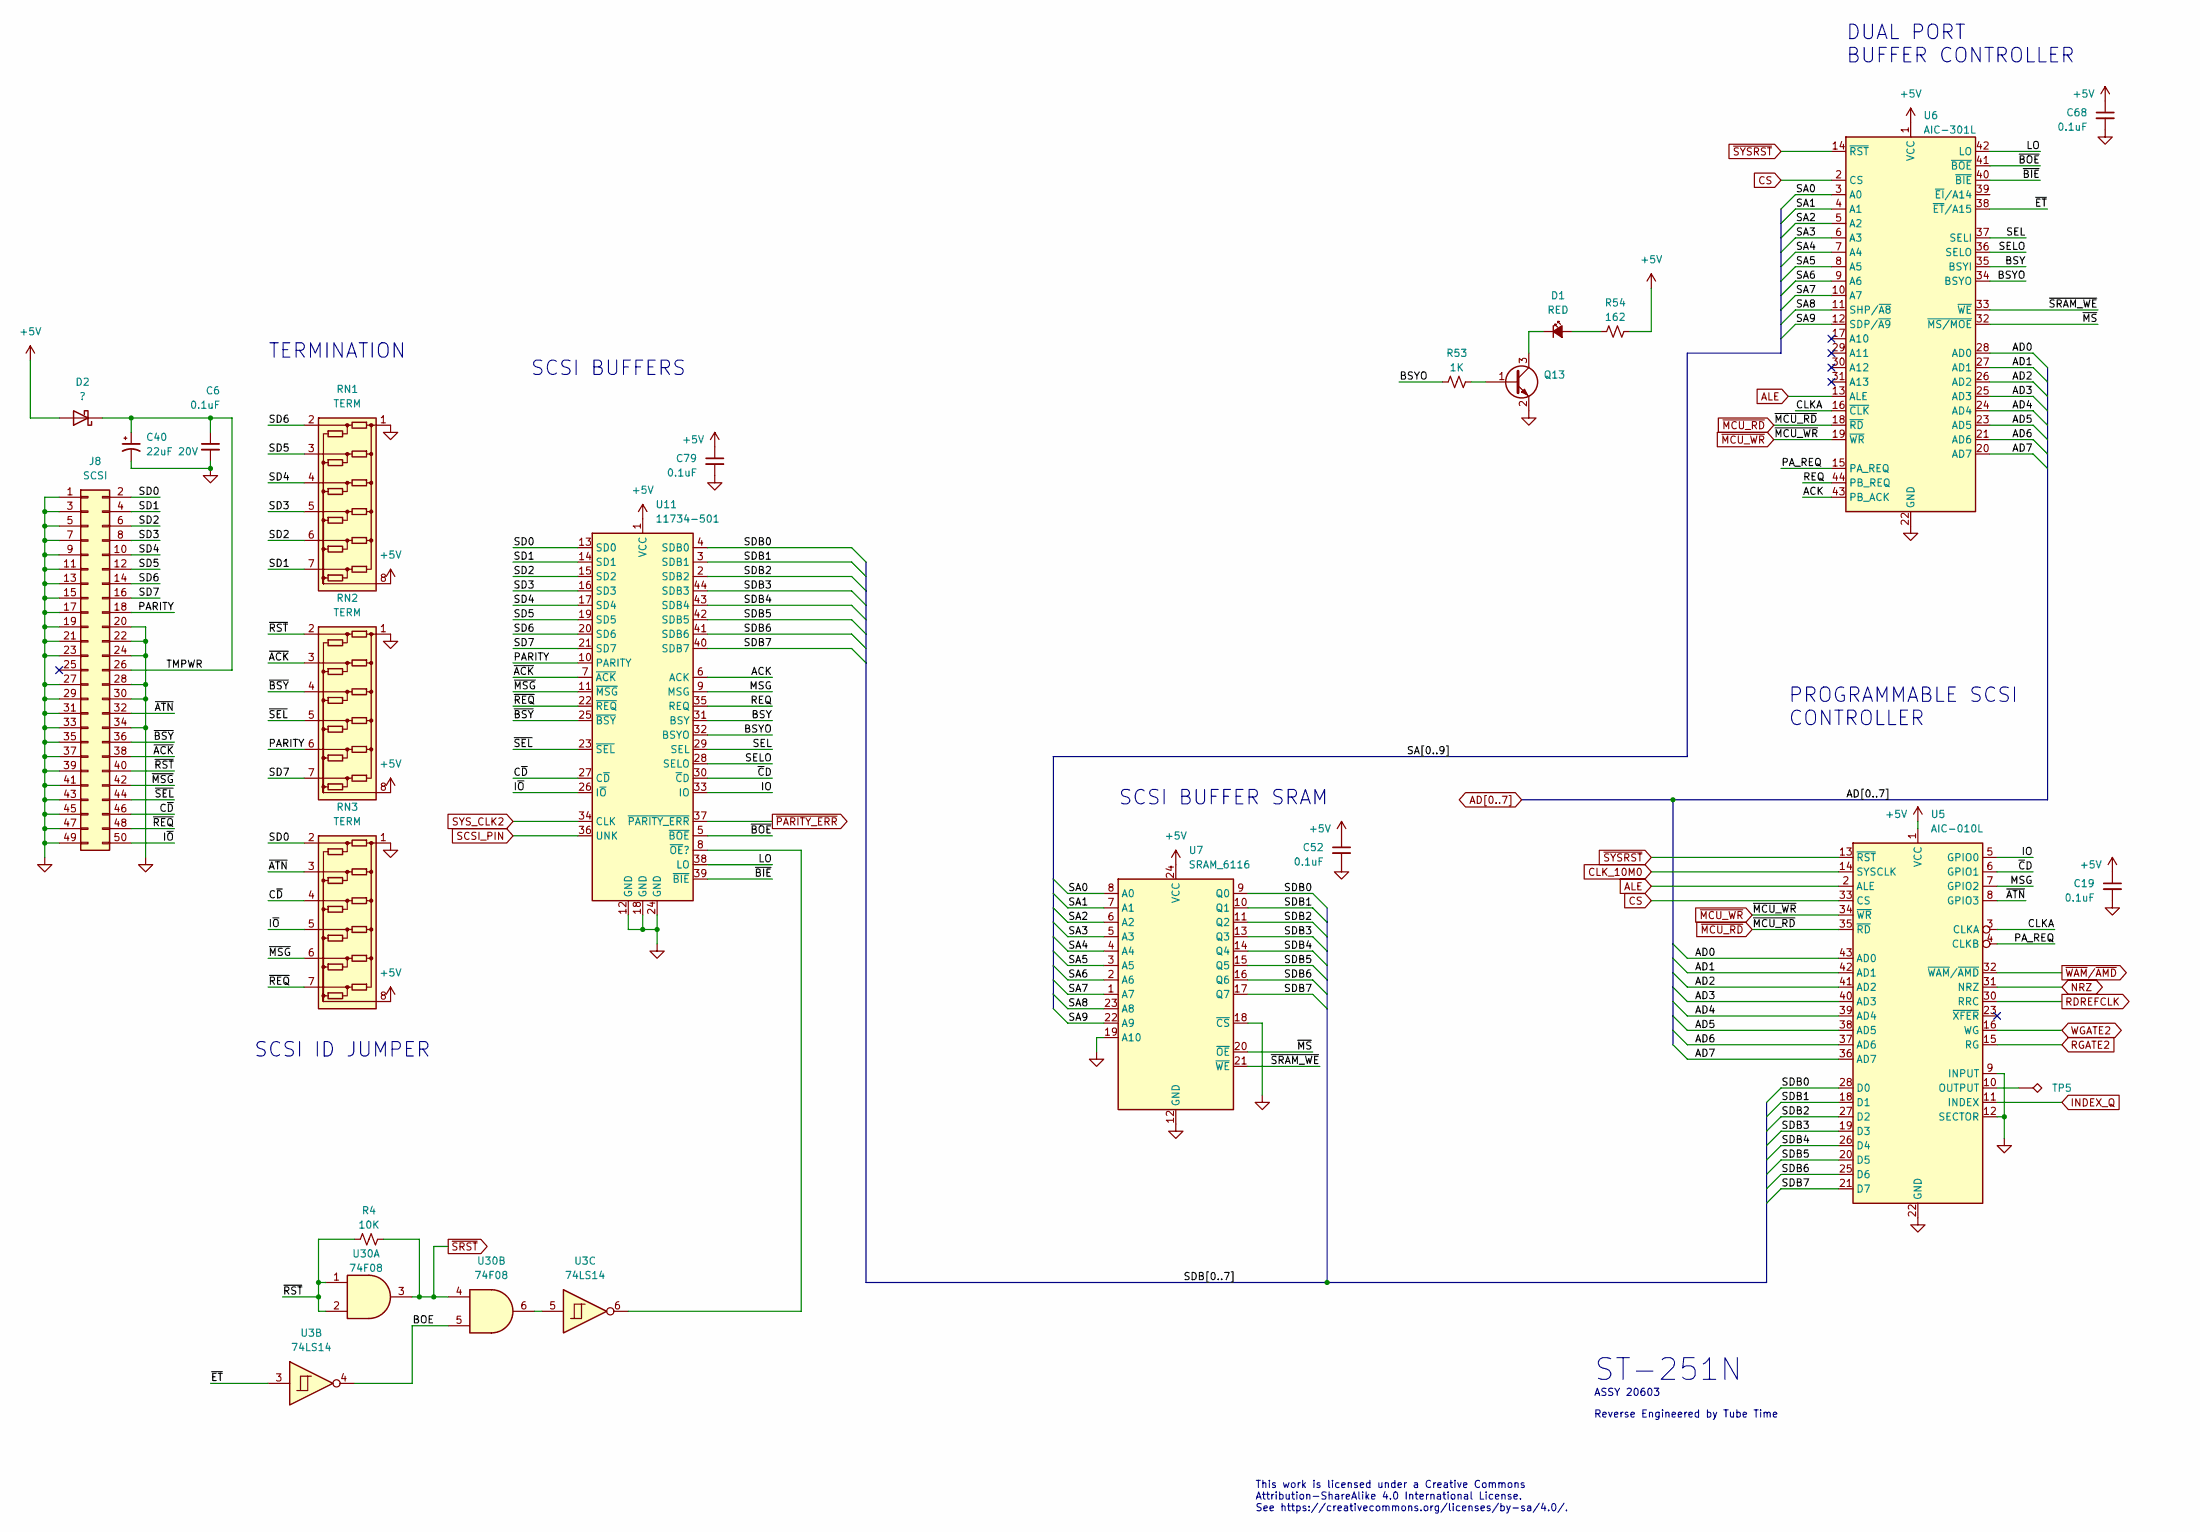
[picture p36: schematic SCSI.kicad_sch]

Parts:
C6, C19, C52, C68, C79: 0.1uF; C_1206_3216Metric
C40: 22uF 20V; CP_EIA-7343-31_Kemet-D
D1: RED; PinHeader_1x02_P2.54mm_Vertical
D2: ?; D_DO-41_SOD81_P12.70mm_Horizontal
J8: SCSI; PinHeader_2x25_P2.54mm_Horizontal
Q13: BC846A; SOT95P230X117-3
R4: 10K; R_1206_3216Metric_Pad1.30x1.75mm_HandSolder
R53: 1K; R_1206_3216Metric_Pad1.30x1.75mm_HandSolder
R54: 162; R_1206_3216Metric
RN1, RN2, RN3: TERM; R_Array_SIP8
TP5: 1/2 STEP; TestPoint_THTPad_1.5x1.5mm_Drill0.7mm
U3: 74LS14; SOP127P620X175-14_SHRINK
U5: AIC-010L; PLCC-44
U6: AIC-301L; PLCC-44
U7: SRAM_6116; SOP127P1250X255-24
U11: 11734-501; PLCC-44_16.6x16.6mm_P1.27mm
U30: 74F08; SOP127P620X175-14_SHRINK

Connections:
+5V: C19.1, C52.1, C68.1, C79.1, D2.2 (A), R54.2, RN1.8 (COM2), RN2.8 (COM2), RN3.8 (COM2), U5.1 (VCC), U6.1 (VCC), U7.24 (VCC), U11.1 (VCC)
ACK: U6.43 (PB_ACK), U11.6 (ACK)
AD0: U5.43 (AD0), U6.28 (AD0)
AD1: U5.42 (AD1), U6.27 (AD1)
AD2: U5.41 (AD2), U6.26 (AD2)
AD3: U5.40 (AD3), U6.25 (AD3)
AD4: U5.39 (AD4), U6.24 (AD4)
AD5: U5.38 (AD5), U6.23 (AD5)
AD6: U5.37 (AD6), U6.21 (AD6)
AD7: U5.36 (AD7), U6.20 (AD7)
ALE: U5.2 (ALE), U6.13 (ALE)
BOE: U3.4, U30.5
BSY: U6.35 (BSYI), U11.31 (BSY)
BSYO: R53.1, U6.34 (BSYO), U11.32 (BSYO)
CLKA: U5.3 (CLKA), U6.16 (~CLK)
CLK_10M0: U5.14 (SYSCLK)
CS: U5.33 (CS), U6.2 (CS)
C~D: J8.46, RN3.4 (R3), U11.27 (C~D)
GND: C6.2, C19.2, C40.2, C52.2, C68.2, C79.2, J8.1, J8.3, J8.5, J8.7, J8.9, J8.11, J8.13, J8.15, J8.17, J8.19, J8.20, J8.21, J8.22, J8.23, J8.24, J8.27, J8.28, J8.29, J8.30, J8.31, J8.33, J8.34, J8.35, J8.37, J8.39, J8.41, J8.43, J8.45, J8.47, J8.49, Q13.2 (E), RN1.1 (COM1), RN2.1 (COM1), RN3.1 (COM1), U5.9 (INPUT), U5.12 (SECTOR), U5.22 (GND), U6.22 (GND), U7.12 (GND), U7.18 (~CS), U7.19 (A10), U11.12 (GND), U11.18 (GND), U11.24 (GND)
INDEX_Q: U5.11 (INDEX)
IO: U5.5 (GPIO0), U11.33 (IO)
I~O: J8.50, RN3.5 (R4), U11.26 (I~O)
LO: U6.42 (LO), U11.38 (LO)
MSG: U5.7 (GPIO2), U11.9 (MSG)
NRZ: U5.31 (NRZ)
unnamed: D1.1 (K), Q13.3 (C)
unnamed: D1.2 (A), R54.1
unnamed: Q13.1 (B), R53.2
unnamed: TP5.1, U5.10 (OUTPUT)
unnamed: U3.5, U30.6
unnamed: U3.6, U11.8 (~OE?)
PARITY: J8.18, RN2.6 (R5), U11.10 (PARITY)
PA_REQ: U5.4 (CLKB), U6.15 (PA_REQ)
RDREFCLK: U5.30 (RRC)
REQ: U6.44 (PB_REQ), U11.35 (REQ)
RGATE2: U5.15 (RG)
SA0: U6.3 (A0), U7.8 (A0)
SA1: U6.4 (A1), U7.7 (A1)
SA2: U6.5 (A2), U7.6 (A2)
SA3: U6.6 (A3), U7.5 (A3)
SA4: U6.7 (A4), U7.4 (A4)
SA5: U6.8 (A5), U7.3 (A5)
SA6: U6.9 (A6), U7.2 (A6)
SA7: U6.10 (A7), U7.1 (A7)
SA8: U6.11 (SHP/~A8), U7.23 (A8)
SA9: U6.12 (SDP/~A9), U7.22 (A9)
SCSI_PIN: U11.36 (UNK)
SD0: J8.2, RN3.2 (R1), U11.13 (SD0)
SD1: J8.4, RN1.7 (R6), U11.14 (SD1)
SD2: J8.6, RN1.6 (R5), U11.15 (SD2)
SD3: J8.8, RN1.5 (R4), U11.16 (SD3)
SD4: J8.10, RN1.4 (R3), U11.17 (SD4)
SD5: J8.12, RN1.3 (R2), U11.19 (SD5)
SD6: J8.14, RN1.2 (R1), U11.20 (SD6)
SD7: J8.16, RN2.7 (R6), U11.21 (SD7)
SDB0: U5.28 (D0), U7.9 (Q0), U11.4 (SDB0)
SDB1: U5.18 (D1), U7.10 (Q1), U11.3 (SDB1)
SDB2: U5.27 (D2), U7.11 (Q2), U11.2 (SDB2)
SDB3: U5.19 (D3), U7.13 (Q3), U11.44 (SDB3)
SDB4: U5.26 (D4), U7.14 (Q4), U11.43 (SDB4)
SDB5: U5.20 (D5), U7.15 (Q5), U11.42 (SDB5)
SDB6: U5.25 (D6), U7.16 (Q6), U11.41 (SDB6)
SDB7: U5.21 (D7), U7.17 (Q7), U11.40 (SDB7)
SEL: U6.37 (SELI), U11.29 (SEL)
SELO: U6.36 (SELO), U11.28 (SELO)
SYS_CLK2: U11.34 (CLK)
TMPWR: C6.1, C40.1, D2.1 (K), J8.26
WGATE2: U5.16 (WG)
~ACK: J8.38, RN2.3 (R2), U11.7 (~ACK)
~ATN: J8.32, RN3.3 (R2), U5.8 (GPIO3)
~BIE: U6.40 (~BIE), U11.39 (~BIE)
~BOE: U6.41 (~BOE), U11.5 (~BOE)
~BSY: J8.36, RN2.4 (R3), U11.25 (~BSY)
~CD: U5.6 (GPIO1), U11.30 (~CD)
~ET: U3.3, U6.38 (~ET/A15)
~MCU_RD: U5.35 (~RD), U6.18 (~RD)
~MCU_WR: U5.34 (~WR), U6.19 (~WR)
~MSG: J8.42, RN3.6 (R5), U11.11 (~MSG)
~MS: U6.32 (~MS/MOE), U7.20 (~OE)
~PARITY_ERR: U11.37 (~PARITY_ERR)
~REQ: J8.48, RN3.7 (R6), U11.22 (~REQ)
~RST: J8.40, R4.1, RN2.2 (R1), U30.1, U30.2
~SEL: J8.44, RN2.5 (R4), U11.23 (~SEL)
~SRAM_WE: U6.33 (~WE), U7.21 (~WE)
~SRST: R4.2, U30.3, U30.4
~SYSRST: U5.13 (~RST), U6.14 (~RST)
~WAM/~AMD: U5.32 (~WAM/~AMD)

Notes on the sheet:
TERMINATION
This work is licensed under a Creative Commons Attribution-ShareAlike 4.0 International License. See https://creativecommons.org/licenses/by-sa/4.0/.
ASSY 20603
ST-251N
Reverse Engineered by Tube Time
SCSI ID JUMPER
SCSI BUFFER SRAM
DUAL PORT BUFFER CONTROLLER
PROGRAMMABLE SCSI CONTROLLER
SCSI BUFFERS
