schlae/HardDriveInfo/st251n/20603/digital.kicad_sch

## KiCad design st251n/20603/digital.kicad_sch (2025-01-09)

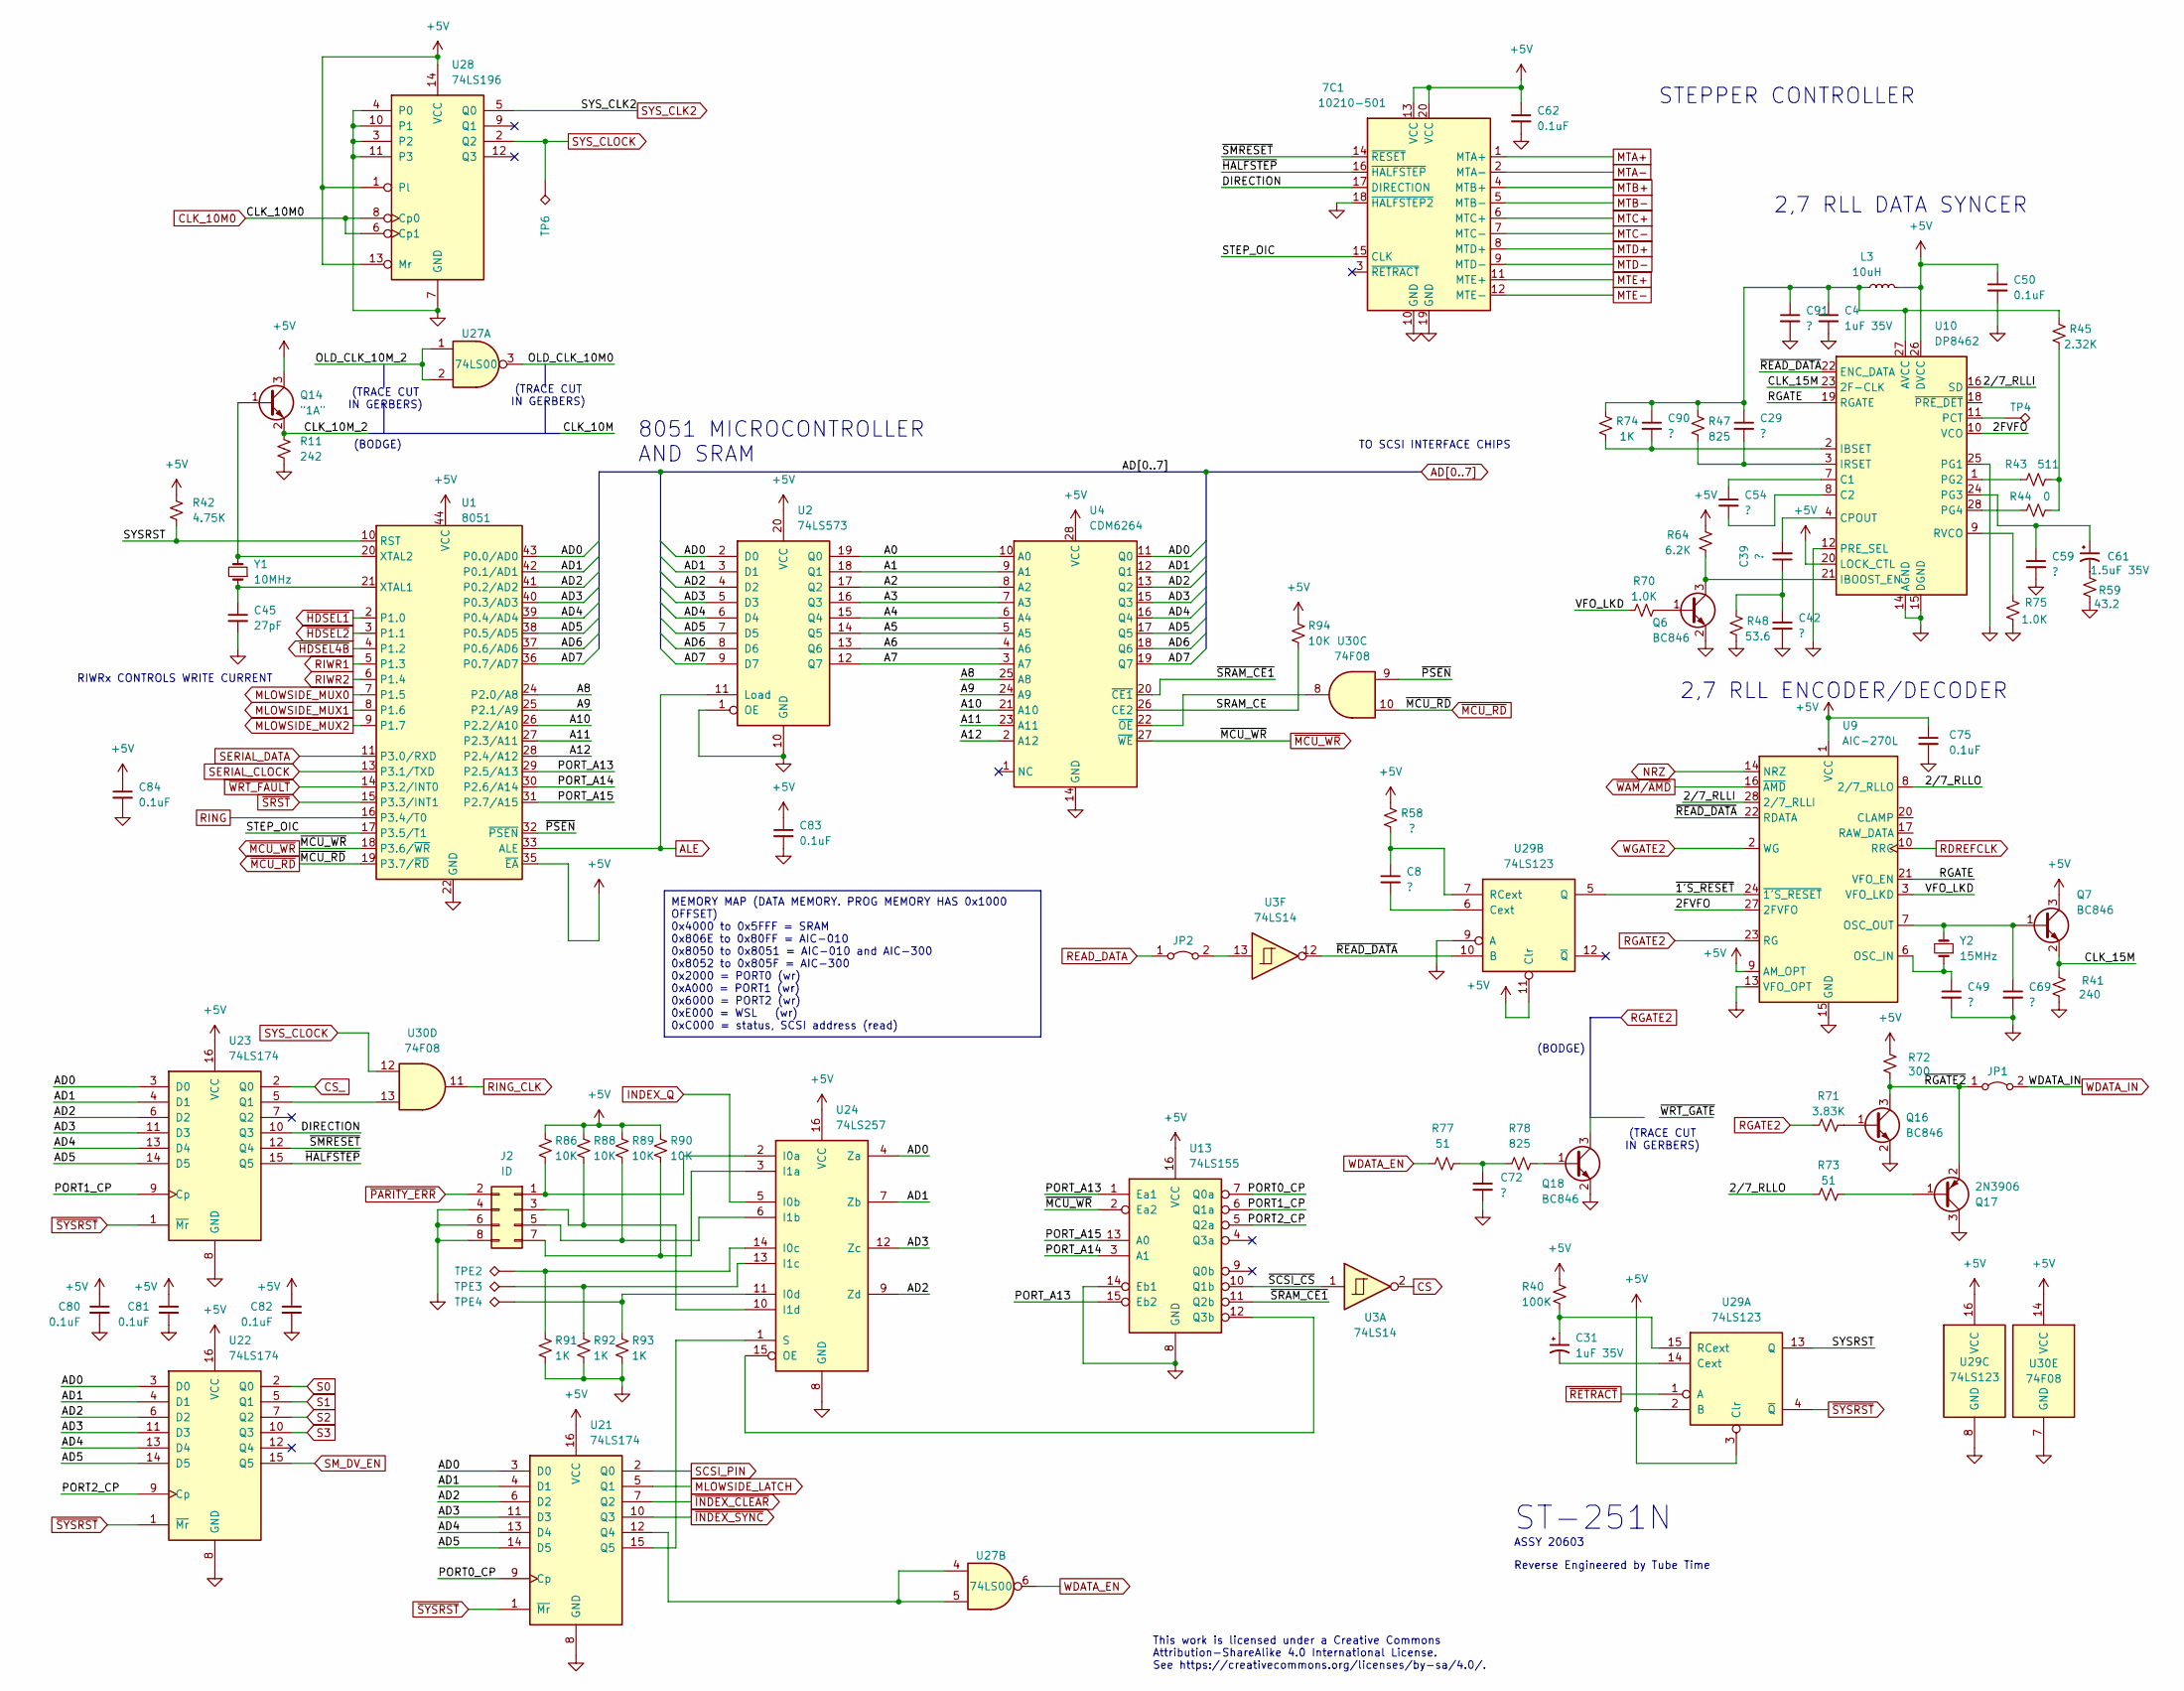
[picture p38: schematic digital.kicad_sch]

Parts:
7C1: 10210-501; SOP127P1065X265-20
C4: 1uF 35V; C_1210_3225Metric
C8, C29, C42, C49, C54, C69, C90: ?; C_0805_2012Metric
C31: 1uF 35V; CP_EIA-7343-31_Kemet-D
C39, C59: ?; C_1210_3225Metric
C45: 27pF; C_0805_2012Metric
C50: 0.1uF; C_1210_3225Metric
C61: 1.5uF 35V; CP_EIA-7343-31_Kemet-D
C62, C75, C80, C81, C82, C83, C84: 0.1uF; C_1206_3216Metric
C72, C91: ?; C_1206_3216Metric
J2: ID; PinHeader_2x04_P2.54mm_Vertical
JP1, JP2: Jumper_2_Bridged; PinHeader_1x02_P2.54mm_Vertical
L3: 10uH; L_1206_3216Metric
Q6, Q7, Q16, Q18: BC846; SOT95P230X117-3
Q14: "1A"; SOT95P230X117-3
Q17: 2N3906; SOT95P230X117-3
R11: 242; R_1206_3216Metric_Pad1.30x1.75mm_HandSolder
R40: 100K; R_1206_3216Metric_Pad1.30x1.75mm_HandSolder
R41: 240; R_1206_3216Metric_Pad1.30x1.75mm_HandSolder
R42: 4.75K; R_1206_3216Metric_Pad1.30x1.75mm_HandSolder
R43: 511; R_1206_3216Metric_Pad1.30x1.75mm_HandSolder
R44: 0; R_1206_3216Metric_Pad1.30x1.75mm_HandSolder
R45: 2.32K; R_1206_3216Metric_Pad1.30x1.75mm_HandSolder
R47: 825; R_1206_3216Metric_Pad1.30x1.75mm_HandSolder
R48: 53.6; R_1206_3216Metric_Pad1.30x1.75mm_HandSolder
R58: ?; R_Axial_DIN0204_L3.6mm_D1.6mm_P7.62mm_Horizontal
R59: 43.2; R_1206_3216Metric_Pad1.30x1.75mm_HandSolder
R64: 6.2K; R_1206_3216Metric_Pad1.30x1.75mm_HandSolder
R70, R75: 1.0K; R_1206_3216Metric_Pad1.30x1.75mm_HandSolder
R71: 3.83K; R_1206_3216Metric_Pad1.30x1.75mm_HandSolder
R72: 300; R_1210_3225Metric
R73: 51; R_1206_3216Metric_Pad1.30x1.75mm_HandSolder
R74, R91, R92, R93: 1K; R_1206_3216Metric_Pad1.30x1.75mm_HandSolder
R77: 51; R_1206_3216Metric
R78: 825; R_1206_3216Metric
R86, R88, R89, R90, R94: 10K; R_1206_3216Metric_Pad1.30x1.75mm_HandSolder
TP4, TP6: 1/2 STEP; TestPoint_THTPad_1.5x1.5mm_Drill0.7mm
TPE2, TPE3, TPE4: 1/2 STEP; TestPoint_THTPad_D2.5mm_Drill1.2mm
U1: 8051; PLCC-44
U2: 74LS573; SOP127P1065X265-20_SHRINK
U3: 74LS14; SOP127P620X175-14_SHRINK
U4: CDM6264; SOP127P1270X305-28_SHRINK
U9: AIC-270L; PLCC-28
U10: DP8462; PLCC-28
U13: 74LS155; SOP127P620X175-16_SHRINK
U21, U22, U23: 74LS174; SOP127P620X175-16_SHRINK
U24: 74LS257; SOP127P620X175-16_SHRINK
U27: 74LS00; SOP127P620X175-14_SHRINK
U28: 74LS196; SOP127P620X175-14_SHRINK
U29: 74LS123; SOP127P620X175-16_SHRINK
U30: 74F08; SOP127P620X175-14_SHRINK
Y1: 10MHz; Crystal_SMD_HC49-SD
Y2: 15MHz; Crystal_SMD_HC49-SD

Connections:
2FVFO: U9.27 (2FVFO), U10.10 (VCO)
2/7_RLLI: U9.28 (2/7_RLLI), U10.16 (SD)
2/7_RLLO: R73.2, U9.8 (2/7_RLLO)
+5V: 7C1.13 (VCC), 7C1.20 (VCC), C50.1, C62.1, C75.1, C80.1, C81.1, C82.1, C83.1, C84.1, L3.2, Q7.3 (C), Q14.3 (C), R40.1, R42.2, R58.1, R64.1, R72.2, R86.2, R88.2, R89.2, R90.2, R94.2, U1.35 (~EA), U1.44 (VCC), U2.20 (VCC), U4.28 (VCC), U9.1 (VCC), U9.9 (AM_OPT), U10.20 (LOCK_CTL), U10.26 (DVCC), U13.16 (VCC), U21.16 (VCC), U22.16 (VCC), U23.16 (VCC), U24.16 (VCC), U28.1 (Pl), U28.13 (Mr), U28.14 (VCC), U29.2 (B), U29.3 (Clr), U29.11 (Clr), U29.16 (VCC), U30.14 (VCC)
A0: U2.19 (Q0), U4.10 (A0)
A1: U2.18 (Q1), U4.9 (A1)
A2: U2.17 (Q2), U4.8 (A2)
A3: U2.16 (Q3), U4.7 (A3)
A4: U2.15 (Q4), U4.6 (A4)
A5: U2.14 (Q5), U4.5 (A5)
A6: U2.13 (Q6), U4.4 (A6)
A7: U2.12 (Q7), U4.3 (A7)
A8: U1.24 (P2.0/A8), U4.25 (A8)
A9: U1.25 (P2.1/A9), U4.24 (A9)
A10: U1.26 (P2.2/A10), U4.21 (A10)
A11: U1.27 (P2.3/A11), U4.23 (A11)
A12: U1.28 (P2.4/A12), U4.2 (A12)
AD0: U1.43 (P0.0/AD0), U2.2 (D0), U4.11 (Q0), U21.3 (D0), U22.3 (D0), U23.3 (D0), U24.4 (Za)
AD1: U1.42 (P0.1/AD1), U2.3 (D1), U4.12 (Q1), U21.4 (D1), U22.4 (D1), U23.4 (D1), U24.7 (Zb)
AD2: U1.41 (P0.2/AD2), U2.4 (D2), U4.13 (Q2), U21.6 (D2), U22.6 (D2), U23.6 (D2), U24.9 (Zd)
AD3: U1.40 (P0.3/AD3), U2.5 (D3), U4.15 (Q3), U21.11 (D3), U22.11 (D3), U23.11 (D3), U24.12 (Zc)
AD4: U1.39 (P0.4/AD4), U2.6 (D4), U4.16 (Q4), U21.13 (D4), U22.13 (D4), U23.13 (D4)
AD5: U1.38 (P0.5/AD5), U2.7 (D5), U4.17 (Q5), U21.14 (D5), U22.14 (D5), U23.14 (D5)
AD6: U1.37 (P0.6/AD6), U2.8 (D6), U4.18 (Q6)
AD7: U1.36 (P0.7/AD7), U2.9 (D7), U4.19 (Q7)
ALE: U1.33 (ALE), U2.11 (Load)
CLK_10M0: U28.6 (Cp1), U28.8 (Cp0)
CLK_10M_2: Q14.2 (E), R11.2
CLK_15M: Q7.2 (E), R41.2, U10.23 (2F-CLK)
CS: U3.2
CS_: U23.2 (Q0)
DIRECTION: 7C1.17 (DIRECTION), U23.10 (Q3)
GND: 7C1.10 (GND), 7C1.18 (~HALFSTEP2), 7C1.19 (GND), C4.2, C42.2, C45.2, C49.2, C50.2, C59.2, C62.2, C69.2, C72.2, C75.2, C80.2, C81.2, C82.2, C83.2, C84.2, C91.2, J2.4, J2.6, J2.8, Q6.2 (E), Q16.2 (E), Q17.3 (C), Q18.2 (E), R11.1, R41.1, R48.2, R59.1, R75.1, R91.1, R92.1, R93.1, U1.22 (GND), U2.1 (OE), U2.10 (GND), U4.14 (GND), U9.13 (VFO_OPT), U9.15 (GND), U10.12 (PRE_SEL), U10.14 (AGND), U10.15 (DGND), U10.25 (PG1), U13.8 (GND), U13.14 (Eb1), U21.8 (GND), U22.8 (GND), U23.8 (GND), U24.8 (GND), U28.3 (P2), U28.4 (P0), U28.7 (GND), U28.10 (P1), U28.11 (P3), U29.8 (GND), U29.9 (A), U30.7 (GND)
INDEX_Q: U24.5 (I0b)
MLOWSIDE_LATCH: U21.5 (Q1)
MLOWSIDE_MUX0: U1.7 (P1.5)
MLOWSIDE_MUX1: U1.8 (P1.6)
MLOWSIDE_MUX2: U1.9 (P1.7)
MTA+: 7C1.1 (MTA+)
MTA-: 7C1.2 (MTA-)
MTB+: 7C1.4 (MTB+)
MTB-: 7C1.5 (MTB-)
MTC+: 7C1.6 (MTC+)
MTC-: 7C1.7 (MTC-)
MTD+: 7C1.8 (MTD+)
MTD-: 7C1.9 (MTD-)
MTE+: 7C1.11 (MTE+)
MTE-: 7C1.12 (MTE-)
NRZ: U9.14 (NRZ)
unnamed: C8.1, R58.2, U29.7 (RCext)
unnamed: C8.2, U29.6 (Cext)
unnamed: C4.1, C29.1, C90.1, C91.1, L3.1, R45.1, R47.1, R74.1, U10.27 (AVCC)
unnamed: C29.2, R47.2, U10.3 (IRSET)
unnamed: C31.1, R40.2, U29.15 (RCext)
unnamed: C31.2, U29.14 (Cext)
unnamed: C39.1, C42.1, R48.1
unnamed: C39.2, U10.4 (CPOUT)
unnamed: C45.1, U1.21 (XTAL1), Y1.1
unnamed: C49.1, U9.6 (OSC_IN), Y2.1
unnamed: C54.1, U10.7 (C1)
unnamed: C54.2, U10.8 (C2)
unnamed: C59.1, C61.1, U10.24 (PG3)
unnamed: C61.2, R59.2
unnamed: C69.1, Q7.1 (B), U9.7 (OSC_OUT), Y2.2
unnamed: C72.1, R77.2, R78.1
unnamed: C90.2, R74.2, U10.2 (IBSET)
unnamed: J2.1, R86.1, U24.2 (I0a)
unnamed: J2.3, R88.1, U24.10 (I1d)
unnamed: J2.5, R89.1, U24.6 (I1b)
unnamed: J2.7, R90.1, U24.3 (I1a)
unnamed: JP2.2 (B), U3.13
unnamed: Q6.1 (B), R70.1
unnamed: Q6.3 (C), R64.2, U10.21 (IBOOST_EN)
unnamed: Q14.1 (B), U1.20 (XTAL2), Y1.2
unnamed: Q16.1 (B), R71.1
unnamed: Q17.1 (B), R73.1
unnamed: Q18.1 (B), R78.2
unnamed: R43.1, U10.1 (PG2)
unnamed: R43.2, R44.2, R45.2
unnamed: R44.1, U10.28 (PG4)
unnamed: R75.2, U10.9 (RVCO)
unnamed: R91.2, TPE2.1, U24.14 (I0c)
unnamed: R92.2, TPE3.1, U24.13 (I1c)
unnamed: R93.2, TPE4.1, U24.11 (I0d)
unnamed: TP4.1, U10.11 (PCT)
unnamed: U13.12 (Q3b), U24.15 (OE)
unnamed: U21.12 (Q4), U27.4, U27.5
unnamed: U21.15 (Q5), U24.1 (S)
unnamed: U23.5 (Q1), U30.13
unnamed: U4.22 (~OE), U30.8
OLD_CLK_10M0: U27.3
OLD_CLK_10M_2: U27.1, U27.2
PORT0_CP: U13.7 (Q0a), U21.9 (Cp)
PORT1_CP: U13.6 (Q1a), U23.9 (Cp)
PORT2_CP: U13.5 (Q2a), U22.9 (Cp)
PORT_A13: U1.29 (P2.5/A13), U13.1 (Ea1), U13.15 (Eb2)
PORT_A14: U1.30 (P2.6/A14), U13.3 (A1)
PORT_A15: U1.31 (P2.7/A15), U13.13 (A0)
RDREFCLK: U9.10 (RRC)
READ_DATA: JP2.1 (A)
RGATE: U9.21 (VFO_EN), U10.19 (RGATE)
RGATE2: R71.2, U9.23 (RG)
RING: U1.16 (P3.4/T0)
RING_CLK: U30.11
RIWR1: U1.5 (P1.3)
RIWR2: U1.6 (P1.4)
S0: U22.2 (Q0)
S1: U22.5 (Q1)
S2: U22.7 (Q2)
S3: U22.10 (Q3)
SCSI_PIN: U21.2 (Q0)
SERIAL_CLOCK: U1.13 (P3.1/TXD)
SERIAL_DATA: U1.11 (P3.0/RXD)
SM_DV_EN: U22.15 (Q5)
SRAM_CE: R94.1, U4.26 (CE2)
STEP_OIC: 7C1.15 (CLK), U1.17 (P3.5/T1)
SYSRST: R42.1, U1.10 (RST), U29.13 (Q)
SYS_CLK2: U28.5 (Q0)
SYS_CLOCK: TP6.1, U28.2 (Q2), U30.12
VFO_LKD: R70.2, U9.3 (VFO_LKD)
WDATA_EN: R77.1, U27.6
WDATA_IN: JP1.2 (B)
WGATE2: U9.2 (WG)
~1'S_RESET: U9.24 (~1'S_RESET), U29.5 (Q)
~HALFSTEP: 7C1.16 (~HALFSTEP), U23.15 (Q5)
~HDSEL1: U1.2 (P1.0)
~HDSEL2: U1.3 (P1.1)
~HDSEL4B: U1.4 (P1.2)
~INDEX_CLEAR: U21.7 (Q2)
~INDEX_SYNC: U21.10 (Q3)
~MCU_RD: U1.19 (P3.7/~RD), U30.10
~MCU_WR: U1.18 (P3.6/~WR), U4.27 (~WE), U13.2 (Ea2)
~PARITY_ERR: J2.2
~PSEN: U1.32 (~PSEN), U30.9
~READ_DATA: U3.12, U9.22 (RDATA), U10.22 (ENC_DATA), U29.10 (B)
~RETRACT: U29.1 (A)
~RGATE2: JP1.1 (A), Q16.3 (C), Q17.2 (E), R72.1
~SCSI_CS: U3.1, U13.10 (Q1b)
~SMRESET: 7C1.14 (~RESET), U23.12 (Q4)
~SRAM_CE1: U4.20 (~CE1), U13.11 (Q2b)
~SRST: U1.15 (P3.3/INT1)
~SYSRST: U21.1 (~Mr), U22.1 (~Mr), U23.1 (~Mr), U29.4 (~Q)
~WAM/~AMD: U9.16 (~AMD)
~WRT_FAULT: U1.14 (P3.2/INT0)

Notes on the sheet:
MEMORY MAP (DATA MEMORY. PROG MEMORY HAS 0x1000 OFFSET) 0x4000 to 0x5FFF = SRAM 0x806E to 0x80FF = AIC-010 0x8050 to 0x8051 = AIC-010 and AIC-300 0x8052 to 0x805F = AIC-300 0x2000 = PORT0 (wr) 0xA000 = PORT1 (wr) 0x6000 = PORT2 (wr) 0xE000 = WSL (wr) 0xC000 = status, SCSI address (read)
(TRACE CUT IN GERBERS)
ASSY 20603
This work is licensed under a Creative Commons Attribution-ShareAlike 4.0 International License. See https://creativecommons.org/licenses/by-sa/4.0/.
2,7 RLL DATA SYNCER
Reverse Engineered by Tube Time
2,7 RLL ENCODER/DECODER
STEPPER CONTROLLER
(BODGE)
8051 MICROCONTROLLER AND SRAM
TO SCSI INTERFACE CHIPS
ST-251N
RIWRx CONTROLS WRITE CURRENT
