schlae/HardDriveInfo/st296n/20741/analog.kicad_sch

## KiCad design st296n/20741/analog.kicad_sch (2025-01-09)

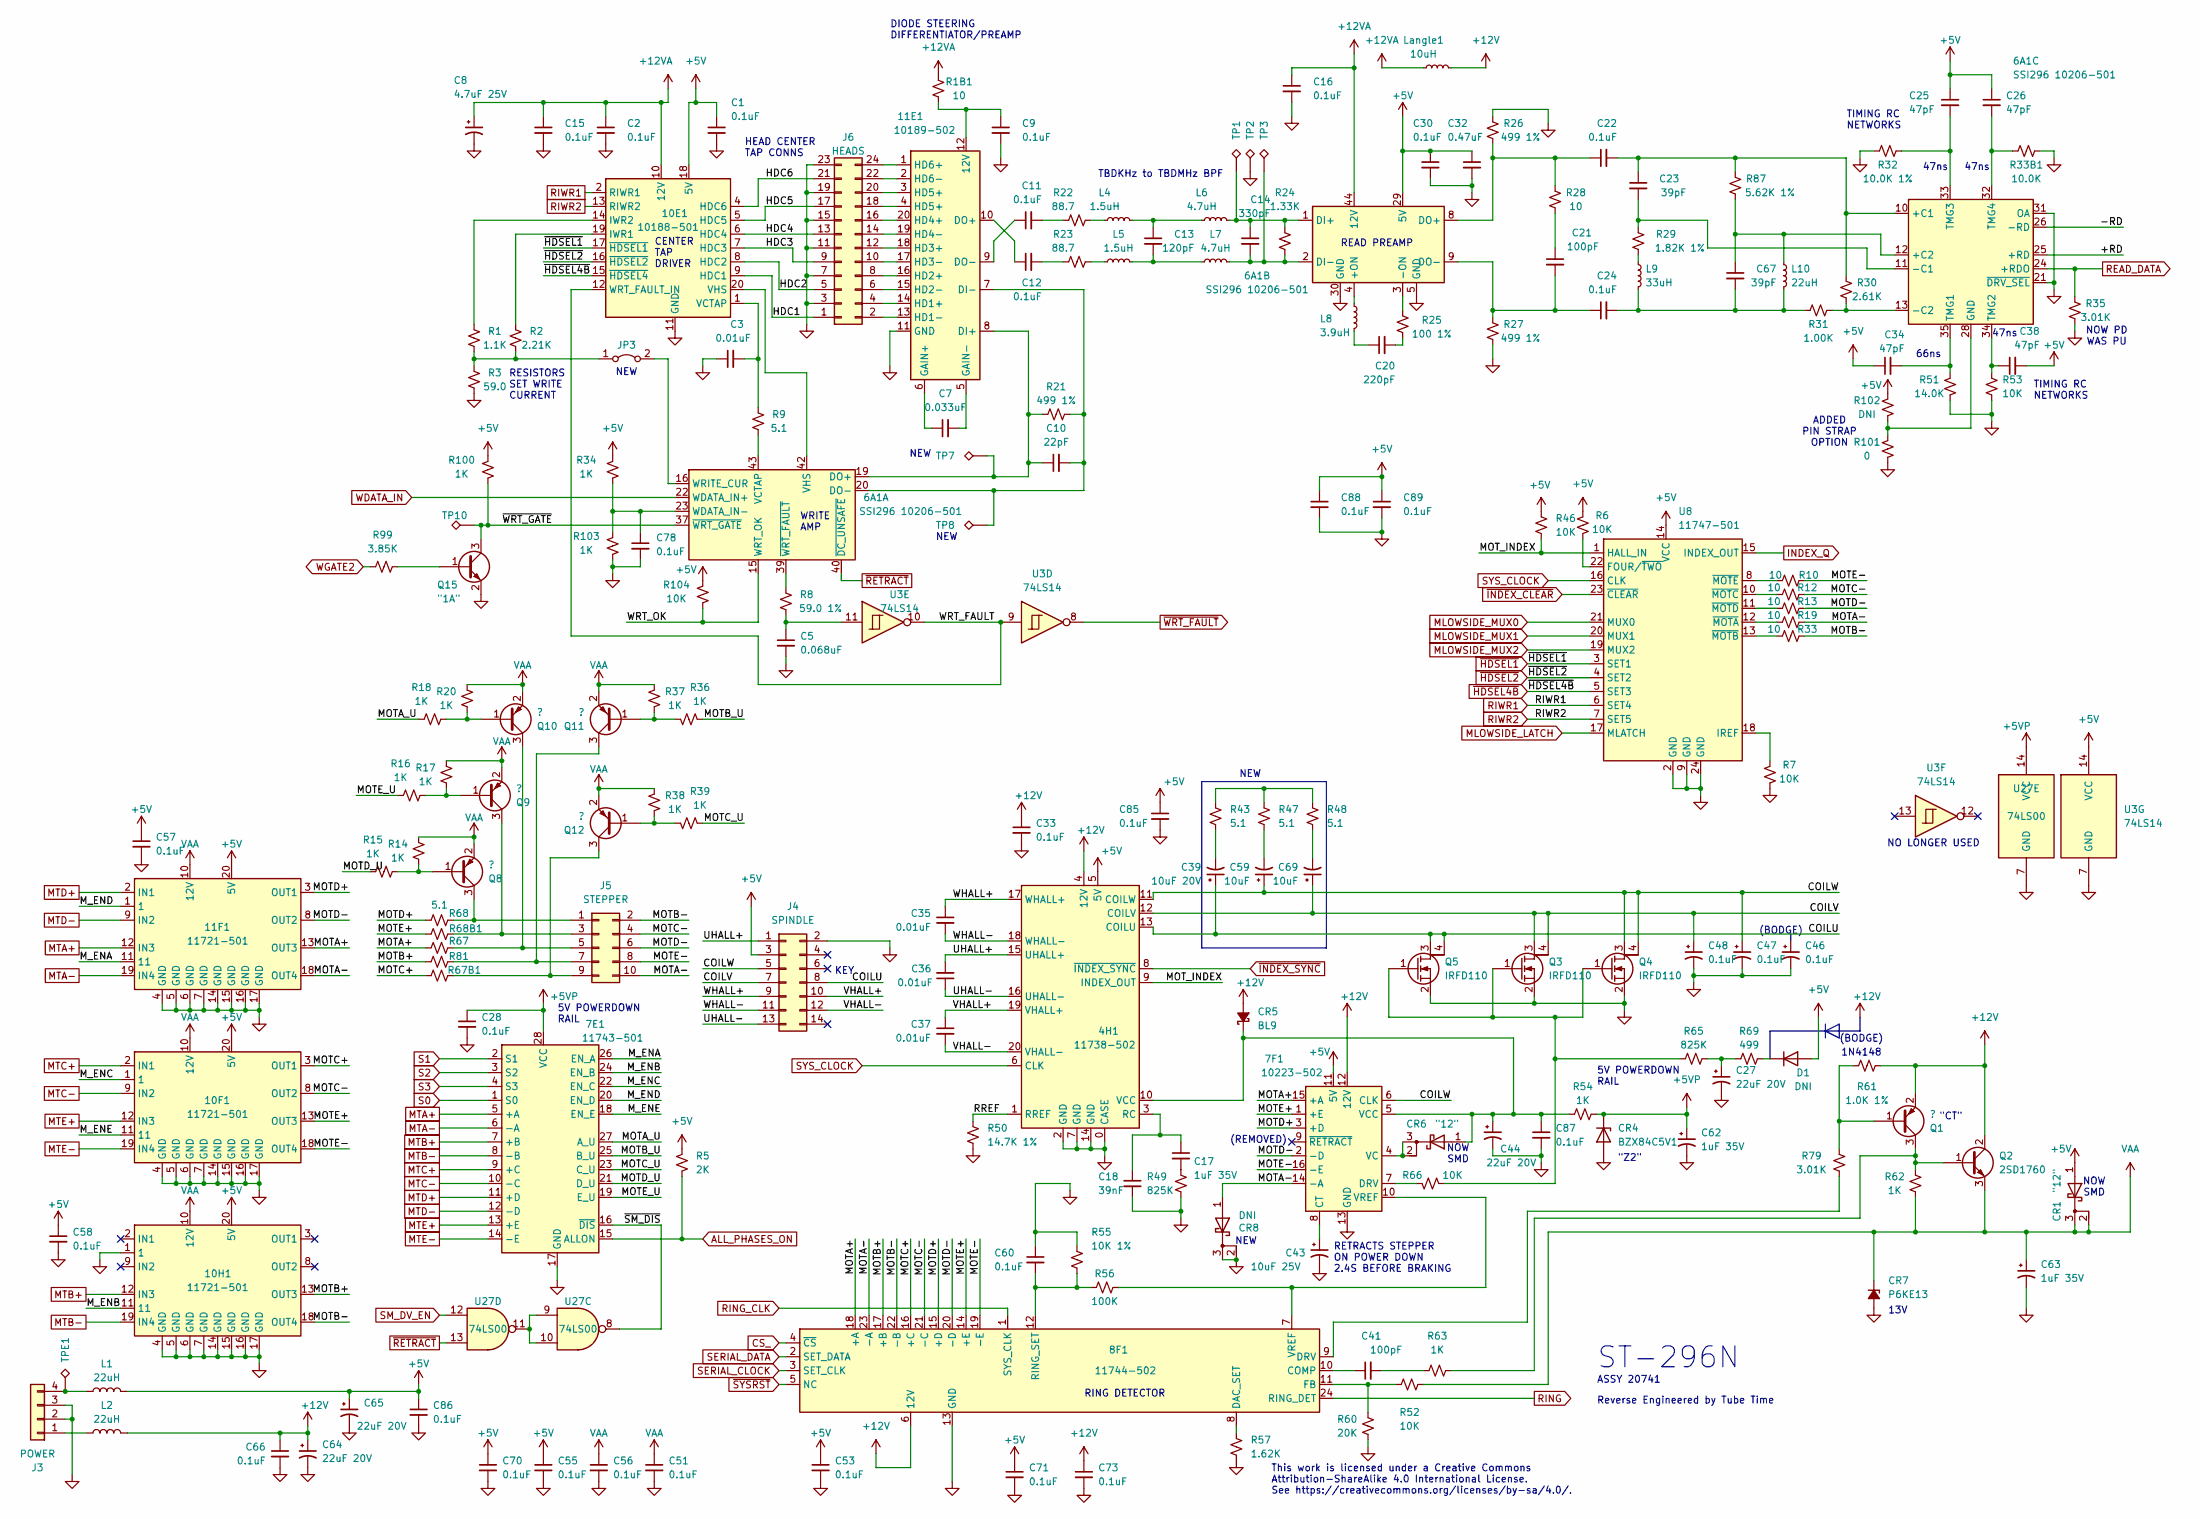
[picture p39: schematic analog.kicad_sch]

Parts:
4H1: 11738-502; MOT_DRIVE_SMT
6A1: SSI296 10206-501; PLCC-44_16.6x16.6mm_P1.27mm
7E1: 11743-501; SOP127P1070X255-28
7F1: 10223-502; SOP127P1065X265-16
8F1: 11744-502; SOIC-24W_7.5x15.4mm_P1.27mm
10E1: 10188-501; SOIC-20W_7.5x12.8mm_P1.27mm
10F1, 10H1, 11F1: 11721-501; SOP127P1065X265-20_SHRINK
11E1: 10189-502; SOIC-20W_7.5x12.8mm_P1.27mm
C1, C2, C9, C15, C16, C28, C30, C33, C51, C53, C55, C56, C57, C58, C60, C66, C70, C71, C73, C78, C85, C86, C87, C88, C89: 0.1uF; C_1206_3216Metric
C3, C35, C36, C37: 0.01uF; C_0805_2012Metric
C5: 0.068uF; C_1210_3225Metric
C7: 0.033uF; C_1206_3216Metric
C8: 4.7uF 25V; CP_EIA-7343-31_Kemet-D
C10: 22pF; C_0805_2012Metric
C11, C12, C22, C24: 0.1uF; C_1210_3225Metric
C13: 120pF; C_0805_2012Metric
C14: 330pF; C_0805_2012Metric
C17, C63: 1uF 35V; CP_EIA-3528-12_Kemet-T
C18: 39nF; C_1206_3216Metric
C20: 220pF; C_0805_2012Metric
C21, C41: 100pF; C_0805_2012Metric
C23, C67: 39pF; C_0805_2012Metric
C25, C26, C34, C38: 47pF; C_0805_2012Metric
C27, C44, C64, C65: 22uF 20V; CP_EIA-7343-31_Kemet-D
C32: 0.47uF; C_1812_4532Metric
C39: 10uF 20V; CP_EIA-7343-31_Kemet-D
C43: 10uF 25V; CP_EIA-7343-31_Kemet-D
C46, C47, C48: 0.1uF; CP_EIA-3216-10_Kemet-I
C59, C69: 10uF; CP_EIA-7343-31_Kemet-D
C62: 1uF 35V; CP_EIA-3216-10_Kemet-I
CR1, CR6: "12"; SOT-89-3
CR4: BZX84C5V1; SOT-23
CR5: BL9; D_DO-15_P15.24mm_Horizontal
CR7: P6KE13; D_DO-15_P15.24mm_Horizontal
CR8: DNI; SOT-89-3
D1: DNI; SOT-23-3
J3: POWER; Samtec_HPM-04-01-x-S_Straight_1x04_Pitch5.08mm
J4: SPINDLE; PinHeader_2x07_P2.54mm_Vertical
J5: STEPPER; PinHeader_2x05_P2.54mm_Vertical
J6: HEADS; PinHeader_2x12_P2.54mm_Vertical
JP3: Jumper_2_Bridged; SolderJumper-2_P1.3mm_Bridged_Pad1.0x1.5mm
L1, L2: 22uH; L_Axial_L13.0mm_D4.5mm_P15.24mm_Horizontal_Fastron_HCCC
L4, L5: 1.5uH; L_1206_3216Metric
L6, L7: 4.7uH; L_1206_3216Metric
L8: 3.9uH; L_1206_3216Metric
L9: 33uH; L_1206_3216Metric
L10: 22uH; L_1206_3216Metric
Langle1: 10uH; L_1206_3216Metric
Q1, Q8, Q9, Q10, Q11, Q12: ?; SOT95P230X117-3
Q2: 2SD1760; TO-252-2
Q3, Q4, Q5: IRFD110; DIP-4_W7.62mm
Q15: "1A"; SOT95P230X117-3
R1: 1.1K; R_1206_3216Metric
R1B1, R28: 10; R_1206_3216Metric
R2: 2.21K; R_1206_3216Metric
R3: 59.0; R_1206_3216Metric
R5: 2K; R_1206_3216Metric
R6, R7, R46, R52, R53, R66, R104: 10K; R_1206_3216Metric
R8: 59.0 1%; R_1206_3216Metric
R9: 5.1; R_1206_3216Metric
R10, R12, R13, R19, R33: 10; R_1210_3225Metric
R14, R15, R16, R17, R18, R20, R34, R36, R37, R38, R39, R54, R62, R63, R100, R103: 1K; R_1206_3216Metric
R21, R26, R27: 499 1%; R_1206_3216Metric
R22, R23: 88.7; R_1206_3216Metric
R24: 1.33K; R_1206_3216Metric
R25: 100 1%; R_1206_3216Metric
R29: 1.82K 1%; R_1206_3216Metric
R30: 2.61K; R_1206_3216Metric
R31: 1.00K; R_1206_3216Metric
R32: 10.0K 1%; R_1206_3216Metric
R33B1: 10.0K; R_1206_3216Metric
R35, R79: 3.01K; R_1206_3216Metric
R43, R47, R48: 5.1; R_1210_3225Metric
R49, R65: 825K; R_1206_3216Metric
R50: 14.7K 1%; R_1206_3216Metric
R51: 14.0K; R_1206_3216Metric
R55: 10K 1%; R_1206_3216Metric
R56: 100K; R_1206_3216Metric
R57: 1.62K; R_1206_3216Metric
R60: 20K; R_1206_3216Metric
R61: 1.0K 1%; R_1206_3216Metric
R67, R67B1, R68, R68B1, R81: 5.1; R_2512_6332Metric_Pad1.40x3.35mm_HandSolder
R69: 499; R_1206_3216Metric
R87: 5.62K 1%; R_1206_3216Metric
R99: 3.85K; R_1206_3216Metric
R101: 0; R_1206_3216Metric
R102: DNI; R_1206_3216Metric
TP1, TP2, TP3, TP10: 1/2 STEP; TestPoint_THTPad_1.5x1.5mm_Drill0.7mm
TP7, TP8: 1/2 STEP; TestPoint_THTPad_1.0x1.0mm_Drill0.5mm
TPE1: 1/2 STEP; TestPoint_THTPad_D2.5mm_Drill1.2mm
U3: 74LS14; SOP127P620X175-14_SHRINK
U8: 11747-501; SOP127P1250X255-24
U27: 74LS00; SOP127P620X175-14_SHRINK

Connections:
+5V: 4H1.5 (5V), 6A1.29 (5V), 7F1.11 (5V), 10E1.18 (5V), 10F1.20 (5V), 10H1.20 (5V), 11F1.20 (5V), C1.1, C25.1, C26.1, C30.1, C32.1, C34.1, C38.2, C53.1, C55.1, C57.1, C58.1, C65.1, C70.1, C71.1, C85.1, C86.1, C88.1, C89.1, CR1.1 (A), D1.1 (A), J4.3, L1.2, R5.1, R6.1, R34.1, R46.1, R100.1, R102.1, R104.1, U3.14 (VCC), U8.14 (VCC)
+5VP: 7E1.28 (VCC), C28.1, C62.1, CR4.3 (K), R54.1, U27.14 (VCC)
+12V: 4H1.4 (12V), 7F1.12 (12V), 8F1.6 (12V), C33.1, C64.1, C66.1, C73.1, CR5.2 (A), L2.2, Langle1.2, Q1.2 (E), Q2.2 (C), R61.1
+12VA: 6A1.44 (12V), 10E1.10 (12V), C2.1, C8.1, C15.1, C16.1, Langle1.1, R1B1.1
+RD: 6A1.25 (+RD)
-RD: 6A1.26 (-RD)
ALL_PHASES_ON: 7E1.15 (ALLON), R5.2
COILU: 4H1.13 (COILU), C39.1, J4.8, Q5.3 (D), Q5.4 (D)
COILV: 4H1.12 (COILV), C48.1, C69.1, J4.7, Q3.3 (D), Q3.4 (D)
COILW: 4H1.11 (COILW), 7F1.6 (CLK), C47.1, C59.1, J4.5, Q4.3 (D), Q4.4 (D)
CS_: 8F1.4 (~CS)
GND: 4H1.0 (CASE), 4H1.2 (GND), 4H1.7 (GND), 4H1.14 (GND), 6A1.5 (GND), 6A1.21 (~DRV_SEL), 6A1.30 (GND), 6A1.31 (OA), 7E1.17 (GND), 7F1.13 (GND), 8F1.13 (GND), 10E1.11 (GND), 10F1.4 (GND), 10F1.5 (GND), 10F1.6 (GND), 10F1.7 (GND), 10F1.14 (GND), 10F1.15 (GND), 10F1.16 (GND), 10F1.17 (GND), 10H1.1, 10H1.4 (GND), 10H1.5 (GND), 10H1.6 (GND), 10H1.7 (GND), 10H1.14 (GND), 10H1.15 (GND), 10H1.16 (GND), 10H1.17 (GND), 11E1.11 (GND), 11F1.4 (GND), 11F1.5 (GND), 11F1.6 (GND), 11F1.7 (GND), 11F1.14 (GND), 11F1.15 (GND), 11F1.16 (GND), 11F1.17 (GND), C1.2, C2.2, C3.1, C5.2, C8.2, C9.2, C15.2, C16.2, C18.2, C27.2, C28.2, C30.2, C32.2, C33.2, C43.2, C44.2, C46.2, C47.2, C48.2, C51.2, C53.2, C55.2, C56.2, C57.2, C58.2, C60.1, C62.2, C63.2, C64.2, C65.2, C66.2, C70.2, C71.2, C73.2, C78.2, C85.2, C86.2, C87.2, C88.2, C89.2, CR4.1 (A), CR7.2 (A), CR8.2 (K), CR8.3 (K), J3.2, J3.3, J4.2, J6.3, J6.7, J6.11, J6.15, J6.19, J6.23, Q3.2 (S), Q4.2 (S), Q5.2 (S), Q15.2 (E), R3.2, R7.2, R26.1, R27.2, R32.2, R33B1.1, R35.2, R49.1, R50.1, R51.2, R53.2, R55.2, R57.1, R60.1, R101.2, R103.2, TP2.1, U3.7 (GND), U8.2 (GND), U8.9 (GND), U8.24 (GND), U27.7 (GND)
HDC1: 10E1.9 (HDC1), J6.1
HDC2: 10E1.8 (HDC2), J6.5
HDC3: 10E1.7 (HDC3), J6.9
HDC4: 10E1.6 (HDC4), J6.13
HDC5: 10E1.5 (HDC5), J6.17
HDC6: 10E1.4 (HDC6), J6.21
INDEX_Q: U8.15 (INDEX_OUT)
MLOWSIDE_LATCH: U8.17 (MLATCH)
MLOWSIDE_MUX0: U8.21 (MUX0)
MLOWSIDE_MUX1: U8.20 (MUX1)
MLOWSIDE_MUX2: U8.19 (MUX2)
MOTA+: 7F1.15 (+A), 8F1.18 (+A), 11F1.13 (OUT3), R67.1
MOTA-: 7F1.14 (-A), 8F1.23 (-A), 11F1.18 (OUT4), CR8.1 (A), J5.10, R19.1
MOTA_U: 7E1.27 (A_U), R18.1
MOTB+: 8F1.17 (+B), 10H1.13 (OUT3), R81.1
MOTB-: 8F1.22 (-B), 10H1.18 (OUT4), J5.2, R33.1
MOTB_U: 7E1.25 (B_U), R36.1
MOTC+: 8F1.16 (+C), 10F1.3 (OUT1), R67B1.1
MOTC-: 8F1.21 (-C), 10F1.8 (OUT2), J5.4, R12.1
MOTC_U: 7E1.23 (C_U), R39.1
MOTD+: 7F1.3 (+D), 8F1.15 (+D), 11F1.3 (OUT1), R68.1
MOTD-: 7F1.2 (-D), 8F1.20 (-D), 11F1.8 (OUT2), J5.6, R13.1
MOTD_U: 7E1.21 (D_U), R15.1
MOTE+: 7F1.1 (+E), 8F1.14 (+E), 10F1.13 (OUT3), R68B1.1
MOTE-: 7F1.16 (-E), 8F1.19 (-E), 10F1.18 (OUT4), J5.8, R10.1
MOTE_U: 7E1.19 (E_U), R16.1
MOT_INDEX: 4H1.9 (INDEX_OUT), R46.2, U8.1 (HALL_IN)
MTA+: 7E1.5 (+A), 11F1.12 (IN3)
MTA-: 7E1.6 (-A), 11F1.19 (IN4)
MTB+: 7E1.7 (+B), 10H1.12 (IN3)
MTB-: 7E1.8 (-B), 10H1.19 (IN4)
MTC+: 7E1.9 (+C), 10F1.2 (IN1)
MTC-: 7E1.10 (-C), 10F1.9 (IN2)
MTD+: 7E1.11 (+D), 11F1.2 (IN1)
MTD-: 7E1.12 (-D), 11F1.9 (IN2)
MTE+: 7E1.13 (+E), 10F1.12 (IN3)
MTE-: 7E1.14 (-E), 10F1.19 (IN4)
M_ENA: 7E1.26 (EN_A), 11F1.11
M_ENB: 7E1.24 (EN_B), 10H1.11
M_ENC: 7E1.22 (EN_C), 10F1.1
M_END: 7E1.20 (EN_D), 11F1.1
M_ENE: 7E1.18 (EN_E), 10F1.11
unnamed: 4H1.3 (RC), C17.1, C18.1
unnamed: 4H1.10 (VCC), 7F1.5 (VCC), C44.1, C87.1, CR5.1 (K), CR6.1 (A), R54.2
unnamed: 6A1.1 (DI+), C14.1, L6.2, R24.1, TP1.1
unnamed: 6A1.2 (DI-), C14.2, L7.2, R24.2, TP3.1
unnamed: 6A1.3 (-ON), R25.1
unnamed: 6A1.4 (+ON), L8.1
unnamed: 6A1.8 (DO+), C22.1, R26.2, R28.1
unnamed: 6A1.9 (DO-), C21.2, C24.1, R27.1
unnamed: 6A1.10 (+C1), C22.2, C23.1, R30.1, R87.1
unnamed: 6A1.11 (-C1), C23.2, R29.1
unnamed: 6A1.12 (+C2), C67.1, L10.1, R87.2
unnamed: 6A1.13 (-C2), R30.2, R31.1
unnamed: 6A1.16 (WRITE_CUR), JP3.2 (B)
unnamed: 6A1.23 (WDATA_IN-), C78.1, R34.2, R103.1
unnamed: 6A1.28 (GND), R101.1, R102.2
unnamed: 6A1.32 (TMG4), C26.2, R33B1.2
unnamed: 6A1.33 (TMG3), C25.2, R32.1
unnamed: 6A1.34 (TMG2), C38.1, R53.1
unnamed: 6A1.35 (TMG1), C34.2, R51.1
unnamed: 6A1.39 (~WRT_FAULT), R8.2
unnamed: 6A1.43 (VCTAP), R9.1
unnamed: 7F1.4 (VC), CR6.2 (K), CR6.3 (K)
unnamed: 7F1.7 (DRV), R66.1
unnamed: 7F1.8 (CT), C43.1
unnamed: 7F1.10 (VREF), 8F1.7 (VREF), R56.2
unnamed: 8F1.8 (DAC_SET), R57.2
unnamed: 8F1.9 (DRV), R79.2
unnamed: 8F1.10 (COMP), C41.1
unnamed: 8F1.11 (FB), R52.2, R60.2
unnamed: 8F1.12 (RING_SET), C60.2, R55.1, R56.1
unnamed: 10E1.1 (VCTAP), C3.2, R9.2
unnamed: 10E1.14 (IWR2), R1.1
unnamed: 10E1.19 (IWR1), R2.1
unnamed: 6A1.42 (VHS), 10E1.20 (VHS)
unnamed: 11E1.1 (HD6+), J6.24
unnamed: 11E1.2 (HD6-), J6.22
unnamed: 11E1.3 (HD5+), J6.20
unnamed: 11E1.4 (HD5+), J6.18
unnamed: 11E1.5 (GAIN-), C7.2
unnamed: 11E1.6 (GAIN+), C7.1
unnamed: 6A1.20 (DO-), 11E1.7 (DI-), C10.2, R21.2, TP8.1
unnamed: 6A1.19 (DO+), 11E1.8 (DI+), C10.1, R21.1, TP7.1
unnamed: 11E1.9 (DO-), C11.1
unnamed: 11E1.10 (DO+), C12.1
unnamed: 11E1.12 (12V), C9.1, R1B1.2
unnamed: 11E1.13 (HD1-), J6.2
unnamed: 11E1.14 (HD1+), J6.4
unnamed: 11E1.15 (HD2-), J6.6
unnamed: 11E1.16 (HD2+), J6.8
unnamed: 11E1.17 (HD3-), J6.10
unnamed: 11E1.18 (HD3+), J6.12
unnamed: 11E1.19 (HD4-), J6.14
unnamed: 11E1.20 (HD4+), J6.16
unnamed: C5.1, R8.1, U3.11
unnamed: C11.2, R22.2
unnamed: C12.2, R23.2
unnamed: C13.1, L4.2, L6.1
unnamed: C13.2, L5.2, L7.1
unnamed: C17.2, R49.2
unnamed: C20.1, L8.2
unnamed: C20.2, R25.2
unnamed: C21.1, R28.2
unnamed: C24.2, C67.2, L9.2, L10.2, R31.2
unnamed: C27.1, R65.2, R69.1
unnamed: C39.2, R43.2
unnamed: C41.2, R63.2
unnamed: C59.2, R47.2
unnamed: C69.2, R48.2
unnamed: D1.3 (K), R69.2
unnamed: J3.1, L2.1
unnamed: J3.4, L1.1, TPE1.1
unnamed: J5.1, Q8.3 (C), R68.2
unnamed: J5.3, Q9.3 (C), R68B1.2
unnamed: J5.5, Q10.3 (C), R67.2
unnamed: J5.7, Q11.3 (C), R81.2
unnamed: J5.9, Q12.3 (C), R67B1.2
unnamed: JP3.1 (A), R1.2, R2.2, R3.1
unnamed: L4.1, R22.1
unnamed: L5.1, R23.1
unnamed: L9.1, R29.2
unnamed: Q1.1 (B), R61.2, R79.1
unnamed: Q1.3 (C), Q2.1 (B), R62.1, R63.1
unnamed: Q3.1 (G), Q4.1 (G), Q5.1 (G), R65.1, R66.2
unnamed: Q8.1 (B), R14.2, R15.2
unnamed: Q9.1 (B), R16.2, R17.2
unnamed: Q10.1 (B), R18.2, R20.2
unnamed: Q11.1 (B), R36.2, R37.2
unnamed: Q12.1 (B), R38.2, R39.2
unnamed: Q15.1 (B), R99.2
unnamed: R6.2, U8.22 (FOUR/~TWO)
unnamed: R7.1, U8.18 (IREF)
unnamed: R10.2, U8.8 (~MOTE)
unnamed: R12.2, U8.10 (~MOTC)
unnamed: R13.2, U8.11 (~MOTD)
unnamed: R19.2, U8.12 (~MOTA)
unnamed: R33.2, U8.13 (~MOTB)
unnamed: R43.1, R47.1, R48.1
unnamed: U27.9, U27.10, U27.11
READ_DATA: 6A1.24 (+RDO), R35.1
RING: 8F1.24 (RING_DET)
RING_CLK: 8F1.1 (SYS_CLK)
RIWR1: 10E1.2 (RIWR1), U8.6 (SET4)
RIWR2: 10E1.13 (RIWR2), U8.7 (SET5)
RREF: 4H1.1 (RREF), R50.2
S0: 7E1.1 (S0)
S1: 7E1.2 (S1)
S2: 7E1.3 (S2)
S3: 7E1.4 (S3)
SERIAL_CLOCK: 8F1.3 (SET_CLK)
SERIAL_DATA: 8F1.2 (SET_DATA)
SM_DV_EN: U27.12
SYS_CLOCK: 4H1.6 (CLK), U8.16 (CLK)
UHALL+: 4H1.15 (UHALL+), C36.2, J4.1
UHALL-: 4H1.16 (UHALL-), C36.1, J4.13
VAA: 10F1.10 (12V), 10H1.10 (12V), 11F1.10 (12V), C51.1, C56.1, C63.1, CR1.2 (K), CR1.3 (K), CR7.1 (K), Q2.3 (E), Q8.2 (E), Q9.2 (E), Q10.2 (E), Q11.2 (E), Q12.2 (E), R14.1, R17.1, R20.1, R37.1, R38.1, R52.1, R62.2
VHALL+: 4H1.19 (VHALL+), C37.1, J4.10
VHALL-: 4H1.20 (VHALL-), C37.2, J4.12
WDATA_IN: 6A1.22 (WDATA_IN+)
WGATE2: R99.1
WHALL+: 4H1.17 (WHALL+), C35.1, J4.9
WHALL-: 4H1.18 (WHALL-), C35.2, J4.11
WRT_FAULT: 10E1.12 (WRT_FAULT_IN), U3.9, U3.10
WRT_OK: 6A1.15 (WRT_OK), R104.2
~HDSEL1: 10E1.17 (~HDSEL1), U8.3 (SET1)
~HDSEL2: 10E1.16 (~HDSEL2), U8.4 (SET2)
~HDSEL4B: 10E1.15 (~HDSEL4), U8.5 (SET3)
~INDEX_CLEAR: U8.23 (~CLEAR)
~INDEX_SYNC: 4H1.8 (~INDEX_SYNC)
~RETRACT: 6A1.40 (~DC_UNSAFE), U27.13
~SM_DIS: 7E1.16 (~DIS), U27.8
~SYSRST: 8F1.5 (NC)
~WRT_FAULT: U3.8
~WRT_GATE: 6A1.37 (~WRT_GATE), Q15.3 (C), R100.2, TP10.1

Notes on the sheet:
NOW PD WAS PU
HEAD CENTER TAP CONNS
TIMING RC NETWORKS
NEW
TBDKHz to TBDMHz BPF
(BODGE)
KEY
"Z2"
ST-296N
47ns
RETRACTS STEPPER ON POWER DOWN 2.4S BEFORE BRAKING
(REMOVED)
1N4148
Reverse Engineered by Tube Time
ASSY 20741
ADDED PIN STRAP OPTION
NO LONGER USED
5V POWERDOWN RAIL
DIODE STEERING DIFFERENTIATOR/PREAMP
13V
RESISTORS SET WRITE CURRENT
NOW SMD
"CT"
66ns
WRITE AMP
CENTER TAP DRIVER
This work is licensed under a Creative Commons Attribution-ShareAlike 4.0 International License. See https://creativecommons.org/licenses/by-sa/4.0/.
READ PREAMP
RING DETECTOR
